James-Jiang0821/GLIDER/ROS2_TESTING/gnss_test_07-03-2026/all_topics.csv

topic | log_time_ns | type | message
/rosout | 1773075176267753863 | rcl_interfaces/msg/Log | Log(stamp=Time(sec=1773075176, nanosec=114152744), level=20, name=rosbag2_recorder, msg=Press SPACE for pausing/resuming, file=./src/rosbag2_transport/recorder.cpp, function=RecorderImpl, line=190)
/rosout | 1773075176267796273 | rcl_interfaces/msg/Log | Log(stamp=Time(sec=1773075176, nanosec=185886865), level=20, name=rosbag2_recorder, msg=Listening for topics..., file=./src/rosbag2_transport/recorder.cpp, function=record, line=353)
/rosout | 1773075176267808681 | rcl_interfaces/msg/Log | Log(stamp=Time(sec=1773075176, nanosec=186019447), level=20, name=rosbag2_recorder, msg=Event publisher thread: Starting, file=./src/rosbag2_transport/recorder.cpp, function=event_publisher_thread_main, line=371)
/rosout | 1773075176267809329 | rcl_interfaces/msg/Log | Log(stamp=Time(sec=1773075176, nanosec=198314175), level=20, name=rosbag2_recorder, msg=Subscribed to topic '/rosout', file=./src/rosbag2_transport/recorder.cpp, function=subscribe_topic, line=574)
/rosout | 1773075176267809792 | rcl_interfaces/msg/Log | Log(stamp=Time(sec=1773075176, nanosec=205440616), level=20, name=rosbag2_recorder, msg=Subscribed to topic '/parameter_events', file=./src/rosbag2_transport/recorder.cpp, function=subscribe_topic, line=574)
/rosout | 1773075176267810237 | rcl_interfaces/msg/Log | Log(stamp=Time(sec=1773075176, nanosec=246401098), level=20, name=rosbag2_recorder, msg=Subscribed to topic '/gps/vel', file=./src/rosbag2_transport/recorder.cpp, function=subscribe_topic, line=574)
/rosout | 1773075176275671092 | rcl_interfaces/msg/Log | Log(stamp=Time(sec=1773075176, nanosec=274873692), level=20, name=rosbag2_recorder, msg=Subscribed to topic '/gps/fix', file=./src/rosbag2_transport/recorder.cpp, function=subscribe_topic, line=574)
/gps/fix | 1773075176279690070 | sensor_msgs/msg/NavSatFix | NavSatFix(header=Header(stamp=Time(sec=1773075176, nanosec=278862577), frame_id=gps_link), status=NavSatStatus(status=0, service=1), latitude=51.476749299999994, longitude=-0.036789499999999996, altitude=6.122, position_covariance=[0.44488900000000003, 0.0, 0.0, 0.0, 0.44488900000000003, 0.0, 0.0, 0.0, 0.549081], position_covariance_type=2)
/gps/vel | 1773075176279978069 | geometry_msgs/msg/TwistStamped | TwistStamped(header=Header(stamp=Time(sec=1773075176, nanosec=278862577), frame_id=gps_link), twist=Twist(linear=Vector3(x=0.009, y=-0.013, z=0.001), angular=Vector3(x=0.0, y=0.0, z=0.0)))
/rosout | 1773075176301733450 | rcl_interfaces/msg/Log | Log(stamp=Time(sec=1773075176, nanosec=301534402), level=20, name=rosbag2_recorder, msg=Subscribed to topic '/gps/diagnostics', file=./src/rosbag2_transport/recorder.cpp, function=subscribe_topic, line=574)
/rosout | 1773075176308117218 | rcl_interfaces/msg/Log | Log(stamp=Time(sec=1773075176, nanosec=307944467), level=20, name=rosbag2_recorder, msg=Subscribed to topic '/events/write_split', file=./src/rosbag2_transport/recorder.cpp, function=subscribe_topic, line=574)
/rosout | 1773075176308825204 | rcl_interfaces/msg/Log | Log(stamp=Time(sec=1773075176, nanosec=308672102), level=20, name=rosbag2_recorder, msg=Recording..., file=./src/rosbag2_transport/recorder.cpp, function=record, line=365)
/gps/diagnostics | 1773075176682381984 | diagnostic_msgs/msg/DiagnosticArray | DiagnosticArray(header=Header(stamp=Time(sec=1773075176, nanosec=681566306), frame_id=), status=[DiagnosticStatus(level=0, name=gnss_maxm10s_i2c, message=OK, hardware_id=, values=[KeyValue(key=i2c_addr, value=0x42), KeyValue(key=avail_bytes_last_poll, value=0), KeyValue(key=age_s_since_last_pvt, value=0.40)])])
/gps/fix | 1773075177319579433 | sensor_msgs/msg/NavSatFix | NavSatFix(header=Header(stamp=Time(sec=1773075177, nanosec=318641104), frame_id=gps_link), status=NavSatStatus(status=0, service=1), latitude=51.4767465, longitude=-0.0367898, altitude=6.153, position_covariance=[0.42510400000000004, 0.0, 0.0, 0.0, 0.42510400000000004, 0.0, 0.0, 0.0, 0.5476], position_covariance_type=2)
/gps/vel | 1773075177320142111 | geometry_msgs/msg/TwistStamped | TwistStamped(header=Header(stamp=Time(sec=1773075177, nanosec=318641104), frame_id=gps_link), twist=Twist(linear=Vector3(x=0.006, y=-0.018, z=0.017), angular=Vector3(x=0.0, y=0.0, z=0.0)))
/gps/fix | 1773075178324664052 | sensor_msgs/msg/NavSatFix | NavSatFix(header=Header(stamp=Time(sec=1773075178, nanosec=323694653), frame_id=gps_link), status=NavSatStatus(status=0, service=1), latitude=51.4767467, longitude=-0.036789999999999996, altitude=6.231, position_covariance=[0.418609, 0.0, 0.0, 0.0, 0.418609, 0.0, 0.0, 0.0, 0.540225], position_covariance_type=2)
/gps/vel | 1773075178325083165 | geometry_msgs/msg/TwistStamped | TwistStamped(header=Header(stamp=Time(sec=1773075178, nanosec=323694653), frame_id=gps_link), twist=Twist(linear=Vector3(x=-0.004, y=-0.003, z=0.009), angular=Vector3(x=0.0, y=0.0, z=0.0)))
/gps/diagnostics | 1773075178325927132 | diagnostic_msgs/msg/DiagnosticArray | DiagnosticArray(header=Header(stamp=Time(sec=1773075178, nanosec=325338196), frame_id=), status=[DiagnosticStatus(level=0, name=gnss_maxm10s_i2c, message=OK, hardware_id=, values=[KeyValue(key=i2c_addr, value=0x42), KeyValue(key=avail_bytes_last_poll, value=100), KeyValue(key=age_s_since_last_pvt, value=0.00)])])
/gps/fix | 1773075179575138285 | sensor_msgs/msg/NavSatFix | NavSatFix(header=Header(stamp=Time(sec=1773075179, nanosec=574176854), frame_id=gps_link), status=NavSatStatus(status=0, service=1), latitude=51.4767471, longitude=-0.0367898, altitude=6.245, position_covariance=[0.41602500000000003, 0.0, 0.0, 0.0, 0.41602500000000003, 0.0, 0.0, 0.0, 0.535824], position_covariance_type=2)
/gps/vel | 1773075179575577231 | geometry_msgs/msg/TwistStamped | TwistStamped(header=Header(stamp=Time(sec=1773075179, nanosec=574176854), frame_id=gps_link), twist=Twist(linear=Vector3(x=-0.02, y=0.027, z=-0.0), angular=Vector3(x=0.0, y=0.0, z=0.0)))
/gps/fix | 1773075180360670753 | sensor_msgs/msg/NavSatFix | NavSatFix(header=Header(stamp=Time(sec=1773075180, nanosec=359713105), frame_id=gps_link), status=NavSatStatus(status=0, service=1), latitude=51.4767477, longitude=-0.0367901, altitude=6.276, position_covariance=[0.4096, 0.0, 0.0, 0.0, 0.4096, 0.0, 0.0, 0.0, 0.527076], position_covariance_type=2)
/gps/vel | 1773075180361079047 | geometry_msgs/msg/TwistStamped | TwistStamped(header=Header(stamp=Time(sec=1773075180, nanosec=359713105), frame_id=gps_link), twist=Twist(linear=Vector3(x=-0.012, y=0.021, z=-0.015), angular=Vector3(x=0.0, y=0.0, z=0.0)))
/gps/fix | 1773075181483030007 | sensor_msgs/msg/NavSatFix | NavSatFix(header=Header(stamp=Time(sec=1773075181, nanosec=482054844), frame_id=gps_link), status=NavSatStatus(status=0, service=1), latitude=51.4767489, longitude=-0.0367898, altitude=6.306, position_covariance=[0.403225, 0.0, 0.0, 0.0, 0.403225, 0.0, 0.0, 0.0, 0.524176], position_covariance_type=2)
/gps/vel | 1773075181483443521 | geometry_msgs/msg/TwistStamped | TwistStamped(header=Header(stamp=Time(sec=1773075181, nanosec=482054844), frame_id=gps_link), twist=Twist(linear=Vector3(x=-0.018, y=0.031, z=-0.003), angular=Vector3(x=0.0, y=0.0, z=0.0)))
/gps/fix | 1773075182256259807 | sensor_msgs/msg/NavSatFix | NavSatFix(header=Header(stamp=Time(sec=1773075182, nanosec=255231499), frame_id=gps_link), status=NavSatStatus(status=0, service=1), latitude=51.4767498, longitude=-0.036788999999999995, altitude=6.236, position_covariance=[0.398161, 0.0, 0.0, 0.0, 0.398161, 0.0, 0.0, 0.0, 0.512656], position_covariance_type=2)
/gps/vel | 1773075182256685746 | geometry_msgs/msg/TwistStamped | TwistStamped(header=Header(stamp=Time(sec=1773075182, nanosec=255231499), frame_id=gps_link), twist=Twist(linear=Vector3(x=-0.019, y=0.032, z=-0.013), angular=Vector3(x=0.0, y=0.0, z=0.0)))
/gps/fix | 1773075183410505809 | sensor_msgs/msg/NavSatFix | NavSatFix(header=Header(stamp=Time(sec=1773075183, nanosec=409542043), frame_id=gps_link), status=NavSatStatus(status=0, service=1), latitude=51.476751799999995, longitude=-0.0367877, altitude=6.231, position_covariance=[0.386884, 0.0, 0.0, 0.0, 0.386884, 0.0, 0.0, 0.0, 0.5041], position_covariance_type=2)
/gps/vel | 1773075183410922875 | geometry_msgs/msg/TwistStamped | TwistStamped(header=Header(stamp=Time(sec=1773075183, nanosec=409542043), frame_id=gps_link), twist=Twist(linear=Vector3(x=0.0, y=-0.006, z=-0.009), angular=Vector3(x=0.0, y=0.0, z=0.0)))
/gps/fix | 1773075184532103208 | sensor_msgs/msg/NavSatFix | NavSatFix(header=Header(stamp=Time(sec=1773075184, nanosec=531132298), frame_id=gps_link), status=NavSatStatus(status=0, service=1), latitude=51.4767521, longitude=-0.0367876, altitude=6.212, position_covariance=[0.3844, 0.0, 0.0, 0.0, 0.3844, 0.0, 0.0, 0.0, 0.4914009999999999], position_covariance_type=2)
/gps/vel | 1773075184532553754 | geometry_msgs/msg/TwistStamped | TwistStamped(header=Header(stamp=Time(sec=1773075184, nanosec=531132298), frame_id=gps_link), twist=Twist(linear=Vector3(x=0.001, y=-0.006, z=-0.006), angular=Vector3(x=0.0, y=0.0, z=0.0)))
/gps/fix | 1773075186392691532 | sensor_msgs/msg/NavSatFix | NavSatFix(header=Header(stamp=Time(sec=1773075186, nanosec=391800354), frame_id=gps_link), status=NavSatStatus(status=0, service=1), latitude=51.4767528, longitude=-0.036787799999999996, altitude=6.299, position_covariance=[0.381924, 0.0, 0.0, 0.0, 0.381924, 0.0, 0.0, 0.0, 0.48999999999999994], position_covariance_type=2)
/gps/vel | 1773075186393330059 | geometry_msgs/msg/TwistStamped | TwistStamped(header=Header(stamp=Time(sec=1773075186, nanosec=391800354), frame_id=gps_link), twist=Twist(linear=Vector3(x=-0.001, y=-0.01, z=0.002), angular=Vector3(x=0.0, y=0.0, z=0.0)))
/gps/fix | 1773075188512592137 | sensor_msgs/msg/NavSatFix | NavSatFix(header=Header(stamp=Time(sec=1773075188, nanosec=511513798), frame_id=gps_link), status=NavSatStatus(status=0, service=1), latitude=51.4767533, longitude=-0.036787099999999996, altitude=6.353, position_covariance=[0.394384, 0.0, 0.0, 0.0, 0.394384, 0.0, 0.0, 0.0, 0.505521], position_covariance_type=2)
/gps/vel | 1773075188513144603 | geometry_msgs/msg/TwistStamped | TwistStamped(header=Header(stamp=Time(sec=1773075188, nanosec=511513798), frame_id=gps_link), twist=Twist(linear=Vector3(x=-0.004, y=-0.017, z=-0.019), angular=Vector3(x=0.0, y=0.0, z=0.0)))
/gps/fix | 1773075189256715920 | sensor_msgs/msg/NavSatFix | NavSatFix(header=Header(stamp=Time(sec=1773075189, nanosec=255613936), frame_id=gps_link), status=NavSatStatus(status=0, service=1), latitude=51.4767535, longitude=-0.0367868, altitude=6.377, position_covariance=[0.398161, 0.0, 0.0, 0.0, 0.398161, 0.0, 0.0, 0.0, 0.5184], position_covariance_type=2)
/gps/vel | 1773075189257145272 | geometry_msgs/msg/TwistStamped | TwistStamped(header=Header(stamp=Time(sec=1773075189, nanosec=255613936), frame_id=gps_link), twist=Twist(linear=Vector3(x=0.004, y=-0.018, z=-0.001), angular=Vector3(x=0.0, y=0.0, z=0.0)))
/gps/fix | 1773075190326882189 | sensor_msgs/msg/NavSatFix | NavSatFix(header=Header(stamp=Time(sec=1773075190, nanosec=325930839), frame_id=gps_link), status=NavSatStatus(status=0, service=1), latitude=51.4767538, longitude=-0.0367867, altitude=6.434, position_covariance=[0.405769, 0.0, 0.0, 0.0, 0.405769, 0.0, 0.0, 0.0, 0.5314409999999999], position_covariance_type=2)
/gps/vel | 1773075190327313040 | geometry_msgs/msg/TwistStamped | TwistStamped(header=Header(stamp=Time(sec=1773075190, nanosec=325930839), frame_id=gps_link), twist=Twist(linear=Vector3(x=-0.016, y=-0.006, z=0.048), angular=Vector3(x=0.0, y=0.0, z=0.0)))
/gps/fix | 1773075192250818999 | sensor_msgs/msg/NavSatFix | NavSatFix(header=Header(stamp=Time(sec=1773075192, nanosec=250206430), frame_id=gps_link), status=NavSatStatus(status=0, service=1), latitude=51.4767552, longitude=-0.0367868, altitude=6.494, position_covariance=[0.417316, 0.0, 0.0, 0.0, 0.417316, 0.0, 0.0, 0.0, 0.556516], position_covariance_type=2)
/gps/vel | 1773075192251108238 | geometry_msgs/msg/TwistStamped | TwistStamped(header=Header(stamp=Time(sec=1773075192, nanosec=250206430), frame_id=gps_link), twist=Twist(linear=Vector3(x=0.007, y=0.011, z=0.026), angular=Vector3(x=0.0, y=0.0, z=0.0)))
/parameter_events | 1773075192894638845 | rcl_interfaces/msg/ParameterEvent | ParameterEvent(stamp=Time(sec=1773075192, nanosec=893949888), node=/_ros2cli_1362, new_parameters=[Parameter(name=use_sim_time, value=ParameterValue(type=1, bool_value=False, integer_value=0, double_value=0.0, string_value=, byte_array_value=b'', bool_array_value=[], integer_array_value=[], double_array_value=[], string_array_value=[]))], changed_parameters=[], deleted_parameters=[])
/parameter_events | 1773075192895375209 | rcl_interfaces/msg/ParameterEvent | ParameterEvent(stamp=Time(sec=1773075192, nanosec=894891380), node=/_ros2cli_1362, new_parameters=[Parameter(name=start_type_description_service, value=ParameterValue(type=1, bool_value=True, integer_value=0, double_value=0.0, string_value=, byte_array_value=b'', bool_array_value=[], integer_array_value=[], double_array_value=[], string_array_value=[]))], changed_parameters=[], deleted_parameters=[])
/gps/fix | 1773075193332485841 | sensor_msgs/msg/NavSatFix | NavSatFix(header=Header(stamp=Time(sec=1773075193, nanosec=331677165), frame_id=gps_link), status=NavSatStatus(status=0, service=1), latitude=51.4767558, longitude=-0.0367867, altitude=6.525, position_covariance=[0.43428100000000003, 0.0, 0.0, 0.0, 0.43428100000000003, 0.0, 0.0, 0.0, 0.574564], position_covariance_type=2)
/gps/vel | 1773075193333139278 | geometry_msgs/msg/TwistStamped | TwistStamped(header=Header(stamp=Time(sec=1773075193, nanosec=331677165), frame_id=gps_link), twist=Twist(linear=Vector3(x=-0.004, y=0.022, z=0.047), angular=Vector3(x=0.0, y=0.0, z=0.0)))
/gps/fix | 1773075194177165361 | sensor_msgs/msg/NavSatFix | NavSatFix(header=Header(stamp=Time(sec=1773075194, nanosec=176581684), frame_id=gps_link), status=NavSatStatus(status=0, service=1), latitude=51.476756599999995, longitude=-0.036787, altitude=6.555, position_covariance=[0.438244, 0.0, 0.0, 0.0, 0.438244, 0.0, 0.0, 0.0, 0.586756], position_covariance_type=2)
/gps/vel | 1773075194178440564 | geometry_msgs/msg/TwistStamped | TwistStamped(header=Header(stamp=Time(sec=1773075194, nanosec=176581684), frame_id=gps_link), twist=Twist(linear=Vector3(x=-0.01, y=0.01, z=0.025), angular=Vector3(x=0.0, y=0.0, z=0.0)))
/parameter_events | 1773075194542956376 | rcl_interfaces/msg/ParameterEvent | ParameterEvent(stamp=Time(sec=1773075194, nanosec=542249905), node=/_ros2cli_daemon_0_14923d5e72164b54a0d396fbd3f56f5b, new_parameters=[Parameter(name=use_sim_time, value=ParameterValue(type=1, bool_value=False, integer_value=0, double_value=0.0, string_value=, byte_array_value=b'', bool_array_value=[], integer_array_value=[], double_array_value=[], string_array_value=[]))], changed_parameters=[], deleted_parameters=[])
/parameter_events | 1773075194543657199 | rcl_interfaces/msg/ParameterEvent | ParameterEvent(stamp=Time(sec=1773075194, nanosec=543186095), node=/_ros2cli_daemon_0_14923d5e72164b54a0d396fbd3f56f5b, new_parameters=[Parameter(name=start_type_description_service, value=ParameterValue(type=1, bool_value=False, integer_value=0, double_value=0.0, string_value=, byte_array_value=b'', bool_array_value=[], integer_array_value=[], double_array_value=[], string_array_value=[]))], changed_parameters=[], deleted_parameters=[])
/gps/fix | 1773075195590996326 | sensor_msgs/msg/NavSatFix | NavSatFix(header=Header(stamp=Time(sec=1773075195, nanosec=589900012), frame_id=gps_link), status=NavSatStatus(status=0, service=1), latitude=51.476757199999994, longitude=-0.0367872, altitude=6.639, position_covariance=[0.438244, 0.0, 0.0, 0.0, 0.438244, 0.0, 0.0, 0.0, 0.571536], position_covariance_type=2)
/gps/vel | 1773075195591612945 | geometry_msgs/msg/TwistStamped | TwistStamped(header=Header(stamp=Time(sec=1773075195, nanosec=589900012), frame_id=gps_link), twist=Twist(linear=Vector3(x=0.0, y=-0.004, z=-0.003), angular=Vector3(x=0.0, y=0.0, z=0.0)))
/gps/fix | 1773075196326046522 | sensor_msgs/msg/NavSatFix | NavSatFix(header=Header(stamp=Time(sec=1773075196, nanosec=325157096), frame_id=gps_link), status=NavSatStatus(status=0, service=1), latitude=51.4767574, longitude=-0.0367867, altitude=6.682, position_covariance=[0.43033600000000005, 0.0, 0.0, 0.0, 0.43033600000000005, 0.0, 0.0, 0.0, 0.565504], position_covariance_type=2)
/gps/vel | 1773075196326765230 | geometry_msgs/msg/TwistStamped | TwistStamped(header=Header(stamp=Time(sec=1773075196, nanosec=325157096), frame_id=gps_link), twist=Twist(linear=Vector3(x=0.003, y=-0.007, z=0.004), angular=Vector3(x=0.0, y=0.0, z=0.0)))
/gps/fix | 1773075197480508623 | sensor_msgs/msg/NavSatFix | NavSatFix(header=Header(stamp=Time(sec=1773075197, nanosec=479530628), frame_id=gps_link), status=NavSatStatus(status=0, service=1), latitude=51.4767581, longitude=-0.0367868, altitude=6.718, position_covariance=[0.42510400000000004, 0.0, 0.0, 0.0, 0.42510400000000004, 0.0, 0.0, 0.0, 0.552049], position_covariance_type=2)
/gps/vel | 1773075197481051073 | geometry_msgs/msg/TwistStamped | TwistStamped(header=Header(stamp=Time(sec=1773075197, nanosec=479530628), frame_id=gps_link), twist=Twist(linear=Vector3(x=-0.001, y=-0.004, z=0.01), angular=Vector3(x=0.0, y=0.0, z=0.0)))
/gps/fix | 1773075198638917330 | sensor_msgs/msg/NavSatFix | NavSatFix(header=Header(stamp=Time(sec=1773075198, nanosec=637934726), frame_id=gps_link), status=NavSatStatus(status=0, service=1), latitude=51.4767586, longitude=-0.036787299999999995, altitude=6.695, position_covariance=[0.42250000000000004, 0.0, 0.0, 0.0, 0.42250000000000004, 0.0, 0.0, 0.0, 0.549081], position_covariance_type=2)
/gps/vel | 1773075198639714827 | geometry_msgs/msg/TwistStamped | TwistStamped(header=Header(stamp=Time(sec=1773075198, nanosec=637934726), frame_id=gps_link), twist=Twist(linear=Vector3(x=-0.009, y=-0.007, z=-0.008), angular=Vector3(x=0.0, y=0.0, z=0.0)))
/gps/fix | 1773075199389900629 | sensor_msgs/msg/NavSatFix | NavSatFix(header=Header(stamp=Time(sec=1773075199, nanosec=388930620), frame_id=gps_link), status=NavSatStatus(status=0, service=1), latitude=51.4767601, longitude=-0.0367882, altitude=6.654, position_covariance=[0.41473600000000005, 0.0, 0.0, 0.0, 0.41473600000000005, 0.0, 0.0, 0.0, 0.538756], position_covariance_type=2)
/gps/vel | 1773075199390495464 | geometry_msgs/msg/TwistStamped | TwistStamped(header=Header(stamp=Time(sec=1773075199, nanosec=388930620), frame_id=gps_link), twist=Twist(linear=Vector3(x=-0.01, y=-0.001, z=-0.029), angular=Vector3(x=0.0, y=0.0, z=0.0)))
/gps/fix | 1773075200532812806 | sensor_msgs/msg/NavSatFix | NavSatFix(header=Header(stamp=Time(sec=1773075200, nanosec=531825967), frame_id=gps_link), status=NavSatStatus(status=0, service=1), latitude=51.4767611, longitude=-0.036788799999999997, altitude=6.599, position_covariance=[0.410881, 0.0, 0.0, 0.0, 0.410881, 0.0, 0.0, 0.0, 0.5285289999999999], position_covariance_type=2)
/gps/vel | 1773075200533380399 | geometry_msgs/msg/TwistStamped | TwistStamped(header=Header(stamp=Time(sec=1773075200, nanosec=531825967), frame_id=gps_link), twist=Twist(linear=Vector3(x=-0.005, y=0.001, z=0.005), angular=Vector3(x=0.0, y=0.0, z=0.0)))
/gps/fix | 1773075201268630556 | sensor_msgs/msg/NavSatFix | NavSatFix(header=Header(stamp=Time(sec=1773075201, nanosec=267495113), frame_id=gps_link), status=NavSatStatus(status=0, service=1), latitude=51.4767625, longitude=-0.0367893, altitude=6.618, position_covariance=[0.4096, 0.0, 0.0, 0.0, 0.4096, 0.0, 0.0, 0.0, 0.522729], position_covariance_type=2)
/gps/vel | 1773075201269184815 | geometry_msgs/msg/TwistStamped | TwistStamped(header=Header(stamp=Time(sec=1773075201, nanosec=267495113), frame_id=gps_link), twist=Twist(linear=Vector3(x=-0.009, y=0.014, z=0.018), angular=Vector3(x=0.0, y=0.0, z=0.0)))
/gps/fix | 1773075202412350741 | sensor_msgs/msg/NavSatFix | NavSatFix(header=Header(stamp=Time(sec=1773075202, nanosec=411360814), frame_id=gps_link), status=NavSatStatus(status=0, service=1), latitude=51.4767635, longitude=-0.0367901, altitude=6.497, position_covariance=[0.405769, 0.0, 0.0, 0.0, 0.405769, 0.0, 0.0, 0.0, 0.5097959999999999], position_covariance_type=2)
/gps/vel | 1773075202413137712 | geometry_msgs/msg/TwistStamped | TwistStamped(header=Header(stamp=Time(sec=1773075202, nanosec=411360814), frame_id=gps_link), twist=Twist(linear=Vector3(x=-0.015, y=-0.002, z=-0.005), angular=Vector3(x=0.0, y=0.0, z=0.0)))
/gps/fix | 1773075203525921727 | sensor_msgs/msg/NavSatFix | NavSatFix(header=Header(stamp=Time(sec=1773075203, nanosec=524950617), frame_id=gps_link), status=NavSatStatus(status=0, service=1), latitude=51.4767643, longitude=-0.0367918, altitude=6.291, position_covariance=[0.403225, 0.0, 0.0, 0.0, 0.403225, 0.0, 0.0, 0.0, 0.5041], position_covariance_type=2)
/gps/vel | 1773075203526489094 | geometry_msgs/msg/TwistStamped | TwistStamped(header=Header(stamp=Time(sec=1773075203, nanosec=524950617), frame_id=gps_link), twist=Twist(linear=Vector3(x=-0.011, y=0.032, z=-0.028), angular=Vector3(x=0.0, y=0.0, z=0.0)))
/gps/fix | 1773075204486615209 | sensor_msgs/msg/NavSatFix | NavSatFix(header=Header(stamp=Time(sec=1773075204, nanosec=485646619), frame_id=gps_link), status=NavSatStatus(status=0, service=1), latitude=51.4767619, longitude=-0.0367928, altitude=6.261, position_covariance=[0.408321, 0.0, 0.0, 0.0, 0.408321, 0.0, 0.0, 0.0, 0.537289], position_covariance_type=2)
/gps/vel | 1773075204487162669 | geometry_msgs/msg/TwistStamped | TwistStamped(header=Header(stamp=Time(sec=1773075204, nanosec=485646619), frame_id=gps_link), twist=Twist(linear=Vector3(x=-0.054, y=-0.562, z=-0.067), angular=Vector3(x=0.0, y=0.0, z=0.0)))
/gps/fix | 1773075206537593513 | sensor_msgs/msg/NavSatFix | NavSatFix(header=Header(stamp=Time(sec=1773075206, nanosec=536610242), frame_id=gps_link), status=NavSatStatus(status=0, service=1), latitude=51.4767632, longitude=-0.036789999999999996, altitude=5.983, position_covariance=[0.527076, 0.0, 0.0, 0.0, 0.527076, 0.0, 0.0, 0.0, 0.6384010000000001], position_covariance_type=2)
/gps/vel | 1773075206538325202 | geometry_msgs/msg/TwistStamped | TwistStamped(header=Header(stamp=Time(sec=1773075206, nanosec=536610242), frame_id=gps_link), twist=Twist(linear=Vector3(x=-0.041, y=0.164, z=-0.249), angular=Vector3(x=0.0, y=0.0, z=0.0)))
/gps/fix | 1773075207285232342 | sensor_msgs/msg/NavSatFix | NavSatFix(header=Header(stamp=Time(sec=1773075207, nanosec=284310275), frame_id=gps_link), status=NavSatStatus(status=0, service=1), latitude=51.4767654, longitude=-0.0367899, altitude=6.087, position_covariance=[0.522729, 0.0, 0.0, 0.0, 0.522729, 0.0, 0.0, 0.0, 0.664225], position_covariance_type=2)
/gps/vel | 1773075207285760521 | geometry_msgs/msg/TwistStamped | TwistStamped(header=Header(stamp=Time(sec=1773075207, nanosec=284310275), frame_id=gps_link), twist=Twist(linear=Vector3(x=-0.007, y=0.085, z=0.05), angular=Vector3(x=0.0, y=0.0, z=0.0)))
/gps/fix | 1773075208330469221 | sensor_msgs/msg/NavSatFix | NavSatFix(header=Header(stamp=Time(sec=1773075208, nanosec=329590393), frame_id=gps_link), status=NavSatStatus(status=0, service=1), latitude=51.4767659, longitude=-0.0367934, altitude=6.191, position_covariance=[0.522729, 0.0, 0.0, 0.0, 0.522729, 0.0, 0.0, 0.0, 0.6691239999999999], position_covariance_type=2)
/gps/vel | 1773075208330979325 | geometry_msgs/msg/TwistStamped | TwistStamped(header=Header(stamp=Time(sec=1773075208, nanosec=329590393), frame_id=gps_link), twist=Twist(linear=Vector3(x=-0.22, y=-0.263, z=0.116), angular=Vector3(x=0.0, y=0.0, z=0.0)))
/gps/fix | 1773075209425174332 | sensor_msgs/msg/NavSatFix | NavSatFix(header=Header(stamp=Time(sec=1773075209, nanosec=424203456), frame_id=gps_link), status=NavSatStatus(status=0, service=1), latitude=51.476766, longitude=-0.0367962, altitude=6.328, position_covariance=[0.49420899999999995, 0.0, 0.0, 0.0, 0.49420899999999995, 0.0, 0.0, 0.0, 0.6528640000000001], position_covariance_type=2)
/gps/vel | 1773075209425749803 | geometry_msgs/msg/TwistStamped | TwistStamped(header=Header(stamp=Time(sec=1773075209, nanosec=424203456), frame_id=gps_link), twist=Twist(linear=Vector3(x=-0.033, y=-0.129, z=-0.021), angular=Vector3(x=0.0, y=0.0, z=0.0)))
/gps/fix | 1773075210520372236 | sensor_msgs/msg/NavSatFix | NavSatFix(header=Header(stamp=Time(sec=1773075210, nanosec=519372382), frame_id=gps_link), status=NavSatStatus(status=0, service=1), latitude=51.476768, longitude=-0.036798, altitude=6.403, position_covariance=[0.4830249999999999, 0.0, 0.0, 0.0, 0.4830249999999999, 0.0, 0.0, 0.0, 0.6691239999999999], position_covariance_type=2)
/gps/vel | 1773075210520875691 | geometry_msgs/msg/TwistStamped | TwistStamped(header=Header(stamp=Time(sec=1773075210, nanosec=519372382), frame_id=gps_link), twist=Twist(linear=Vector3(x=-0.005, y=0.003, z=-0.021), angular=Vector3(x=0.0, y=0.0, z=0.0)))
/gps/fix | 1773075211571509484 | sensor_msgs/msg/NavSatFix | NavSatFix(header=Header(stamp=Time(sec=1773075211, nanosec=570220185), frame_id=gps_link), status=NavSatStatus(status=0, service=1), latitude=51.4767697, longitude=-0.0367968, altitude=6.223, position_covariance=[0.48441599999999996, 0.0, 0.0, 0.0, 0.48441599999999996, 0.0, 0.0, 0.0, 0.6822759999999999], position_covariance_type=2)
/gps/vel | 1773075211572318903 | geometry_msgs/msg/TwistStamped | TwistStamped(header=Header(stamp=Time(sec=1773075211, nanosec=570220185), frame_id=gps_link), twist=Twist(linear=Vector3(x=0.124, y=0.145, z=-0.141), angular=Vector3(x=0.0, y=0.0, z=0.0)))
/gps/fix | 1773075212300494508 | sensor_msgs/msg/NavSatFix | NavSatFix(header=Header(stamp=Time(sec=1773075212, nanosec=299533840), frame_id=gps_link), status=NavSatStatus(status=0, service=1), latitude=51.4767728, longitude=-0.036795499999999995, altitude=6.33, position_covariance=[0.4802489999999999, 0.0, 0.0, 0.0, 0.4802489999999999, 0.0, 0.0, 0.0, 0.690561], position_covariance_type=2)
/gps/vel | 1773075212301043996 | geometry_msgs/msg/TwistStamped | TwistStamped(header=Header(stamp=Time(sec=1773075212, nanosec=299533840), frame_id=gps_link), twist=Twist(linear=Vector3(x=0.052, y=0.056, z=0.213), angular=Vector3(x=0.0, y=0.0, z=0.0)))
/gps/fix | 1773075213419946432 | sensor_msgs/msg/NavSatFix | NavSatFix(header=Header(stamp=Time(sec=1773075213, nanosec=419036319), frame_id=gps_link), status=NavSatStatus(status=0, service=1), latitude=51.476772399999994, longitude=-0.0367934, altitude=6.219, position_covariance=[0.4610410000000001, 0.0, 0.0, 0.0, 0.4610410000000001, 0.0, 0.0, 0.0, 0.664225], position_covariance_type=2)
/gps/vel | 1773075213420473642 | geometry_msgs/msg/TwistStamped | TwistStamped(header=Header(stamp=Time(sec=1773075213, nanosec=419036319), frame_id=gps_link), twist=Twist(linear=Vector3(x=0.029, y=0.062, z=0.07), angular=Vector3(x=0.0, y=0.0, z=0.0)))
/gps/fix | 1773075214522550462 | sensor_msgs/msg/NavSatFix | NavSatFix(header=Header(stamp=Time(sec=1773075214, nanosec=521562410), frame_id=gps_link), status=NavSatStatus(status=0, service=1), latitude=51.476772499999996, longitude=-0.0367923, altitude=5.989, position_covariance=[0.4529290000000001, 0.0, 0.0, 0.0, 0.4529290000000001, 0.0, 0.0, 0.0, 0.6384010000000001], position_covariance_type=2)
/gps/vel | 1773075214523109429 | geometry_msgs/msg/TwistStamped | TwistStamped(header=Header(stamp=Time(sec=1773075214, nanosec=521562410), frame_id=gps_link), twist=Twist(linear=Vector3(x=-0.109, y=0.051, z=-0.156), angular=Vector3(x=0.0, y=0.0, z=0.0)))
/gps/fix | 1773075215569599296 | sensor_msgs/msg/NavSatFix | NavSatFix(header=Header(stamp=Time(sec=1773075215, nanosec=568623949), frame_id=gps_link), status=NavSatStatus(status=0, service=1), latitude=51.4767716, longitude=-0.0367908, altitude=5.849, position_covariance=[0.43428100000000003, 0.0, 0.0, 0.0, 0.43428100000000003, 0.0, 0.0, 0.0, 0.6320250000000001], position_covariance_type=2)
/gps/vel | 1773075215570222184 | geometry_msgs/msg/TwistStamped | TwistStamped(header=Header(stamp=Time(sec=1773075215, nanosec=568623949), frame_id=gps_link), twist=Twist(linear=Vector3(x=0.036, y=-0.027, z=-0.168), angular=Vector3(x=0.0, y=0.0, z=0.0)))
/gps/fix | 1773075216229778395 | sensor_msgs/msg/NavSatFix | NavSatFix(header=Header(stamp=Time(sec=1773075216, nanosec=228811011), frame_id=gps_link), status=NavSatStatus(status=0, service=1), latitude=51.476772, longitude=-0.036789499999999996, altitude=5.706, position_covariance=[0.43164900000000006, 0.0, 0.0, 0.0, 0.43164900000000006, 0.0, 0.0, 0.0, 0.6496360000000001], position_covariance_type=2)
/gps/vel | 1773075216230329564 | geometry_msgs/msg/TwistStamped | TwistStamped(header=Header(stamp=Time(sec=1773075216, nanosec=228811011), frame_id=gps_link), twist=Twist(linear=Vector3(x=-0.003, y=-0.01, z=-0.05), angular=Vector3(x=0.0, y=0.0, z=0.0)))
/gps/fix | 1773075218281434766 | sensor_msgs/msg/NavSatFix | NavSatFix(header=Header(stamp=Time(sec=1773075218, nanosec=280455886), frame_id=gps_link), status=NavSatStatus(status=0, service=1), latitude=51.4767693, longitude=-0.0367896, altitude=5.652, position_covariance=[0.4802489999999999, 0.0, 0.0, 0.0, 0.4802489999999999, 0.0, 0.0, 0.0, 0.6822759999999999], position_covariance_type=2)
/gps/vel | 1773075218282369408 | geometry_msgs/msg/TwistStamped | TwistStamped(header=Header(stamp=Time(sec=1773075218, nanosec=280455886), frame_id=gps_link), twist=Twist(linear=Vector3(x=0.029, y=-0.003, z=-0.007), angular=Vector3(x=0.0, y=0.0, z=0.0)))
/gps/fix | 1773075219338883858 | sensor_msgs/msg/NavSatFix | NavSatFix(header=Header(stamp=Time(sec=1773075219, nanosec=337905035), frame_id=gps_link), status=NavSatStatus(status=0, service=1), latitude=51.476769, longitude=-0.0367886, altitude=5.625, position_covariance=[0.4802489999999999, 0.0, 0.0, 0.0, 0.4802489999999999, 0.0, 0.0, 0.0, 0.6839289999999999], position_covariance_type=2)
/gps/vel | 1773075219339410045 | geometry_msgs/msg/TwistStamped | TwistStamped(header=Header(stamp=Time(sec=1773075219, nanosec=337905035), frame_id=gps_link), twist=Twist(linear=Vector3(x=0.009, y=-0.009, z=0.003), angular=Vector3(x=0.0, y=0.0, z=0.0)))
/gps/fix | 1773075220431164584 | sensor_msgs/msg/NavSatFix | NavSatFix(header=Header(stamp=Time(sec=1773075220, nanosec=430306180), frame_id=gps_link), status=NavSatStatus(status=0, service=1), latitude=51.4767679, longitude=-0.036787799999999996, altitude=5.659, position_covariance=[0.48580899999999994, 0.0, 0.0, 0.0, 0.48580899999999994, 0.0, 0.0, 0.0, 0.6872409999999999], position_covariance_type=2)
/gps/vel | 1773075220431662031 | geometry_msgs/msg/TwistStamped | TwistStamped(header=Header(stamp=Time(sec=1773075220, nanosec=430306180), frame_id=gps_link), twist=Twist(linear=Vector3(x=0.006, y=-0.01, z=0.017), angular=Vector3(x=0.0, y=0.0, z=0.0)))
/gps/fix | 1773075221509362452 | sensor_msgs/msg/NavSatFix | NavSatFix(header=Header(stamp=Time(sec=1773075221, nanosec=508387113), frame_id=gps_link), status=NavSatStatus(status=0, service=1), latitude=51.4767624, longitude=-0.0367811, altitude=5.482, position_covariance=[4.721929, 0.0, 0.0, 0.0, 4.721929, 0.0, 0.0, 0.0, 0.7744], position_covariance_type=2)
/gps/vel | 1773075221510347272 | geometry_msgs/msg/TwistStamped | TwistStamped(header=Header(stamp=Time(sec=1773075221, nanosec=508387113), frame_id=gps_link), twist=Twist(linear=Vector3(x=0.011, y=-0.014, z=0.015), angular=Vector3(x=0.0, y=0.0, z=0.0)))
/gps/fix | 1773075223441869150 | sensor_msgs/msg/NavSatFix | NavSatFix(header=Header(stamp=Time(sec=1773075223, nanosec=440900054), frame_id=gps_link), status=NavSatStatus(status=0, service=1), latitude=51.4767613, longitude=-0.0367874, altitude=5.406, position_covariance=[2.347024, 0.0, 0.0, 0.0, 2.347024, 0.0, 0.0, 0.0, 0.6822759999999999], position_covariance_type=2)
/gps/vel | 1773075223442823988 | geometry_msgs/msg/TwistStamped | TwistStamped(header=Header(stamp=Time(sec=1773075223, nanosec=440900054), frame_id=gps_link), twist=Twist(linear=Vector3(x=-0.014, y=0.034, z=0.141), angular=Vector3(x=0.0, y=0.0, z=0.0)))
/gps/diagnostics | 1773075223580629614 | diagnostic_msgs/msg/DiagnosticArray | DiagnosticArray(header=Header(stamp=Time(sec=1773075223, nanosec=579862744), frame_id=), status=[DiagnosticStatus(level=0, name=gnss_maxm10s_i2c, message=OK, hardware_id=, values=[KeyValue(key=i2c_addr, value=0x42), KeyValue(key=avail_bytes_last_poll, value=32868), KeyValue(key=age_s_since_last_pvt, value=0.14)])])
/gps/fix | 1773075224330572766 | sensor_msgs/msg/NavSatFix | NavSatFix(header=Header(stamp=Time(sec=1773075224, nanosec=329625188), frame_id=gps_link), status=NavSatStatus(status=0, service=1), latitude=51.4767624, longitude=-0.0367867, altitude=5.371, position_covariance=[1.8714240000000002, 0.0, 0.0, 0.0, 1.8714240000000002, 0.0, 0.0, 0.0, 0.664225], position_covariance_type=2)
/gps/vel | 1773075224331131280 | geometry_msgs/msg/TwistStamped | TwistStamped(header=Header(stamp=Time(sec=1773075224, nanosec=329625188), frame_id=gps_link), twist=Twist(linear=Vector3(x=-0.01, y=0.013, z=0.002), angular=Vector3(x=0.0, y=0.0, z=0.0)))
/gps/diagnostics | 1773075224683853142 | diagnostic_msgs/msg/DiagnosticArray | DiagnosticArray(header=Header(stamp=Time(sec=1773075224, nanosec=683025944), frame_id=), status=[DiagnosticStatus(level=0, name=gnss_maxm10s_i2c, message=OK, hardware_id=, values=[KeyValue(key=i2c_addr, value=0x42), KeyValue(key=avail_bytes_last_poll, value=0), KeyValue(key=age_s_since_last_pvt, value=0.35)])])
/gps/fix | 1773075225341497017 | sensor_msgs/msg/NavSatFix | NavSatFix(header=Header(stamp=Time(sec=1773075225, nanosec=340551773), frame_id=gps_link), status=NavSatStatus(status=0, service=1), latitude=51.4767624, longitude=-0.0367848, altitude=5.31, position_covariance=[1.5376, 0.0, 0.0, 0.0, 1.5376, 0.0, 0.0, 0.0, 0.6496360000000001], position_covariance_type=2)
/gps/vel | 1773075225342078529 | geometry_msgs/msg/TwistStamped | TwistStamped(header=Header(stamp=Time(sec=1773075225, nanosec=340551773), frame_id=gps_link), twist=Twist(linear=Vector3(x=0.003, y=-0.005, z=-0.028), angular=Vector3(x=0.0, y=0.0, z=0.0)))
/gps/diagnostics | 1773075226338603674 | diagnostic_msgs/msg/DiagnosticArray | DiagnosticArray(header=Header(stamp=Time(sec=1773075226, nanosec=337886321), frame_id=), status=[DiagnosticStatus(level=0, name=gnss_maxm10s_i2c, message=OK, hardware_id=, values=[KeyValue(key=i2c_addr, value=0x42), KeyValue(key=avail_bytes_last_poll, value=100), KeyValue(key=age_s_since_last_pvt, value=1.00)])])
/gps/diagnostics | 1773075227681137056 | diagnostic_msgs/msg/DiagnosticArray | DiagnosticArray(header=Header(stamp=Time(sec=1773075227, nanosec=680444202), frame_id=), status=[DiagnosticStatus(level=1, name=gnss_maxm10s_i2c, message=No recent NAV-PVT, hardware_id=, values=[KeyValue(key=i2c_addr, value=0x42), KeyValue(key=avail_bytes_last_poll, value=0), KeyValue(key=age_s_since_last_pvt, value=2.34)])])
/gps/fix | 1773075228335353838 | sensor_msgs/msg/NavSatFix | NavSatFix(header=Header(stamp=Time(sec=1773075228, nanosec=334373148), frame_id=gps_link), status=NavSatStatus(status=0, service=1), latitude=51.4767593, longitude=-0.0367811, altitude=5.288, position_covariance=[0.996004, 0.0, 0.0, 0.0, 0.996004, 0.0, 0.0, 0.0, 0.6577210000000001], position_covariance_type=2)
/gps/vel | 1773075228335867191 | geometry_msgs/msg/TwistStamped | TwistStamped(header=Header(stamp=Time(sec=1773075228, nanosec=334373148), frame_id=gps_link), twist=Twist(linear=Vector3(x=-0.002, y=-0.017, z=0.02), angular=Vector3(x=0.0, y=0.0, z=0.0)))
/gps/fix | 1773075229336392195 | sensor_msgs/msg/NavSatFix | NavSatFix(header=Header(stamp=Time(sec=1773075229, nanosec=335433433), frame_id=gps_link), status=NavSatStatus(status=0, service=1), latitude=51.4767582, longitude=-0.0367806, altitude=5.215, position_covariance=[0.9158489999999999, 0.0, 0.0, 0.0, 0.9158489999999999, 0.0, 0.0, 0.0, 0.6806249999999999], position_covariance_type=2)
/gps/vel | 1773075229337100866 | geometry_msgs/msg/TwistStamped | TwistStamped(header=Header(stamp=Time(sec=1773075229, nanosec=335433433), frame_id=gps_link), twist=Twist(linear=Vector3(x=-0.008, y=-0.003, z=0.006), angular=Vector3(x=0.0, y=0.0, z=0.0)))
/gps/diagnostics | 1773075229337927256 | diagnostic_msgs/msg/DiagnosticArray | DiagnosticArray(header=Header(stamp=Time(sec=1773075229, nanosec=337142693), frame_id=), status=[DiagnosticStatus(level=0, name=gnss_maxm10s_i2c, message=OK, hardware_id=, values=[KeyValue(key=i2c_addr, value=0x42), KeyValue(key=avail_bytes_last_poll, value=100), KeyValue(key=age_s_since_last_pvt, value=0.00)])])
/gps/fix | 1773075230330391385 | sensor_msgs/msg/NavSatFix | NavSatFix(header=Header(stamp=Time(sec=1773075230, nanosec=329394969), frame_id=gps_link), status=NavSatStatus(status=0, service=1), latitude=51.476758499999995, longitude=-0.036780799999999995, altitude=5.344, position_covariance=[0.8372250000000001, 0.0, 0.0, 0.0, 0.8372250000000001, 0.0, 0.0, 0.0, 0.6889], position_covariance_type=2)
/gps/vel | 1773075230330953176 | geometry_msgs/msg/TwistStamped | TwistStamped(header=Header(stamp=Time(sec=1773075230, nanosec=329394969), frame_id=gps_link), twist=Twist(linear=Vector3(x=0.014, y=0.001, z=0.037), angular=Vector3(x=0.0, y=0.0, z=0.0)))
/gps/diagnostics | 1773075230681158974 | diagnostic_msgs/msg/DiagnosticArray | DiagnosticArray(header=Header(stamp=Time(sec=1773075230, nanosec=680405702), frame_id=), status=[DiagnosticStatus(level=0, name=gnss_maxm10s_i2c, message=OK, hardware_id=, values=[KeyValue(key=i2c_addr, value=0x42), KeyValue(key=avail_bytes_last_poll, value=0), KeyValue(key=age_s_since_last_pvt, value=0.35)])])
/gps/fix | 1773075231331652066 | sensor_msgs/msg/NavSatFix | NavSatFix(header=Header(stamp=Time(sec=1773075231, nanosec=330761185), frame_id=gps_link), status=NavSatStatus(status=0, service=1), latitude=51.4767577, longitude=-0.036781, altitude=5.362, position_covariance=[0.790321, 0.0, 0.0, 0.0, 0.790321, 0.0, 0.0, 0.0, 0.6789759999999999], position_covariance_type=2)
/gps/vel | 1773075231332125885 | geometry_msgs/msg/TwistStamped | TwistStamped(header=Header(stamp=Time(sec=1773075231, nanosec=330761185), frame_id=gps_link), twist=Twist(linear=Vector3(x=0.028, y=-0.193, z=0.126), angular=Vector3(x=0.0, y=0.0, z=0.0)))
/gps/diagnostics | 1773075231681769832 | diagnostic_msgs/msg/DiagnosticArray | DiagnosticArray(header=Header(stamp=Time(sec=1773075231, nanosec=680938264), frame_id=), status=[DiagnosticStatus(level=0, name=gnss_maxm10s_i2c, message=OK, hardware_id=, values=[KeyValue(key=i2c_addr, value=0x42), KeyValue(key=avail_bytes_last_poll, value=0), KeyValue(key=age_s_since_last_pvt, value=0.35)])])
/gps/fix | 1773075232327587140 | sensor_msgs/msg/NavSatFix | NavSatFix(header=Header(stamp=Time(sec=1773075232, nanosec=326567321), frame_id=gps_link), status=NavSatStatus(status=0, service=1), latitude=51.476755999999995, longitude=-0.036779599999999996, altitude=5.374, position_covariance=[0.779689, 0.0, 0.0, 0.0, 0.779689, 0.0, 0.0, 0.0, 0.6872409999999999], position_covariance_type=2)
/gps/vel | 1773075232328162151 | geometry_msgs/msg/TwistStamped | TwistStamped(header=Header(stamp=Time(sec=1773075232, nanosec=326567321), frame_id=gps_link), twist=Twist(linear=Vector3(x=0.174, y=-0.061, z=-0.054), angular=Vector3(x=0.0, y=0.0, z=0.0)))
/gps/fix | 1773075233314358646 | sensor_msgs/msg/NavSatFix | NavSatFix(header=Header(stamp=Time(sec=1773075233, nanosec=313447547), frame_id=gps_link), status=NavSatStatus(status=0, service=1), latitude=51.476755999999995, longitude=-0.036778, altitude=5.346, position_covariance=[0.788544, 0.0, 0.0, 0.0, 0.788544, 0.0, 0.0, 0.0, 0.712336], position_covariance_type=2)
/gps/vel | 1773075233315149824 | geometry_msgs/msg/TwistStamped | TwistStamped(header=Header(stamp=Time(sec=1773075233, nanosec=313447547), frame_id=gps_link), twist=Twist(linear=Vector3(x=0.008, y=-0.001, z=0.055), angular=Vector3(x=0.0, y=0.0, z=0.0)))
/gps/diagnostics | 1773075233315858608 | diagnostic_msgs/msg/DiagnosticArray | DiagnosticArray(header=Header(stamp=Time(sec=1773075233, nanosec=315097365), frame_id=), status=[DiagnosticStatus(level=0, name=gnss_maxm10s_i2c, message=OK, hardware_id=, values=[KeyValue(key=i2c_addr, value=0x42), KeyValue(key=avail_bytes_last_poll, value=100), KeyValue(key=age_s_since_last_pvt, value=0.00)])])
/gps/fix | 1773075234317972675 | sensor_msgs/msg/NavSatFix | NavSatFix(header=Header(stamp=Time(sec=1773075234, nanosec=317008085), frame_id=gps_link), status=NavSatStatus(status=0, service=1), latitude=51.476757199999994, longitude=-0.0367783, altitude=8394.023, position_covariance=[0.817216, 0.0, 0.0, 0.0, 0.817216, 0.0, 0.0, 0.0, 0.781456], position_covariance_type=2)
/gps/vel | 1773075234318628738 | geometry_msgs/msg/TwistStamped | TwistStamped(header=Header(stamp=Time(sec=1773075234, nanosec=317008085), frame_id=gps_link), twist=Twist(linear=Vector3(x=-0.038, y=-0.012, z=0.134), angular=Vector3(x=0.0, y=0.0, z=0.0)))
/gps/diagnostics | 1773075234319614630 | diagnostic_msgs/msg/DiagnosticArray | DiagnosticArray(header=Header(stamp=Time(sec=1773075234, nanosec=318867469), frame_id=), status=[DiagnosticStatus(level=0, name=gnss_maxm10s_i2c, message=OK, hardware_id=, values=[KeyValue(key=i2c_addr, value=0x42), KeyValue(key=avail_bytes_last_poll, value=100), KeyValue(key=age_s_since_last_pvt, value=0.00)])])
/gps/fix | 1773075235320615546 | sensor_msgs/msg/NavSatFix | NavSatFix(header=Header(stamp=Time(sec=1773075235, nanosec=319648831), frame_id=gps_link), status=NavSatStatus(status=0, service=1), latitude=51.4767601, longitude=-0.0367792, altitude=5.436, position_covariance=[0.8464, 0.0, 0.0, 0.0, 0.8464, 0.0, 0.0, 0.0, 0.851929], position_covariance_type=2)
/gps/vel | 1773075235321442891 | geometry_msgs/msg/TwistStamped | TwistStamped(header=Header(stamp=Time(sec=1773075235, nanosec=319648831), frame_id=gps_link), twist=Twist(linear=Vector3(x=-0.023, y=0.12, z=0.135), angular=Vector3(x=0.0, y=0.0, z=0.0)))
/gps/diagnostics | 1773075235322243971 | diagnostic_msgs/msg/DiagnosticArray | DiagnosticArray(header=Header(stamp=Time(sec=1773075235, nanosec=321410049), frame_id=), status=[DiagnosticStatus(level=0, name=gnss_maxm10s_i2c, message=OK, hardware_id=, values=[KeyValue(key=i2c_addr, value=0x42), KeyValue(key=avail_bytes_last_poll, value=100), KeyValue(key=age_s_since_last_pvt, value=0.00)])])
/gps/fix | 1773075236320791152 | sensor_msgs/msg/NavSatFix | NavSatFix(header=Header(stamp=Time(sec=1773075236, nanosec=319835037), frame_id=gps_link), status=NavSatStatus(status=0, service=1), latitude=51.476762699999995, longitude=-0.0367727, altitude=5.371, position_covariance=[0.8835999999999999, 0.0, 0.0, 0.0, 0.8835999999999999, 0.0, 0.0, 0.0, 0.9467289999999999], position_covariance_type=2)
/gps/vel | 1773075236321532249 | geometry_msgs/msg/TwistStamped | TwistStamped(header=Header(stamp=Time(sec=1773075236, nanosec=319835037), frame_id=gps_link), twist=Twist(linear=Vector3(x=0.503, y=0.206, z=-0.007), angular=Vector3(x=0.0, y=0.0, z=0.0)))
/gps/diagnostics | 1773075236322183711 | diagnostic_msgs/msg/DiagnosticArray | DiagnosticArray(header=Header(stamp=Time(sec=1773075236, nanosec=321528933), frame_id=), status=[DiagnosticStatus(level=0, name=gnss_maxm10s_i2c, message=OK, hardware_id=, values=[KeyValue(key=i2c_addr, value=0x42), KeyValue(key=avail_bytes_last_poll, value=100), KeyValue(key=age_s_since_last_pvt, value=0.00)])])
/gps/fix | 1773075237333080362 | sensor_msgs/msg/NavSatFix | NavSatFix(header=Header(stamp=Time(sec=1773075237, nanosec=332101673), frame_id=gps_link), status=NavSatStatus(status=0, service=1), latitude=51.4767653, longitude=-0.036763699999999996, altitude=5.544, position_covariance=[1.0, 0.0, 0.0, 0.0, 1.0, 0.0, 0.0, 0.0, 1.1534760000000002], position_covariance_type=2)
/gps/vel | 1773075237333654821 | geometry_msgs/msg/TwistStamped | TwistStamped(header=Header(stamp=Time(sec=1773075237, nanosec=332101673), frame_id=gps_link), twist=Twist(linear=Vector3(x=0.766, y=0.248, z=0.151), angular=Vector3(x=0.0, y=0.0, z=0.0)))
/gps/diagnostics | 1773075237334701787 | diagnostic_msgs/msg/DiagnosticArray | DiagnosticArray(header=Header(stamp=Time(sec=1773075237, nanosec=333892399), frame_id=), status=[DiagnosticStatus(level=0, name=gnss_maxm10s_i2c, message=OK, hardware_id=, values=[KeyValue(key=i2c_addr, value=0x42), KeyValue(key=avail_bytes_last_poll, value=100), KeyValue(key=age_s_since_last_pvt, value=0.00)])])
/gps/fix | 1773075238332243377 | sensor_msgs/msg/NavSatFix | NavSatFix(header=Header(stamp=Time(sec=1773075238, nanosec=331112989), frame_id=gps_link), status=NavSatStatus(status=0, service=1), latitude=51.4767648, longitude=-0.0367559, altitude=5.719, position_covariance=[1.044484, 0.0, 0.0, 0.0, 1.044484, 0.0, 0.0, 0.0, 1.3087359999999997], position_covariance_type=2)
/gps/vel | 1773075238333165771 | geometry_msgs/msg/TwistStamped | TwistStamped(header=Header(stamp=Time(sec=1773075238, nanosec=331112989), frame_id=gps_link), twist=Twist(linear=Vector3(x=0.68, y=-0.401, z=0.045), angular=Vector3(x=0.0, y=0.0, z=0.0)))
/gps/diagnostics | 1773075238682340560 | diagnostic_msgs/msg/DiagnosticArray | DiagnosticArray(header=Header(stamp=Time(sec=1773075238, nanosec=681589060), frame_id=), status=[DiagnosticStatus(level=0, name=gnss_maxm10s_i2c, message=OK, hardware_id=, values=[KeyValue(key=i2c_addr, value=0x42), KeyValue(key=avail_bytes_last_poll, value=0), KeyValue(key=age_s_since_last_pvt, value=0.35)])])
/gps/fix | 1773075239329243000 | sensor_msgs/msg/NavSatFix | NavSatFix(header=Header(stamp=Time(sec=1773075239, nanosec=328259301), frame_id=gps_link), status=NavSatStatus(status=0, service=1), latitude=51.4767608, longitude=-0.0367524, altitude=5.653, position_covariance=[1.1363560000000001, 0.0, 0.0, 0.0, 1.1363560000000001, 0.0, 0.0, 0.0, 1.5450490000000003], position_covariance_type=2)
/gps/vel | 1773075239329778685 | geometry_msgs/msg/TwistStamped | TwistStamped(header=Header(stamp=Time(sec=1773075239, nanosec=328259301), frame_id=gps_link), twist=Twist(linear=Vector3(x=-0.001, y=-0.311, z=-0.231), angular=Vector3(x=0.0, y=0.0, z=0.0)))
/gps/diagnostics | 1773075239683009011 | diagnostic_msgs/msg/DiagnosticArray | DiagnosticArray(header=Header(stamp=Time(sec=1773075239, nanosec=682382434), frame_id=), status=[DiagnosticStatus(level=0, name=gnss_maxm10s_i2c, message=OK, hardware_id=, values=[KeyValue(key=i2c_addr, value=0x42), KeyValue(key=avail_bytes_last_poll, value=0), KeyValue(key=age_s_since_last_pvt, value=0.35)])])
/gps/fix | 1773075240323441897 | sensor_msgs/msg/NavSatFix | NavSatFix(header=Header(stamp=Time(sec=1773075240, nanosec=322476169), frame_id=gps_link), status=NavSatStatus(status=0, service=1), latitude=51.4767568, longitude=-0.0367459, altitude=5.993, position_covariance=[1.1642409999999999, 0.0, 0.0, 0.0, 1.1642409999999999, 0.0, 0.0, 0.0, 1.522756], position_covariance_type=2)
/gps/vel | 1773075240324011512 | geometry_msgs/msg/TwistStamped | TwistStamped(header=Header(stamp=Time(sec=1773075240, nanosec=322476169), frame_id=gps_link), twist=Twist(linear=Vector3(x=0.643, y=-0.422, z=0.122), angular=Vector3(x=0.0, y=0.0, z=0.0)))
/gps/fix | 1773075241321767363 | sensor_msgs/msg/NavSatFix | NavSatFix(header=Header(stamp=Time(sec=1773075241, nanosec=320802418), frame_id=gps_link), status=NavSatStatus(status=0, service=1), latitude=51.4767508, longitude=-0.0367332, altitude=6.345, position_covariance=[1.2499240000000003, 0.0, 0.0, 0.0, 1.2499240000000003, 0.0, 0.0, 0.0, 1.708249], position_covariance_type=2)
/gps/vel | 1773075241322453670 | geometry_msgs/msg/TwistStamped | TwistStamped(header=Header(stamp=Time(sec=1773075241, nanosec=320802418), frame_id=gps_link), twist=Twist(linear=Vector3(x=0.996, y=-0.589, z=0.16), angular=Vector3(x=0.0, y=0.0, z=0.0)))
/gps/diagnostics | 1773075241323336411 | diagnostic_msgs/msg/DiagnosticArray | DiagnosticArray(header=Header(stamp=Time(sec=1773075241, nanosec=322607965), frame_id=), status=[DiagnosticStatus(level=0, name=gnss_maxm10s_i2c, message=OK, hardware_id=, values=[KeyValue(key=i2c_addr, value=0x42), KeyValue(key=avail_bytes_last_poll, value=100), KeyValue(key=age_s_since_last_pvt, value=0.00)])])
/gps/fix | 1773075242313064469 | sensor_msgs/msg/NavSatFix | NavSatFix(header=Header(stamp=Time(sec=1773075242, nanosec=312116921), frame_id=gps_link), status=NavSatStatus(status=0, service=1), latitude=51.4767473, longitude=-0.036718299999999995, altitude=6.631, position_covariance=[1.315609, 0.0, 0.0, 0.0, 1.315609, 0.0, 0.0, 0.0, 1.8550440000000004], position_covariance_type=2)
/gps/vel | 1773075242313603869 | geometry_msgs/msg/TwistStamped | TwistStamped(header=Header(stamp=Time(sec=1773075242, nanosec=312116921), frame_id=gps_link), twist=Twist(linear=Vector3(x=1.043, y=-0.328, z=0.086), angular=Vector3(x=0.0, y=0.0, z=0.0)))
/gps/diagnostics | 1773075242683107532 | diagnostic_msgs/msg/DiagnosticArray | DiagnosticArray(header=Header(stamp=Time(sec=1773075242, nanosec=682328300), frame_id=), status=[DiagnosticStatus(level=0, name=gnss_maxm10s_i2c, message=OK, hardware_id=, values=[KeyValue(key=i2c_addr, value=0x42), KeyValue(key=avail_bytes_last_poll, value=0), KeyValue(key=age_s_since_last_pvt, value=0.37)])])
/gps/fix | 1773075243304210871 | sensor_msgs/msg/NavSatFix | NavSatFix(header=Header(stamp=Time(sec=1773075243, nanosec=303203870), frame_id=gps_link), status=NavSatStatus(status=0, service=1), latitude=51.476745799999996, longitude=-0.0367044, altitude=7.4, position_covariance=[1.3712410000000002, 0.0, 0.0, 0.0, 1.3712410000000002, 0.0, 0.0, 0.0, 2.090916], position_covariance_type=2)
/gps/vel | 1773075243305059375 | geometry_msgs/msg/TwistStamped | TwistStamped(header=Header(stamp=Time(sec=1773075243, nanosec=303203870), frame_id=gps_link), twist=Twist(linear=Vector3(x=0.915, y=-0.171, z=0.421), angular=Vector3(x=0.0, y=0.0, z=0.0)))
/gps/diagnostics | 1773075244316652050 | diagnostic_msgs/msg/DiagnosticArray | DiagnosticArray(header=Header(stamp=Time(sec=1773075244, nanosec=315900998), frame_id=), status=[DiagnosticStatus(level=0, name=gnss_maxm10s_i2c, message=OK, hardware_id=, values=[KeyValue(key=i2c_addr, value=0x42), KeyValue(key=avail_bytes_last_poll, value=100), KeyValue(key=age_s_since_last_pvt, value=1.01)])])
/gps/fix | 1773075245314713318 | sensor_msgs/msg/NavSatFix | NavSatFix(header=Header(stamp=Time(sec=1773075245, nanosec=313777007), frame_id=gps_link), status=NavSatStatus(status=0, service=1), latitude=51.4767474, longitude=-0.0366705, altitude=7.225, position_covariance=[1.113025, 0.0, 0.0, 0.0, 1.113025, 0.0, 0.0, 0.0, 1.7689000000000001], position_covariance_type=2)
/gps/vel | 1773075245315330857 | geometry_msgs/msg/TwistStamped | TwistStamped(header=Header(stamp=Time(sec=1773075245, nanosec=313777007), frame_id=gps_link), twist=Twist(linear=Vector3(x=1.129, y=-0.065, z=0.253), angular=Vector3(x=0.0, y=0.0, z=0.0)))
/gps/diagnostics | 1773075245683563670 | diagnostic_msgs/msg/DiagnosticArray | DiagnosticArray(header=Header(stamp=Time(sec=1773075245, nanosec=682728047), frame_id=), status=[DiagnosticStatus(level=0, name=gnss_maxm10s_i2c, message=OK, hardware_id=, values=[KeyValue(key=i2c_addr, value=0x42), KeyValue(key=avail_bytes_last_poll, value=0), KeyValue(key=age_s_since_last_pvt, value=0.37)])])
/gps/fix | 1773075246315880155 | sensor_msgs/msg/NavSatFix | NavSatFix(header=Header(stamp=Time(sec=1773075246, nanosec=314933976), frame_id=gps_link), status=NavSatStatus(status=0, service=1), latitude=51.4767472, longitude=-0.036654599999999996, altitude=7.495, position_covariance=[0.998001, 0.0, 0.0, 0.0, 0.998001, 0.0, 0.0, 0.0, 1.633284], position_covariance_type=2)
/gps/vel | 1773075246316403228 | geometry_msgs/msg/TwistStamped | TwistStamped(header=Header(stamp=Time(sec=1773075246, nanosec=314933976), frame_id=gps_link), twist=Twist(linear=Vector3(x=1.144, y=0.03, z=0.179), angular=Vector3(x=0.0, y=0.0, z=0.0)))
/gps/fix | 1773075247323804698 | sensor_msgs/msg/NavSatFix | NavSatFix(header=Header(stamp=Time(sec=1773075247, nanosec=322902291), frame_id=gps_link), status=NavSatStatus(status=0, service=1), latitude=51.476749, longitude=-0.036635799999999996, altitude=7.669, position_covariance=[0.9025, 0.0, 0.0, 0.0, 0.9025, 0.0, 0.0, 0.0, 1.5951689999999998], position_covariance_type=2)
/gps/vel | 1773075247324348753 | geometry_msgs/msg/TwistStamped | TwistStamped(header=Header(stamp=Time(sec=1773075247, nanosec=322902291), frame_id=gps_link), twist=Twist(linear=Vector3(x=1.261, y=0.242, z=0.131), angular=Vector3(x=0.0, y=0.0, z=0.0)))
/gps/diagnostics | 1773075247325178460 | diagnostic_msgs/msg/DiagnosticArray | DiagnosticArray(header=Header(stamp=Time(sec=1773075247, nanosec=324497339), frame_id=), status=[DiagnosticStatus(level=0, name=gnss_maxm10s_i2c, message=OK, hardware_id=, values=[KeyValue(key=i2c_addr, value=0x42), KeyValue(key=avail_bytes_last_poll, value=100), KeyValue(key=age_s_since_last_pvt, value=0.00)])])
/gps/fix | 1773075248319161295 | sensor_msgs/msg/NavSatFix | NavSatFix(header=Header(stamp=Time(sec=1773075248, nanosec=318198084), frame_id=gps_link), status=NavSatStatus(status=0, service=1), latitude=51.476751, longitude=-0.036618, altitude=7.857, position_covariance=[0.842724, 0.0, 0.0, 0.0, 0.842724, 0.0, 0.0, 0.0, 1.597696], position_covariance_type=2)
/gps/vel | 1773075248319964493 | geometry_msgs/msg/TwistStamped | TwistStamped(header=Header(stamp=Time(sec=1773075248, nanosec=318198084), frame_id=gps_link), twist=Twist(linear=Vector3(x=1.204, y=0.32, z=0.226), angular=Vector3(x=0.0, y=0.0, z=0.0)))
/gps/diagnostics | 1773075248682446100 | diagnostic_msgs/msg/DiagnosticArray | DiagnosticArray(header=Header(stamp=Time(sec=1773075248, nanosec=681628825), frame_id=), status=[DiagnosticStatus(level=0, name=gnss_maxm10s_i2c, message=OK, hardware_id=, values=[KeyValue(key=i2c_addr, value=0x42), KeyValue(key=avail_bytes_last_poll, value=0), KeyValue(key=age_s_since_last_pvt, value=0.36)])])
/gps/fix | 1773075249324133924 | sensor_msgs/msg/NavSatFix | NavSatFix(header=Header(stamp=Time(sec=1773075249, nanosec=323169661), frame_id=gps_link), status=NavSatStatus(status=0, service=1), latitude=51.4767558, longitude=-0.0365988, altitude=7.83, position_covariance=[0.781456, 0.0, 0.0, 0.0, 0.781456, 0.0, 0.0, 0.0, 1.582564], position_covariance_type=2)
/gps/vel | 1773075249324700683 | geometry_msgs/msg/TwistStamped | TwistStamped(header=Header(stamp=Time(sec=1773075249, nanosec=323169661), frame_id=gps_link), twist=Twist(linear=Vector3(x=1.267, y=0.486, z=0.152), angular=Vector3(x=0.0, y=0.0, z=0.0)))
/gps/diagnostics | 1773075249683300189 | diagnostic_msgs/msg/DiagnosticArray | DiagnosticArray(header=Header(stamp=Time(sec=1773075249, nanosec=682550838), frame_id=), status=[DiagnosticStatus(level=0, name=gnss_maxm10s_i2c, message=OK, hardware_id=, values=[KeyValue(key=i2c_addr, value=0x42), KeyValue(key=avail_bytes_last_poll, value=0), KeyValue(key=age_s_since_last_pvt, value=0.36)])])
/gps/fix | 1773075250323754077 | sensor_msgs/msg/NavSatFix | NavSatFix(header=Header(stamp=Time(sec=1773075250, nanosec=322779594), frame_id=gps_link), status=NavSatStatus(status=0, service=1), latitude=51.4767607, longitude=-0.0365801, altitude=7.622, position_covariance=[0.7224999999999999, 0.0, 0.0, 0.0, 0.7224999999999999, 0.0, 0.0, 0.0, 1.5450490000000003], position_covariance_type=2)
/gps/vel | 1773075250324562603 | geometry_msgs/msg/TwistStamped | TwistStamped(header=Header(stamp=Time(sec=1773075250, nanosec=322779594), frame_id=gps_link), twist=Twist(linear=Vector3(x=1.249, y=0.554, z=-0.1), angular=Vector3(x=0.0, y=0.0, z=0.0)))
/gps/diagnostics | 1773075250683501631 | diagnostic_msgs/msg/DiagnosticArray | DiagnosticArray(header=Header(stamp=Time(sec=1773075250, nanosec=682888291), frame_id=), status=[DiagnosticStatus(level=0, name=gnss_maxm10s_i2c, message=OK, hardware_id=, values=[KeyValue(key=i2c_addr, value=0x42), KeyValue(key=avail_bytes_last_poll, value=0), KeyValue(key=age_s_since_last_pvt, value=0.36)])])
/gps/fix | 1773075251335757870 | sensor_msgs/msg/NavSatFix | NavSatFix(header=Header(stamp=Time(sec=1773075251, nanosec=334784835), frame_id=gps_link), status=NavSatStatus(status=0, service=1), latitude=51.4767635, longitude=-0.0365644, altitude=7.265, position_covariance=[0.677329, 0.0, 0.0, 0.0, 0.677329, 0.0, 0.0, 0.0, 1.507984], position_covariance_type=2)
/gps/vel | 1773075251336324884 | geometry_msgs/msg/TwistStamped | TwistStamped(header=Header(stamp=Time(sec=1773075251, nanosec=334784835), frame_id=gps_link), twist=Twist(linear=Vector3(x=0.997, y=0.223, z=-0.167), angular=Vector3(x=0.0, y=0.0, z=0.0)))
/gps/diagnostics | 1773075251684192442 | diagnostic_msgs/msg/DiagnosticArray | DiagnosticArray(header=Header(stamp=Time(sec=1773075251, nanosec=683421500), frame_id=), status=[DiagnosticStatus(level=0, name=gnss_maxm10s_i2c, message=OK, hardware_id=, values=[KeyValue(key=i2c_addr, value=0x42), KeyValue(key=avail_bytes_last_poll, value=0), KeyValue(key=age_s_since_last_pvt, value=0.35)])])
/gps/fix | 1773075252326102729 | sensor_msgs/msg/NavSatFix | NavSatFix(header=Header(stamp=Time(sec=1773075252, nanosec=325140700), frame_id=gps_link), status=NavSatStatus(status=0, service=1), latitude=51.476766299999994, longitude=-0.0365486, altitude=7.02, position_covariance=[0.6448090000000001, 0.0, 0.0, 0.0, 0.6448090000000001, 0.0, 0.0, 0.0, 1.4762250000000001], position_covariance_type=2)
/gps/vel | 1773075252326602487 | geometry_msgs/msg/TwistStamped | TwistStamped(header=Header(stamp=Time(sec=1773075252, nanosec=325140700), frame_id=gps_link), twist=Twist(linear=Vector3(x=1.078, y=0.344, z=-0.146), angular=Vector3(x=0.0, y=0.0, z=0.0)))
/gps/fix | 1773075253326683337 | sensor_msgs/msg/NavSatFix | NavSatFix(header=Header(stamp=Time(sec=1773075253, nanosec=325669340), frame_id=gps_link), status=NavSatStatus(status=0, service=1), latitude=51.4767685, longitude=-0.0365319, altitude=6.828, position_covariance=[0.5959840000000001, 0.0, 0.0, 0.0, 0.5959840000000001, 0.0, 0.0, 0.0, 1.3642239999999999], position_covariance_type=2)
/gps/vel | 1773075253327799501 | geometry_msgs/msg/TwistStamped | TwistStamped(header=Header(stamp=Time(sec=1773075253, nanosec=325669340), frame_id=gps_link), twist=Twist(linear=Vector3(x=1.183, y=0.276, z=-0.104), angular=Vector3(x=0.0, y=0.0, z=0.0)))
/gps/diagnostics | 1773075253328468788 | diagnostic_msgs/msg/DiagnosticArray | DiagnosticArray(header=Header(stamp=Time(sec=1773075253, nanosec=327549382), frame_id=), status=[DiagnosticStatus(level=0, name=gnss_maxm10s_i2c, message=OK, hardware_id=, values=[KeyValue(key=i2c_addr, value=0x42), KeyValue(key=avail_bytes_last_poll, value=100), KeyValue(key=age_s_since_last_pvt, value=0.00)])])
/gps/fix | 1773075254325736509 | sensor_msgs/msg/NavSatFix | NavSatFix(header=Header(stamp=Time(sec=1773075254, nanosec=324808401), frame_id=gps_link), status=NavSatStatus(status=0, service=1), latitude=51.4767714, longitude=-0.036514399999999995, altitude=6.87, position_covariance=[0.546121, 0.0, 0.0, 0.0, 0.546121, 0.0, 0.0, 0.0, 1.2678759999999998], position_covariance_type=2)
/gps/vel | 1773075254326246543 | geometry_msgs/msg/TwistStamped | TwistStamped(header=Header(stamp=Time(sec=1773075254, nanosec=324808401), frame_id=gps_link), twist=Twist(linear=Vector3(x=1.16, y=0.468, z=-0.093), angular=Vector3(x=0.0, y=0.0, z=0.0)))
/gps/diagnostics | 1773075254682385910 | diagnostic_msgs/msg/DiagnosticArray | DiagnosticArray(header=Header(stamp=Time(sec=1773075254, nanosec=681656855), frame_id=), status=[DiagnosticStatus(level=0, name=gnss_maxm10s_i2c, message=OK, hardware_id=, values=[KeyValue(key=i2c_addr, value=0x42), KeyValue(key=avail_bytes_last_poll, value=0), KeyValue(key=age_s_since_last_pvt, value=0.36)])])
/gps/fix | 1773075255326776375 | sensor_msgs/msg/NavSatFix | NavSatFix(header=Header(stamp=Time(sec=1773075255, nanosec=325813931), frame_id=gps_link), status=NavSatStatus(status=0, service=1), latitude=51.476776, longitude=-0.0364965, altitude=6.801, position_covariance=[0.49843599999999993, 0.0, 0.0, 0.0, 0.49843599999999993, 0.0, 0.0, 0.0, 1.1620840000000001], position_covariance_type=2)
/gps/vel | 1773075255327347158 | geometry_msgs/msg/TwistStamped | TwistStamped(header=Header(stamp=Time(sec=1773075255, nanosec=325813931), frame_id=gps_link), twist=Twist(linear=Vector3(x=1.169, y=0.465, z=0.002), angular=Vector3(x=0.0, y=0.0, z=0.0)))
/gps/fix | 1773075256325195873 | sensor_msgs/msg/NavSatFix | NavSatFix(header=Header(stamp=Time(sec=1773075256, nanosec=324215670), frame_id=gps_link), status=NavSatStatus(status=0, service=1), latitude=51.476782199999995, longitude=-0.0364791, altitude=6.898, position_covariance=[0.45968400000000004, 0.0, 0.0, 0.0, 0.45968400000000004, 0.0, 0.0, 0.0, 1.058841], position_covariance_type=2)
/gps/vel | 1773075256325787417 | geometry_msgs/msg/TwistStamped | TwistStamped(header=Header(stamp=Time(sec=1773075256, nanosec=324215670), frame_id=gps_link), twist=Twist(linear=Vector3(x=1.234, y=0.58, z=0.06), angular=Vector3(x=0.0, y=0.0, z=0.0)))
/gps/diagnostics | 1773075256326679326 | diagnostic_msgs/msg/DiagnosticArray | DiagnosticArray(header=Header(stamp=Time(sec=1773075256, nanosec=325955630), frame_id=), status=[DiagnosticStatus(level=0, name=gnss_maxm10s_i2c, message=OK, hardware_id=, values=[KeyValue(key=i2c_addr, value=0x42), KeyValue(key=avail_bytes_last_poll, value=100), KeyValue(key=age_s_since_last_pvt, value=0.00)])])
/gps/fix | 1773075257331258407 | sensor_msgs/msg/NavSatFix | NavSatFix(header=Header(stamp=Time(sec=1773075257, nanosec=330353443), frame_id=gps_link), status=NavSatStatus(status=0, service=1), latitude=51.4767868, longitude=-0.0364621, altitude=6.924, position_covariance=[0.43033600000000005, 0.0, 0.0, 0.0, 0.43033600000000005, 0.0, 0.0, 0.0, 0.972196], position_covariance_type=2)
/gps/vel | 1773075257332169780 | geometry_msgs/msg/TwistStamped | TwistStamped(header=Header(stamp=Time(sec=1773075257, nanosec=330353443), frame_id=gps_link), twist=Twist(linear=Vector3(x=1.092, y=0.439, z=0.018), angular=Vector3(x=0.0, y=0.0, z=0.0)))
/gps/diagnostics | 1773075257332757710 | diagnostic_msgs/msg/DiagnosticArray | DiagnosticArray(header=Header(stamp=Time(sec=1773075257, nanosec=332030460), frame_id=), status=[DiagnosticStatus(level=0, name=gnss_maxm10s_i2c, message=OK, hardware_id=, values=[KeyValue(key=i2c_addr, value=0x42), KeyValue(key=avail_bytes_last_poll, value=100), KeyValue(key=age_s_since_last_pvt, value=0.00)])])
/gps/fix | 1773075258332017831 | sensor_msgs/msg/NavSatFix | NavSatFix(header=Header(stamp=Time(sec=1773075258, nanosec=331112426), frame_id=gps_link), status=NavSatStatus(status=0, service=1), latitude=51.476791299999995, longitude=-0.0364484, altitude=7.198, position_covariance=[0.417316, 0.0, 0.0, 0.0, 0.417316, 0.0, 0.0, 0.0, 0.9216], position_covariance_type=2)
/gps/vel | 1773075258332487166 | geometry_msgs/msg/TwistStamped | TwistStamped(header=Header(stamp=Time(sec=1773075258, nanosec=331112426), frame_id=gps_link), twist=Twist(linear=Vector3(x=0.953, y=0.453, z=0.298), angular=Vector3(x=0.0, y=0.0, z=0.0)))
/gps/diagnostics | 1773075258333359010 | diagnostic_msgs/msg/DiagnosticArray | DiagnosticArray(header=Header(stamp=Time(sec=1773075258, nanosec=332686865), frame_id=), status=[DiagnosticStatus(level=0, name=gnss_maxm10s_i2c, message=OK, hardware_id=, values=[KeyValue(key=i2c_addr, value=0x42), KeyValue(key=avail_bytes_last_poll, value=100), KeyValue(key=age_s_since_last_pvt, value=0.00)])])
/gps/diagnostics | 1773075259685416348 | diagnostic_msgs/msg/DiagnosticArray | DiagnosticArray(header=Header(stamp=Time(sec=1773075259, nanosec=684732573), frame_id=), status=[DiagnosticStatus(level=0, name=gnss_maxm10s_i2c, message=OK, hardware_id=, values=[KeyValue(key=i2c_addr, value=0x42), KeyValue(key=avail_bytes_last_poll, value=0), KeyValue(key=age_s_since_last_pvt, value=1.35)])])
/gps/fix | 1773075260327335890 | sensor_msgs/msg/NavSatFix | NavSatFix(header=Header(stamp=Time(sec=1773075260, nanosec=326386114), frame_id=gps_link), status=NavSatStatus(status=0, service=1), latitude=51.4767978, longitude=-0.036413, altitude=7.497, position_covariance=[0.43033600000000005, 0.0, 0.0, 0.0, 0.43033600000000005, 0.0, 0.0, 0.0, 0.8911359999999999], position_covariance_type=2)
/gps/vel | 1773075260327859248 | geometry_msgs/msg/TwistStamped | TwistStamped(header=Header(stamp=Time(sec=1773075260, nanosec=326386114), frame_id=gps_link), twist=Twist(linear=Vector3(x=1.532, y=0.456, z=-0.182), angular=Vector3(x=0.0, y=0.0, z=0.0)))
/gps/diagnostics | 1773075261322083558 | diagnostic_msgs/msg/DiagnosticArray | DiagnosticArray(header=Header(stamp=Time(sec=1773075261, nanosec=321378897), frame_id=), status=[DiagnosticStatus(level=0, name=gnss_maxm10s_i2c, message=OK, hardware_id=, values=[KeyValue(key=i2c_addr, value=0x42), KeyValue(key=avail_bytes_last_poll, value=100), KeyValue(key=age_s_since_last_pvt, value=0.99)])])
/gps/fix | 1773075262326757589 | sensor_msgs/msg/NavSatFix | NavSatFix(header=Header(stamp=Time(sec=1773075262, nanosec=325794928), frame_id=gps_link), status=NavSatStatus(status=0, service=1), latitude=51.4768075, longitude=-0.0363758, altitude=7.256, position_covariance=[0.4664890000000001, 0.0, 0.0, 0.0, 0.4664890000000001, 0.0, 0.0, 0.0, 0.952576], position_covariance_type=2)
/gps/vel | 1773075262327363512 | geometry_msgs/msg/TwistStamped | TwistStamped(header=Header(stamp=Time(sec=1773075262, nanosec=325794928), frame_id=gps_link), twist=Twist(linear=Vector3(x=1.215, y=0.482, z=0.014), angular=Vector3(x=0.0, y=0.0, z=0.0)))
/gps/diagnostics | 1773075262328328932 | diagnostic_msgs/msg/DiagnosticArray | DiagnosticArray(header=Header(stamp=Time(sec=1773075262, nanosec=327581988), frame_id=), status=[DiagnosticStatus(level=0, name=gnss_maxm10s_i2c, message=OK, hardware_id=, values=[KeyValue(key=i2c_addr, value=0x42), KeyValue(key=avail_bytes_last_poll, value=100), KeyValue(key=age_s_since_last_pvt, value=0.00)])])
/gps/diagnostics | 1773075263682460498 | diagnostic_msgs/msg/DiagnosticArray | DiagnosticArray(header=Header(stamp=Time(sec=1773075263, nanosec=681656790), frame_id=), status=[DiagnosticStatus(level=0, name=gnss_maxm10s_i2c, message=OK, hardware_id=, values=[KeyValue(key=i2c_addr, value=0x42), KeyValue(key=avail_bytes_last_poll, value=0), KeyValue(key=age_s_since_last_pvt, value=1.36)])])
/gps/fix | 1773075264316649117 | sensor_msgs/msg/NavSatFix | NavSatFix(header=Header(stamp=Time(sec=1773075264, nanosec=315691593), frame_id=gps_link), status=NavSatStatus(status=0, service=1), latitude=51.476816799999995, longitude=-0.0363381, altitude=7.292, position_covariance=[0.4637610000000001, 0.0, 0.0, 0.0, 0.4637610000000001, 0.0, 0.0, 0.0, 0.954529], position_covariance_type=2)
/gps/vel | 1773075264317178766 | geometry_msgs/msg/TwistStamped | TwistStamped(header=Header(stamp=Time(sec=1773075264, nanosec=315691593), frame_id=gps_link), twist=Twist(linear=Vector3(x=1.328, y=0.403, z=-0.056), angular=Vector3(x=0.0, y=0.0, z=0.0)))
/gps/diagnostics | 1773075264682505770 | diagnostic_msgs/msg/DiagnosticArray | DiagnosticArray(header=Header(stamp=Time(sec=1773075264, nanosec=681700397), frame_id=), status=[DiagnosticStatus(level=0, name=gnss_maxm10s_i2c, message=OK, hardware_id=, values=[KeyValue(key=i2c_addr, value=0x42), KeyValue(key=avail_bytes_last_poll, value=0), KeyValue(key=age_s_since_last_pvt, value=0.37)])])
/gps/diagnostics | 1773075265682476384 | diagnostic_msgs/msg/DiagnosticArray | DiagnosticArray(header=Header(stamp=Time(sec=1773075265, nanosec=681745857), frame_id=), status=[DiagnosticStatus(level=0, name=gnss_maxm10s_i2c, message=OK, hardware_id=, values=[KeyValue(key=i2c_addr, value=0x42), KeyValue(key=avail_bytes_last_poll, value=0), KeyValue(key=age_s_since_last_pvt, value=1.37)])])
/gps/fix | 1773075266316400160 | sensor_msgs/msg/NavSatFix | NavSatFix(header=Header(stamp=Time(sec=1773075266, nanosec=315537581), frame_id=gps_link), status=NavSatStatus(status=0, service=1), latitude=51.476824, longitude=-0.0363039, altitude=7.339, position_covariance=[0.4096, 0.0, 0.0, 0.0, 0.4096, 0.0, 0.0, 0.0, 0.8611840000000001], position_covariance_type=2)
/gps/vel | 1773075266317164763 | geometry_msgs/msg/TwistStamped | TwistStamped(header=Header(stamp=Time(sec=1773075266, nanosec=315537581), frame_id=gps_link), twist=Twist(linear=Vector3(x=1.145, y=0.291, z=0.059), angular=Vector3(x=0.0, y=0.0, z=0.0)))
/gps/diagnostics | 1773075266682558655 | diagnostic_msgs/msg/DiagnosticArray | DiagnosticArray(header=Header(stamp=Time(sec=1773075266, nanosec=681823019), frame_id=), status=[DiagnosticStatus(level=0, name=gnss_maxm10s_i2c, message=OK, hardware_id=, values=[KeyValue(key=i2c_addr, value=0x42), KeyValue(key=avail_bytes_last_poll, value=0), KeyValue(key=age_s_since_last_pvt, value=0.37)])])
/gps/fix | 1773075267314602343 | sensor_msgs/msg/NavSatFix | NavSatFix(header=Header(stamp=Time(sec=1773075267, nanosec=313656589), frame_id=gps_link), status=NavSatStatus(status=0, service=1), latitude=51.476827199999995, longitude=-0.0362873, altitude=7.329, position_covariance=[0.381924, 0.0, 0.0, 0.0, 0.381924, 0.0, 0.0, 0.0, 0.815409], position_covariance_type=2)
/gps/vel | 1773075267315197347 | geometry_msgs/msg/TwistStamped | TwistStamped(header=Header(stamp=Time(sec=1773075267, nanosec=313656589), frame_id=gps_link), twist=Twist(linear=Vector3(x=1.193, y=0.252, z=0.098), angular=Vector3(x=0.0, y=0.0, z=0.0)))
/gps/fix | 1773075268317216359 | sensor_msgs/msg/NavSatFix | NavSatFix(header=Header(stamp=Time(sec=1773075268, nanosec=316368232), frame_id=gps_link), status=NavSatStatus(status=0, service=1), latitude=51.4768305, longitude=-0.036268, altitude=7.229, position_covariance=[0.36, 0.0, 0.0, 0.0, 0.36, 0.0, 0.0, 0.0, 0.770884], position_covariance_type=2)
/gps/vel | 1773075268317752687 | geometry_msgs/msg/TwistStamped | TwistStamped(header=Header(stamp=Time(sec=1773075268, nanosec=316368232), frame_id=gps_link), twist=Twist(linear=Vector3(x=1.341, y=0.329, z=-0.074), angular=Vector3(x=0.0, y=0.0, z=0.0)))
/gps/diagnostics | 1773075268318562125 | diagnostic_msgs/msg/DiagnosticArray | DiagnosticArray(header=Header(stamp=Time(sec=1773075268, nanosec=317908874), frame_id=), status=[DiagnosticStatus(level=0, name=gnss_maxm10s_i2c, message=OK, hardware_id=, values=[KeyValue(key=i2c_addr, value=0x42), KeyValue(key=avail_bytes_last_poll, value=100), KeyValue(key=age_s_since_last_pvt, value=0.00)])])
/gps/fix | 1773075269313195088 | sensor_msgs/msg/NavSatFix | NavSatFix(header=Header(stamp=Time(sec=1773075269, nanosec=312236746), frame_id=gps_link), status=NavSatStatus(status=0, service=1), latitude=51.476833899999995, longitude=-0.036249199999999995, altitude=7.101, position_covariance=[0.36, 0.0, 0.0, 0.0, 0.36, 0.0, 0.0, 0.0, 0.763876], position_covariance_type=2)
/gps/vel | 1773075269313701781 | geometry_msgs/msg/TwistStamped | TwistStamped(header=Header(stamp=Time(sec=1773075269, nanosec=312236746), frame_id=gps_link), twist=Twist(linear=Vector3(x=1.291, y=0.422, z=-0.035), angular=Vector3(x=0.0, y=0.0, z=0.0)))
/gps/diagnostics | 1773075269682176402 | diagnostic_msgs/msg/DiagnosticArray | DiagnosticArray(header=Header(stamp=Time(sec=1773075269, nanosec=681418826), frame_id=), status=[DiagnosticStatus(level=0, name=gnss_maxm10s_i2c, message=OK, hardware_id=, values=[KeyValue(key=i2c_addr, value=0x42), KeyValue(key=avail_bytes_last_poll, value=0), KeyValue(key=age_s_since_last_pvt, value=0.37)])])
/gps/fix | 1773075270312984792 | sensor_msgs/msg/NavSatFix | NavSatFix(header=Header(stamp=Time(sec=1773075270, nanosec=311998134), frame_id=gps_link), status=NavSatStatus(status=0, service=1), latitude=51.4768372, longitude=-0.0362306, altitude=7.101, position_covariance=[0.36, 0.0, 0.0, 0.0, 0.36, 0.0, 0.0, 0.0, 0.748225], position_covariance_type=2)
/gps/vel | 1773075270313544156 | geometry_msgs/msg/TwistStamped | TwistStamped(header=Header(stamp=Time(sec=1773075270, nanosec=311998134), frame_id=gps_link), twist=Twist(linear=Vector3(x=1.287, y=0.338, z=0.051), angular=Vector3(x=0.0, y=0.0, z=0.0)))
/gps/diagnostics | 1773075270682338290 | diagnostic_msgs/msg/DiagnosticArray | DiagnosticArray(header=Header(stamp=Time(sec=1773075270, nanosec=681604626), frame_id=), status=[DiagnosticStatus(level=0, name=gnss_maxm10s_i2c, message=OK, hardware_id=, values=[KeyValue(key=i2c_addr, value=0x42), KeyValue(key=avail_bytes_last_poll, value=0), KeyValue(key=age_s_since_last_pvt, value=0.37)])])
/gps/fix | 1773075271322487345 | sensor_msgs/msg/NavSatFix | NavSatFix(header=Header(stamp=Time(sec=1773075271, nanosec=321528045), frame_id=gps_link), status=NavSatStatus(status=0, service=1), latitude=51.476840499999994, longitude=-0.0362122, altitude=7.121, position_covariance=[0.346921, 0.0, 0.0, 0.0, 0.346921, 0.0, 0.0, 0.0, 0.7140249999999999], position_covariance_type=2)
/gps/vel | 1773075271323030373 | geometry_msgs/msg/TwistStamped | TwistStamped(header=Header(stamp=Time(sec=1773075271, nanosec=321528045), frame_id=gps_link), twist=Twist(linear=Vector3(x=1.28, y=0.386, z=0.041), angular=Vector3(x=0.0, y=0.0, z=0.0)))
/gps/diagnostics | 1773075272329664178 | diagnostic_msgs/msg/DiagnosticArray | DiagnosticArray(header=Header(stamp=Time(sec=1773075272, nanosec=328927926), frame_id=), status=[DiagnosticStatus(level=0, name=gnss_maxm10s_i2c, message=OK, hardware_id=, values=[KeyValue(key=i2c_addr, value=0x42), KeyValue(key=avail_bytes_last_poll, value=100), KeyValue(key=age_s_since_last_pvt, value=1.01)])])
/gps/fix | 1773075273330073437 | sensor_msgs/msg/NavSatFix | NavSatFix(header=Header(stamp=Time(sec=1773075273, nanosec=329130478), frame_id=gps_link), status=NavSatStatus(status=0, service=1), latitude=51.476847799999994, longitude=-0.0361776, altitude=7.057, position_covariance=[0.31360000000000005, 0.0, 0.0, 0.0, 0.31360000000000005, 0.0, 0.0, 0.0, 0.6416010000000001], position_covariance_type=2)
/gps/vel | 1773075273330685247 | geometry_msgs/msg/TwistStamped | TwistStamped(header=Header(stamp=Time(sec=1773075273, nanosec=329130478), frame_id=gps_link), twist=Twist(linear=Vector3(x=1.128, y=0.299, z=-0.048), angular=Vector3(x=0.0, y=0.0, z=0.0)))
/gps/diagnostics | 1773075273331645042 | diagnostic_msgs/msg/DiagnosticArray | DiagnosticArray(header=Header(stamp=Time(sec=1773075273, nanosec=330922460), frame_id=), status=[DiagnosticStatus(level=0, name=gnss_maxm10s_i2c, message=OK, hardware_id=, values=[KeyValue(key=i2c_addr, value=0x42), KeyValue(key=avail_bytes_last_poll, value=100), KeyValue(key=age_s_since_last_pvt, value=0.00)])])
/gps/fix | 1773075274330732891 | sensor_msgs/msg/NavSatFix | NavSatFix(header=Header(stamp=Time(sec=1773075274, nanosec=329842292), frame_id=gps_link), status=NavSatStatus(status=0, service=1), latitude=51.476850299999995, longitude=-0.0361615, altitude=7.086, position_covariance=[0.30580900000000005, 0.0, 0.0, 0.0, 0.30580900000000005, 0.0, 0.0, 0.0, 0.620944], position_covariance_type=2)
/gps/vel | 1773075274331208758 | geometry_msgs/msg/TwistStamped | TwistStamped(header=Header(stamp=Time(sec=1773075274, nanosec=329842292), frame_id=gps_link), twist=Twist(linear=Vector3(x=1.099, y=0.282, z=0.022), angular=Vector3(x=0.0, y=0.0, z=0.0)))
/gps/diagnostics | 1773075274332057112 | diagnostic_msgs/msg/DiagnosticArray | DiagnosticArray(header=Header(stamp=Time(sec=1773075274, nanosec=331434191), frame_id=), status=[DiagnosticStatus(level=0, name=gnss_maxm10s_i2c, message=OK, hardware_id=, values=[KeyValue(key=i2c_addr, value=0x42), KeyValue(key=avail_bytes_last_poll, value=100), KeyValue(key=age_s_since_last_pvt, value=0.00)])])
/gps/fix | 1773075275339400841 | sensor_msgs/msg/NavSatFix | NavSatFix(header=Header(stamp=Time(sec=1773075275, nanosec=338466166), frame_id=gps_link), status=NavSatStatus(status=0, service=1), latitude=51.4768526, longitude=-0.036145699999999996, altitude=7.111, position_covariance=[0.29702500000000004, 0.0, 0.0, 0.0, 0.29702500000000004, 0.0, 0.0, 0.0, 0.597529], position_covariance_type=2)
/gps/vel | 1773075275339976866 | geometry_msgs/msg/TwistStamped | TwistStamped(header=Header(stamp=Time(sec=1773075275, nanosec=338466166), frame_id=gps_link), twist=Twist(linear=Vector3(x=1.108, y=0.341, z=0.048), angular=Vector3(x=0.0, y=0.0, z=0.0)))
/gps/diagnostics | 1773075275341049778 | diagnostic_msgs/msg/DiagnosticArray | DiagnosticArray(header=Header(stamp=Time(sec=1773075275, nanosec=340140846), frame_id=), status=[DiagnosticStatus(level=0, name=gnss_maxm10s_i2c, message=OK, hardware_id=, values=[KeyValue(key=i2c_addr, value=0x42), KeyValue(key=avail_bytes_last_poll, value=100), KeyValue(key=age_s_since_last_pvt, value=0.00)])])
/gps/fix | 1773075276330405978 | sensor_msgs/msg/NavSatFix | NavSatFix(header=Header(stamp=Time(sec=1773075276, nanosec=329461453), frame_id=gps_link), status=NavSatStatus(status=0, service=1), latitude=51.476855099999995, longitude=-0.0361272, altitude=7.014, position_covariance=[0.28729600000000005, 0.0, 0.0, 0.0, 0.28729600000000005, 0.0, 0.0, 0.0, 0.573049], position_covariance_type=2)
/gps/vel | 1773075276330924347 | geometry_msgs/msg/TwistStamped | TwistStamped(header=Header(stamp=Time(sec=1773075276, nanosec=329461453), frame_id=gps_link), twist=Twist(linear=Vector3(x=1.299, y=0.36, z=-0.065), angular=Vector3(x=0.0, y=0.0, z=0.0)))
/gps/diagnostics | 1773075276682039472 | diagnostic_msgs/msg/DiagnosticArray | DiagnosticArray(header=Header(stamp=Time(sec=1773075276, nanosec=681208403), frame_id=), status=[DiagnosticStatus(level=0, name=gnss_maxm10s_i2c, message=OK, hardware_id=, values=[KeyValue(key=i2c_addr, value=0x42), KeyValue(key=avail_bytes_last_poll, value=0), KeyValue(key=age_s_since_last_pvt, value=0.35)])])
/gps/fix | 1773075277332677067 | sensor_msgs/msg/NavSatFix | NavSatFix(header=Header(stamp=Time(sec=1773075277, nanosec=331695688), frame_id=gps_link), status=NavSatStatus(status=0, service=1), latitude=51.4768571, longitude=-0.0361082, altitude=7.027, position_covariance=[0.279841, 0.0, 0.0, 0.0, 0.279841, 0.0, 0.0, 0.0, 0.558009], position_covariance_type=2)
/gps/vel | 1773075277333208788 | geometry_msgs/msg/TwistStamped | TwistStamped(header=Header(stamp=Time(sec=1773075277, nanosec=331695688), frame_id=gps_link), twist=Twist(linear=Vector3(x=1.306, y=0.228, z=0.079), angular=Vector3(x=0.0, y=0.0, z=0.0)))
/gps/diagnostics | 1773075277682045498 | diagnostic_msgs/msg/DiagnosticArray | DiagnosticArray(header=Header(stamp=Time(sec=1773075277, nanosec=681248546), frame_id=), status=[DiagnosticStatus(level=0, name=gnss_maxm10s_i2c, message=OK, hardware_id=, values=[KeyValue(key=i2c_addr, value=0x42), KeyValue(key=avail_bytes_last_poll, value=0), KeyValue(key=age_s_since_last_pvt, value=0.35)])])
/gps/fix | 1773075279332846839 | sensor_msgs/msg/NavSatFix | NavSatFix(header=Header(stamp=Time(sec=1773075279, nanosec=331863465), frame_id=gps_link), status=NavSatStatus(status=0, service=1), latitude=51.4768616, longitude=-0.036070399999999996, altitude=7.241, position_covariance=[0.27144100000000004, 0.0, 0.0, 0.0, 0.27144100000000004, 0.0, 0.0, 0.0, 0.549081], position_covariance_type=2)
/gps/vel | 1773075279333411505 | geometry_msgs/msg/TwistStamped | TwistStamped(header=Header(stamp=Time(sec=1773075279, nanosec=331863465), frame_id=gps_link), twist=Twist(linear=Vector3(x=1.316, y=0.385, z=0.099), angular=Vector3(x=0.0, y=0.0, z=0.0)))
/gps/diagnostics | 1773075279334337262 | diagnostic_msgs/msg/DiagnosticArray | DiagnosticArray(header=Header(stamp=Time(sec=1773075279, nanosec=333601153), frame_id=), status=[DiagnosticStatus(level=0, name=gnss_maxm10s_i2c, message=OK, hardware_id=, values=[KeyValue(key=i2c_addr, value=0x42), KeyValue(key=avail_bytes_last_poll, value=100), KeyValue(key=age_s_since_last_pvt, value=0.00)])])
/gps/diagnostics | 1773075280681035577 | diagnostic_msgs/msg/DiagnosticArray | DiagnosticArray(header=Header(stamp=Time(sec=1773075280, nanosec=680370162), frame_id=), status=[DiagnosticStatus(level=0, name=gnss_maxm10s_i2c, message=OK, hardware_id=, values=[KeyValue(key=i2c_addr, value=0x42), KeyValue(key=avail_bytes_last_poll, value=0), KeyValue(key=age_s_since_last_pvt, value=1.35)])])
/gps/fix | 1773075281330956601 | sensor_msgs/msg/NavSatFix | NavSatFix(header=Header(stamp=Time(sec=1773075281, nanosec=330007421), frame_id=gps_link), status=NavSatStatus(status=0, service=1), latitude=51.4768687, longitude=-0.036036399999999996, altitude=7.11, position_covariance=[0.277729, 0.0, 0.0, 0.0, 0.277729, 0.0, 0.0, 0.0, 0.549081], position_covariance_type=2)
/gps/vel | 1773075281331531877 | geometry_msgs/msg/TwistStamped | TwistStamped(header=Header(stamp=Time(sec=1773075281, nanosec=330007421), frame_id=gps_link), twist=Twist(linear=Vector3(x=1.016, y=0.384, z=-0.09), angular=Vector3(x=0.0, y=0.0, z=0.0)))
/gps/diagnostics | 1773075281681981646 | diagnostic_msgs/msg/DiagnosticArray | DiagnosticArray(header=Header(stamp=Time(sec=1773075281, nanosec=681169293), frame_id=), status=[DiagnosticStatus(level=0, name=gnss_maxm10s_i2c, message=OK, hardware_id=, values=[KeyValue(key=i2c_addr, value=0x42), KeyValue(key=avail_bytes_last_poll, value=0), KeyValue(key=age_s_since_last_pvt, value=0.35)])])
/gps/fix | 1773075282331641878 | sensor_msgs/msg/NavSatFix | NavSatFix(header=Header(stamp=Time(sec=1773075282, nanosec=330661493), frame_id=gps_link), status=NavSatStatus(status=0, service=1), latitude=51.476872199999995, longitude=-0.036019999999999996, altitude=7.132, position_covariance=[0.29920900000000006, 0.0, 0.0, 0.0, 0.29920900000000006, 0.0, 0.0, 0.0, 0.5625], position_covariance_type=2)
/gps/vel | 1773075282332165869 | geometry_msgs/msg/TwistStamped | TwistStamped(header=Header(stamp=Time(sec=1773075282, nanosec=330661493), frame_id=gps_link), twist=Twist(linear=Vector3(x=1.137, y=0.363, z=0.018), angular=Vector3(x=0.0, y=0.0, z=0.0)))
/gps/fix | 1773075283324738694 | sensor_msgs/msg/NavSatFix | NavSatFix(header=Header(stamp=Time(sec=1773075283, nanosec=323735403), frame_id=gps_link), status=NavSatStatus(status=0, service=1), latitude=51.476875899999996, longitude=-0.036002599999999996, altitude=7.067, position_covariance=[0.32262399999999997, 0.0, 0.0, 0.0, 0.32262399999999997, 0.0, 0.0, 0.0, 0.5760810000000001], position_covariance_type=2)
/gps/vel | 1773075283325337950 | geometry_msgs/msg/TwistStamped | TwistStamped(header=Header(stamp=Time(sec=1773075283, nanosec=323735403), frame_id=gps_link), twist=Twist(linear=Vector3(x=1.226, y=0.441, z=-0.11), angular=Vector3(x=0.0, y=0.0, z=0.0)))
/gps/diagnostics | 1773075283326359577 | diagnostic_msgs/msg/DiagnosticArray | DiagnosticArray(header=Header(stamp=Time(sec=1773075283, nanosec=325604622), frame_id=), status=[DiagnosticStatus(level=0, name=gnss_maxm10s_i2c, message=OK, hardware_id=, values=[KeyValue(key=i2c_addr, value=0x42), KeyValue(key=avail_bytes_last_poll, value=100), KeyValue(key=age_s_since_last_pvt, value=0.00)])])
/gps/fix | 1773075284324400391 | sensor_msgs/msg/NavSatFix | NavSatFix(header=Header(stamp=Time(sec=1773075284, nanosec=323471757), frame_id=gps_link), status=NavSatStatus(status=0, service=1), latitude=51.4768787, longitude=-0.0359863, altitude=7.053, position_covariance=[0.343396, 0.0, 0.0, 0.0, 0.343396, 0.0, 0.0, 0.0, 0.5882890000000001], position_covariance_type=2)
/gps/vel | 1773075284325123471 | geometry_msgs/msg/TwistStamped | TwistStamped(header=Header(stamp=Time(sec=1773075284, nanosec=323471757), frame_id=gps_link), twist=Twist(linear=Vector3(x=1.059, y=0.24, z=-0.038), angular=Vector3(x=0.0, y=0.0, z=0.0)))
/gps/diagnostics | 1773075284682253008 | diagnostic_msgs/msg/DiagnosticArray | DiagnosticArray(header=Header(stamp=Time(sec=1773075284, nanosec=681507871), frame_id=), status=[DiagnosticStatus(level=0, name=gnss_maxm10s_i2c, message=OK, hardware_id=, values=[KeyValue(key=i2c_addr, value=0x42), KeyValue(key=avail_bytes_last_poll, value=0), KeyValue(key=age_s_since_last_pvt, value=0.36)])])
/gps/fix | 1773075285317034520 | sensor_msgs/msg/NavSatFix | NavSatFix(header=Header(stamp=Time(sec=1773075285, nanosec=316036179), frame_id=gps_link), status=NavSatStatus(status=0, service=1), latitude=51.476881999999996, longitude=-0.0359697, altitude=7.012, position_covariance=[0.37088099999999996, 0.0, 0.0, 0.0, 0.37088099999999996, 0.0, 0.0, 0.0, 0.6146560000000001], position_covariance_type=2)
/gps/vel | 1773075285317664980 | geometry_msgs/msg/TwistStamped | TwistStamped(header=Header(stamp=Time(sec=1773075285, nanosec=316036179), frame_id=gps_link), twist=Twist(linear=Vector3(x=1.187, y=0.461, z=-0.075), angular=Vector3(x=0.0, y=0.0, z=0.0)))
/gps/fix | 1773075286315596623 | sensor_msgs/msg/NavSatFix | NavSatFix(header=Header(stamp=Time(sec=1773075286, nanosec=314619581), frame_id=gps_link), status=NavSatStatus(status=0, service=1), latitude=51.476886799999996, longitude=-0.0359509, altitude=7.032, position_covariance=[0.380689, 0.0, 0.0, 0.0, 0.380689, 0.0, 0.0, 0.0, 0.616225], position_covariance_type=2)
/gps/vel | 1773075286316152760 | geometry_msgs/msg/TwistStamped | TwistStamped(header=Header(stamp=Time(sec=1773075286, nanosec=314619581), frame_id=gps_link), twist=Twist(linear=Vector3(x=1.276, y=0.574, z=-0.027), angular=Vector3(x=0.0, y=0.0, z=0.0)))
/gps/diagnostics | 1773075286317136024 | diagnostic_msgs/msg/DiagnosticArray | DiagnosticArray(header=Header(stamp=Time(sec=1773075286, nanosec=316442598), frame_id=), status=[DiagnosticStatus(level=0, name=gnss_maxm10s_i2c, message=OK, hardware_id=, values=[KeyValue(key=i2c_addr, value=0x42), KeyValue(key=avail_bytes_last_poll, value=100), KeyValue(key=age_s_since_last_pvt, value=0.00)])])
/gps/fix | 1773075287322128532 | sensor_msgs/msg/NavSatFix | NavSatFix(header=Header(stamp=Time(sec=1773075287, nanosec=321196070), frame_id=gps_link), status=NavSatStatus(status=0, service=1), latitude=51.47689, longitude=-0.035934299999999995, altitude=6.899, position_covariance=[0.388129, 0.0, 0.0, 0.0, 0.388129, 0.0, 0.0, 0.0, 0.620944], position_covariance_type=2)
/gps/vel | 1773075287322767656 | geometry_msgs/msg/TwistStamped | TwistStamped(header=Header(stamp=Time(sec=1773075287, nanosec=321196070), frame_id=gps_link), twist=Twist(linear=Vector3(x=1.055, y=0.289, z=-0.185), angular=Vector3(x=0.0, y=0.0, z=0.0)))
/gps/diagnostics | 1773075287323757492 | diagnostic_msgs/msg/DiagnosticArray | DiagnosticArray(header=Header(stamp=Time(sec=1773075287, nanosec=323004545), frame_id=), status=[DiagnosticStatus(level=0, name=gnss_maxm10s_i2c, message=OK, hardware_id=, values=[KeyValue(key=i2c_addr, value=0x42), KeyValue(key=avail_bytes_last_poll, value=100), KeyValue(key=age_s_since_last_pvt, value=0.00)])])
/gps/fix | 1773075288371495234 | sensor_msgs/msg/NavSatFix | NavSatFix(header=Header(stamp=Time(sec=1773075288, nanosec=370529661), frame_id=gps_link), status=NavSatStatus(status=0, service=1), latitude=51.476893, longitude=-0.0359212, altitude=6.876, position_covariance=[0.395641, 0.0, 0.0, 0.0, 0.395641, 0.0, 0.0, 0.0, 0.6225210000000001], position_covariance_type=2)
/gps/vel | 1773075288372541406 | geometry_msgs/msg/TwistStamped | TwistStamped(header=Header(stamp=Time(sec=1773075288, nanosec=370529661), frame_id=gps_link), twist=Twist(linear=Vector3(x=0.803, y=0.436, z=0.032), angular=Vector3(x=0.0, y=0.0, z=0.0)))
/gps/fix | 1773075289416343704 | sensor_msgs/msg/NavSatFix | NavSatFix(header=Header(stamp=Time(sec=1773075289, nanosec=415372762), frame_id=gps_link), status=NavSatStatus(status=0, service=1), latitude=51.4768955, longitude=-0.0359177, altitude=6.852, position_covariance=[0.405769, 0.0, 0.0, 0.0, 0.405769, 0.0, 0.0, 0.0, 0.6320250000000001], position_covariance_type=2)
/gps/vel | 1773075289416952990 | geometry_msgs/msg/TwistStamped | TwistStamped(header=Header(stamp=Time(sec=1773075289, nanosec=415372762), frame_id=gps_link), twist=Twist(linear=Vector3(x=0.02, y=0.24, z=0.008), angular=Vector3(x=0.0, y=0.0, z=0.0)))
/gps/fix | 1773075290402891724 | sensor_msgs/msg/NavSatFix | NavSatFix(header=Header(stamp=Time(sec=1773075290, nanosec=401910746), frame_id=gps_link), status=NavSatStatus(status=0, service=1), latitude=51.4768987, longitude=-0.0359099, altitude=6.875, position_covariance=[0.42250000000000004, 0.0, 0.0, 0.0, 0.42250000000000004, 0.0, 0.0, 0.0, 0.6561000000000001], position_covariance_type=2)
/gps/vel | 1773075290403444041 | geometry_msgs/msg/TwistStamped | TwistStamped(header=Header(stamp=Time(sec=1773075290, nanosec=401910746), frame_id=gps_link), twist=Twist(linear=Vector3(x=0.77, y=0.344, z=-0.002), angular=Vector3(x=0.0, y=0.0, z=0.0)))
/gps/fix | 1773075291477945135 | sensor_msgs/msg/NavSatFix | NavSatFix(header=Header(stamp=Time(sec=1773075291, nanosec=476955400), frame_id=gps_link), status=NavSatStatus(status=0, service=1), latitude=51.4768993, longitude=-0.0359129, altitude=6.852, position_covariance=[0.438244, 0.0, 0.0, 0.0, 0.438244, 0.0, 0.0, 0.0, 0.6839289999999999], position_covariance_type=2)
/gps/vel | 1773075291478675797 | geometry_msgs/msg/TwistStamped | TwistStamped(header=Header(stamp=Time(sec=1773075291, nanosec=476955400), frame_id=gps_link), twist=Twist(linear=Vector3(x=-0.669, y=-0.077, z=-0.01), angular=Vector3(x=0.0, y=0.0, z=0.0)))
/gps/fix | 1773075292549134911 | sensor_msgs/msg/NavSatFix | NavSatFix(header=Header(stamp=Time(sec=1773075292, nanosec=548154438), frame_id=gps_link), status=NavSatStatus(status=0, service=1), latitude=51.476897099999995, longitude=-0.0359247, altitude=6.785, position_covariance=[0.44488900000000003, 0.0, 0.0, 0.0, 0.44488900000000003, 0.0, 0.0, 0.0, 0.719104], position_covariance_type=2)
/gps/vel | 1773075292549845181 | geometry_msgs/msg/TwistStamped | TwistStamped(header=Header(stamp=Time(sec=1773075292, nanosec=548154438), frame_id=gps_link), twist=Twist(linear=Vector3(x=-0.839, y=-0.249, z=-0.028), angular=Vector3(x=0.0, y=0.0, z=0.0)))
/gps/fix | 1773075293606906181 | sensor_msgs/msg/NavSatFix | NavSatFix(header=Header(stamp=Time(sec=1773075293, nanosec=605806739), frame_id=gps_link), status=NavSatStatus(status=0, service=1), latitude=51.476895199999994, longitude=-0.0359392, altitude=6.819, position_covariance=[0.45562500000000006, 0.0, 0.0, 0.0, 0.45562500000000006, 0.0, 0.0, 0.0, 0.737881], position_covariance_type=2)
/gps/vel | 1773075293607687898 | geometry_msgs/msg/TwistStamped | TwistStamped(header=Header(stamp=Time(sec=1773075293, nanosec=605806739), frame_id=gps_link), twist=Twist(linear=Vector3(x=-1.065, y=-0.116, z=0.093), angular=Vector3(x=0.0, y=0.0, z=0.0)))
/gps/fix | 1773075294295486341 | sensor_msgs/msg/NavSatFix | NavSatFix(header=Header(stamp=Time(sec=1773075294, nanosec=294522929), frame_id=gps_link), status=NavSatStatus(status=0, service=1), latitude=51.4768957, longitude=-0.0359538, altitude=6.842, position_covariance=[0.4719690000000001, 0.0, 0.0, 0.0, 0.4719690000000001, 0.0, 0.0, 0.0, 0.744769], position_covariance_type=2)
/gps/vel | 1773075294296031598 | geometry_msgs/msg/TwistStamped | TwistStamped(header=Header(stamp=Time(sec=1773075294, nanosec=294522929), frame_id=gps_link), twist=Twist(linear=Vector3(x=-0.992, y=0.064, z=0.029), angular=Vector3(x=0.0, y=0.0, z=0.0)))
/gps/fix | 1773075296378429905 | sensor_msgs/msg/NavSatFix | NavSatFix(header=Header(stamp=Time(sec=1773075296, nanosec=377473885), frame_id=gps_link), status=NavSatStatus(status=0, service=1), latitude=51.4769082, longitude=-0.0359615, altitude=6.758, position_covariance=[0.508369, 0.0, 0.0, 0.0, 0.508369, 0.0, 0.0, 0.0, 0.770884], position_covariance_type=2)
/gps/vel | 1773075296379109741 | geometry_msgs/msg/TwistStamped | TwistStamped(header=Header(stamp=Time(sec=1773075296, nanosec=377473885), frame_id=gps_link), twist=Twist(linear=Vector3(x=0.25, y=0.746, z=-0.001), angular=Vector3(x=0.0, y=0.0, z=0.0)))
/rosout | 1773075298398694376 | rcl_interfaces/msg/Log | Log(stamp=Time(sec=1773075298, nanosec=398148438), level=30, name=gnss_maxm10s_i2c_node, msg=I2C read error: [Errno 121] Remote I/O error, file=/home/uclglider/glider_ws/install/glider_ros/lib/python3.12/site-packages/glider_ros/drivers/gnss_maxm10s_i2c_node.py, function=poll_once, line=296)
/gps/diagnostics | 1773075298404189531 | diagnostic_msgs/msg/DiagnosticArray | DiagnosticArray(header=Header(stamp=Time(sec=1773075298, nanosec=403482955), frame_id=), status=[DiagnosticStatus(level=1, name=gnss_maxm10s_i2c, message=No recent NAV-PVT, hardware_id=, values=[KeyValue(key=i2c_addr, value=0x42), KeyValue(key=avail_bytes_last_poll, value=0), KeyValue(key=age_s_since_last_pvt, value=2.03)])])
/gps/diagnostics | 1773075299681726021 | diagnostic_msgs/msg/DiagnosticArray | DiagnosticArray(header=Header(stamp=Time(sec=1773075299, nanosec=680905384), frame_id=), status=[DiagnosticStatus(level=1, name=gnss_maxm10s_i2c, message=No recent NAV-PVT, hardware_id=, values=[KeyValue(key=i2c_addr, value=0x42), KeyValue(key=avail_bytes_last_poll, value=0), KeyValue(key=age_s_since_last_pvt, value=3.30)])])
/gps/diagnostics | 1773075300682673582 | diagnostic_msgs/msg/DiagnosticArray | DiagnosticArray(header=Header(stamp=Time(sec=1773075300, nanosec=681867355), frame_id=), status=[DiagnosticStatus(level=1, name=gnss_maxm10s_i2c, message=No recent NAV-PVT, hardware_id=, values=[KeyValue(key=i2c_addr, value=0x42), KeyValue(key=avail_bytes_last_poll, value=0), KeyValue(key=age_s_since_last_pvt, value=4.30)])])
/gps/fix | 1773075301325649559 | sensor_msgs/msg/NavSatFix | NavSatFix(header=Header(stamp=Time(sec=1773075301, nanosec=324672641), frame_id=gps_link), status=NavSatStatus(status=0, service=1), latitude=51.4769125, longitude=-0.0359499, altitude=6.343, position_covariance=[0.616225, 0.0, 0.0, 0.0, 0.616225, 0.0, 0.0, 0.0, 0.8611840000000001], position_covariance_type=2)
/gps/vel | 1773075301326157640 | geometry_msgs/msg/TwistStamped | TwistStamped(header=Header(stamp=Time(sec=1773075301, nanosec=324672641), frame_id=gps_link), twist=Twist(linear=Vector3(x=0.007, y=0.034, z=0.21), angular=Vector3(x=0.0, y=0.0, z=0.0)))
/gps/diagnostics | 1773075301683143986 | diagnostic_msgs/msg/DiagnosticArray | DiagnosticArray(header=Header(stamp=Time(sec=1773075301, nanosec=682368948), frame_id=), status=[DiagnosticStatus(level=0, name=gnss_maxm10s_i2c, message=OK, hardware_id=, values=[KeyValue(key=i2c_addr, value=0x42), KeyValue(key=avail_bytes_last_poll, value=0), KeyValue(key=age_s_since_last_pvt, value=0.36)])])
/gps/fix | 1773075302338706015 | sensor_msgs/msg/NavSatFix | NavSatFix(header=Header(stamp=Time(sec=1773075302, nanosec=337741377), frame_id=gps_link), status=NavSatStatus(status=0, service=1), latitude=51.476913499999995, longitude=-0.0359472, altitude=6.498, position_covariance=[0.6225210000000001, 0.0, 0.0, 0.0, 0.6225210000000001, 0.0, 0.0, 0.0, 0.851929], position_covariance_type=2)
/gps/vel | 1773075302339334527 | geometry_msgs/msg/TwistStamped | TwistStamped(header=Header(stamp=Time(sec=1773075302, nanosec=337741377), frame_id=gps_link), twist=Twist(linear=Vector3(x=0.018, y=0.007, z=0.145), angular=Vector3(x=0.0, y=0.0, z=0.0)))
/gps/fix | 1773075303340603571 | sensor_msgs/msg/NavSatFix | NavSatFix(header=Header(stamp=Time(sec=1773075303, nanosec=339664472), frame_id=gps_link), status=NavSatStatus(status=0, service=1), latitude=51.4769139, longitude=-0.0359482, altitude=6.607, position_covariance=[0.5882890000000001, 0.0, 0.0, 0.0, 0.5882890000000001, 0.0, 0.0, 0.0, 0.8281000000000001], position_covariance_type=2)
/gps/vel | 1773075303341089853 | geometry_msgs/msg/TwistStamped | TwistStamped(header=Header(stamp=Time(sec=1773075303, nanosec=339664472), frame_id=gps_link), twist=Twist(linear=Vector3(x=0.006, y=0.004, z=0.017), angular=Vector3(x=0.0, y=0.0, z=0.0)))
/gps/diagnostics | 1773075303341991357 | diagnostic_msgs/msg/DiagnosticArray | DiagnosticArray(header=Header(stamp=Time(sec=1773075303, nanosec=341359273), frame_id=), status=[DiagnosticStatus(level=0, name=gnss_maxm10s_i2c, message=OK, hardware_id=, values=[KeyValue(key=i2c_addr, value=0x42), KeyValue(key=avail_bytes_last_poll, value=100), KeyValue(key=age_s_since_last_pvt, value=0.00)])])
/gps/fix | 1773075304343960427 | sensor_msgs/msg/NavSatFix | NavSatFix(header=Header(stamp=Time(sec=1773075304, nanosec=342993940), frame_id=gps_link), status=NavSatStatus(status=0, service=1), latitude=51.476912899999995, longitude=-0.0359509, altitude=6.776, position_covariance=[0.559504, 0.0, 0.0, 0.0, 0.559504, 0.0, 0.0, 0.0, 0.8082010000000001], position_covariance_type=2)
/gps/vel | 1773075304344735535 | geometry_msgs/msg/TwistStamped | TwistStamped(header=Header(stamp=Time(sec=1773075304, nanosec=342993940), frame_id=gps_link), twist=Twist(linear=Vector3(x=0.0, y=-0.004, z=0.024), angular=Vector3(x=0.0, y=0.0, z=0.0)))
/gps/diagnostics | 1773075304345472623 | diagnostic_msgs/msg/DiagnosticArray | DiagnosticArray(header=Header(stamp=Time(sec=1773075304, nanosec=344749610), frame_id=), status=[DiagnosticStatus(level=0, name=gnss_maxm10s_i2c, message=OK, hardware_id=, values=[KeyValue(key=i2c_addr, value=0x42), KeyValue(key=avail_bytes_last_poll, value=100), KeyValue(key=age_s_since_last_pvt, value=0.00)])])
/gps/fix | 1773075305326233218 | sensor_msgs/msg/NavSatFix | NavSatFix(header=Header(stamp=Time(sec=1773075305, nanosec=325320568), frame_id=gps_link), status=NavSatStatus(status=0, service=1), latitude=51.4769119, longitude=-0.0359526, altitude=6.835, position_covariance=[0.538756, 0.0, 0.0, 0.0, 0.538756, 0.0, 0.0, 0.0, 0.7938810000000001], position_covariance_type=2)
/gps/vel | 1773075305327528032 | geometry_msgs/msg/TwistStamped | TwistStamped(header=Header(stamp=Time(sec=1773075305, nanosec=325320568), frame_id=gps_link), twist=Twist(linear=Vector3(x=0.004, y=-0.002, z=0.001), angular=Vector3(x=0.0, y=0.0, z=0.0)))
/gps/diagnostics | 1773075305682584556 | diagnostic_msgs/msg/DiagnosticArray | DiagnosticArray(header=Header(stamp=Time(sec=1773075305, nanosec=681784689), frame_id=), status=[DiagnosticStatus(level=0, name=gnss_maxm10s_i2c, message=OK, hardware_id=, values=[KeyValue(key=i2c_addr, value=0x42), KeyValue(key=avail_bytes_last_poll, value=0), KeyValue(key=age_s_since_last_pvt, value=0.36)])])
/gps/fix | 1773075306329125790 | sensor_msgs/msg/NavSatFix | NavSatFix(header=Header(stamp=Time(sec=1773075306, nanosec=328139472), frame_id=gps_link), status=NavSatStatus(status=0, service=1), latitude=51.4769108, longitude=-0.0359551, altitude=6.647, position_covariance=[0.521284, 0.0, 0.0, 0.0, 0.521284, 0.0, 0.0, 0.0, 0.784996], position_covariance_type=2)
/gps/vel | 1773075306329688554 | geometry_msgs/msg/TwistStamped | TwistStamped(header=Header(stamp=Time(sec=1773075306, nanosec=328139472), frame_id=gps_link), twist=Twist(linear=Vector3(x=-0.097, y=0.0, z=-0.278), angular=Vector3(x=0.0, y=0.0, z=0.0)))
/gps/diagnostics | 1773075306682717616 | diagnostic_msgs/msg/DiagnosticArray | DiagnosticArray(header=Header(stamp=Time(sec=1773075306, nanosec=681970437), frame_id=), status=[DiagnosticStatus(level=0, name=gnss_maxm10s_i2c, message=OK, hardware_id=, values=[KeyValue(key=i2c_addr, value=0x42), KeyValue(key=avail_bytes_last_poll, value=0), KeyValue(key=age_s_since_last_pvt, value=0.35)])])
/gps/diagnostics | 1773075307683083809 | diagnostic_msgs/msg/DiagnosticArray | DiagnosticArray(header=Header(stamp=Time(sec=1773075307, nanosec=682399560), frame_id=), status=[DiagnosticStatus(level=0, name=gnss_maxm10s_i2c, message=OK, hardware_id=, values=[KeyValue(key=i2c_addr, value=0x42), KeyValue(key=avail_bytes_last_poll, value=0), KeyValue(key=age_s_since_last_pvt, value=1.35)])])
/gps/fix | 1773075308543509490 | sensor_msgs/msg/NavSatFix | NavSatFix(header=Header(stamp=Time(sec=1773075308, nanosec=542616975), frame_id=gps_link), status=NavSatStatus(status=0, service=1), latitude=51.4769107, longitude=-0.0359552, altitude=6.534, position_covariance=[0.5285289999999999, 0.0, 0.0, 0.0, 0.5285289999999999, 0.0, 0.0, 0.0, 0.842724], position_covariance_type=2)
/gps/vel | 1773075308544020564 | geometry_msgs/msg/TwistStamped | TwistStamped(header=Header(stamp=Time(sec=1773075308, nanosec=542616975), frame_id=gps_link), twist=Twist(linear=Vector3(x=-0.002, y=0.001, z=-0.01), angular=Vector3(x=0.0, y=0.0, z=0.0)))
/gps/fix | 1773075309264309348 | sensor_msgs/msg/NavSatFix | NavSatFix(header=Header(stamp=Time(sec=1773075309, nanosec=263339165), frame_id=gps_link), status=NavSatStatus(status=0, service=1), latitude=51.4769116, longitude=-0.0359551, altitude=6.622, position_covariance=[0.538756, 0.0, 0.0, 0.0, 0.538756, 0.0, 0.0, 0.0, 0.9216], position_covariance_type=2)
/gps/vel | 1773075309264885721 | geometry_msgs/msg/TwistStamped | TwistStamped(header=Header(stamp=Time(sec=1773075309, nanosec=263339165), frame_id=gps_link), twist=Twist(linear=Vector3(x=-0.001, y=0.003, z=-0.004), angular=Vector3(x=0.0, y=0.0, z=0.0)))
/gps/fix | 1773075310398550363 | sensor_msgs/msg/NavSatFix | NavSatFix(header=Header(stamp=Time(sec=1773075310, nanosec=397580496), frame_id=gps_link), status=NavSatStatus(status=0, service=1), latitude=51.4769125, longitude=-0.0359557, altitude=6.738, position_covariance=[0.5476, 0.0, 0.0, 0.0, 0.5476, 0.0, 0.0, 0.0, 0.992016], position_covariance_type=2)
/gps/vel | 1773075310399076047 | geometry_msgs/msg/TwistStamped | TwistStamped(header=Header(stamp=Time(sec=1773075310, nanosec=397580496), frame_id=gps_link), twist=Twist(linear=Vector3(x=-0.008, y=0.006, z=0.038), angular=Vector3(x=0.0, y=0.0, z=0.0)))
/gps/fix | 1773075311500004612 | sensor_msgs/msg/NavSatFix | NavSatFix(header=Header(stamp=Time(sec=1773075311, nanosec=499118824), frame_id=gps_link), status=NavSatStatus(status=0, service=1), latitude=51.4769125, longitude=-0.035955, altitude=6.653, position_covariance=[0.5625, 0.0, 0.0, 0.0, 0.5625, 0.0, 0.0, 0.0, 1.050625], position_covariance_type=2)
/gps/vel | 1773075311500507314 | geometry_msgs/msg/TwistStamped | TwistStamped(header=Header(stamp=Time(sec=1773075311, nanosec=499118824), frame_id=gps_link), twist=Twist(linear=Vector3(x=-0.013, y=0.004, z=0.018), angular=Vector3(x=0.0, y=0.0, z=0.0)))
/gps/fix | 1773075312604396843 | sensor_msgs/msg/NavSatFix | NavSatFix(header=Header(stamp=Time(sec=1773075312, nanosec=603513075), frame_id=gps_link), status=NavSatStatus(status=0, service=1), latitude=51.476912399999996, longitude=-0.0359549, altitude=6.479, position_covariance=[0.561001, 0.0, 0.0, 0.0, 0.561001, 0.0, 0.0, 0.0, 1.0424409999999997], position_covariance_type=2)
/gps/vel | 1773075312604868228 | geometry_msgs/msg/TwistStamped | TwistStamped(header=Header(stamp=Time(sec=1773075312, nanosec=603513075), frame_id=gps_link), twist=Twist(linear=Vector3(x=-0.027, y=-0.007, z=-0.072), angular=Vector3(x=0.0, y=0.0, z=0.0)))
/gps/fix | 1773075313313594423 | sensor_msgs/msg/NavSatFix | NavSatFix(header=Header(stamp=Time(sec=1773075313, nanosec=312557855), frame_id=gps_link), status=NavSatStatus(status=0, service=1), latitude=51.476912, longitude=-0.035955299999999996, altitude=6.222, position_covariance=[0.573049, 0.0, 0.0, 0.0, 0.573049, 0.0, 0.0, 0.0, 1.0547289999999998], position_covariance_type=2)
/gps/vel | 1773075313314357464 | geometry_msgs/msg/TwistStamped | TwistStamped(header=Header(stamp=Time(sec=1773075313, nanosec=312557855), frame_id=gps_link), twist=Twist(linear=Vector3(x=0.091, y=-0.015, z=-0.283), angular=Vector3(x=0.0, y=0.0, z=0.0)))
/gps/fix | 1773075314369601829 | sensor_msgs/msg/NavSatFix | NavSatFix(header=Header(stamp=Time(sec=1773075314, nanosec=368539355), frame_id=gps_link), status=NavSatStatus(status=0, service=1), latitude=51.476912, longitude=-0.0359566, altitude=6.144, position_covariance=[0.6115240000000001, 0.0, 0.0, 0.0, 0.6115240000000001, 0.0, 0.0, 0.0, 1.108809], position_covariance_type=2)
/gps/vel | 1773075314370045064 | geometry_msgs/msg/TwistStamped | TwistStamped(header=Header(stamp=Time(sec=1773075314, nanosec=368539355), frame_id=gps_link), twist=Twist(linear=Vector3(x=-0.007, y=-0.019, z=-0.123), angular=Vector3(x=0.0, y=0.0, z=0.0)))
/gps/fix | 1773075318499077768 | sensor_msgs/msg/NavSatFix | NavSatFix(header=Header(stamp=Time(sec=1773075318, nanosec=498096468), frame_id=gps_link), status=NavSatStatus(status=0, service=1), latitude=51.4769128, longitude=-0.0359585, altitude=6.604, position_covariance=[0.6099610000000001, 0.0, 0.0, 0.0, 0.6099610000000001, 0.0, 0.0, 0.0, 1.065024], position_covariance_type=2)
/gps/vel | 1773075318499700208 | geometry_msgs/msg/TwistStamped | TwistStamped(header=Header(stamp=Time(sec=1773075318, nanosec=498096468), frame_id=gps_link), twist=Twist(linear=Vector3(x=0.031, y=0.007, z=0.021), angular=Vector3(x=0.0, y=0.0, z=0.0)))
/gps/fix | 1773075319515163676 | sensor_msgs/msg/NavSatFix | NavSatFix(header=Header(stamp=Time(sec=1773075319, nanosec=514188211), frame_id=gps_link), status=NavSatStatus(status=0, service=1), latitude=51.476912, longitude=-0.0359588, altitude=6.402, position_covariance=[0.5882890000000001, 0.0, 0.0, 0.0, 0.5882890000000001, 0.0, 0.0, 0.0, 1.0383609999999999], position_covariance_type=2)
/gps/vel | 1773075319515707632 | geometry_msgs/msg/TwistStamped | TwistStamped(header=Header(stamp=Time(sec=1773075319, nanosec=514188211), frame_id=gps_link), twist=Twist(linear=Vector3(x=0.114, y=-0.092, z=-0.192), angular=Vector3(x=0.0, y=0.0, z=0.0)))
/gps/fix | 1773075322318343679 | sensor_msgs/msg/NavSatFix | NavSatFix(header=Header(stamp=Time(sec=1773075322, nanosec=317393348), frame_id=gps_link), status=NavSatStatus(status=0, service=1), latitude=51.476917199999995, longitude=-0.0359498, altitude=7.041, position_covariance=[0.543169, 0.0, 0.0, 0.0, 0.543169, 0.0, 0.0, 0.0, 0.986049], position_covariance_type=2)
/gps/vel | 1773075322319147804 | geometry_msgs/msg/TwistStamped | TwistStamped(header=Header(stamp=Time(sec=1773075322, nanosec=317393348), frame_id=gps_link), twist=Twist(linear=Vector3(x=1.066, y=0.447, z=0.176), angular=Vector3(x=0.0, y=0.0, z=0.0)))
/gps/fix | 1773075323449990923 | sensor_msgs/msg/NavSatFix | NavSatFix(header=Header(stamp=Time(sec=1773075323, nanosec=449020834), frame_id=gps_link), status=NavSatStatus(status=0, service=1), latitude=51.476917199999995, longitude=-0.0359315, altitude=7.151, position_covariance=[0.525625, 0.0, 0.0, 0.0, 0.525625, 0.0, 0.0, 0.0, 0.9506249999999999], position_covariance_type=2)
/gps/vel | 1773075323450503746 | geometry_msgs/msg/TwistStamped | TwistStamped(header=Header(stamp=Time(sec=1773075323, nanosec=449020834), frame_id=gps_link), twist=Twist(linear=Vector3(x=1.18, y=-0.316, z=-0.057), angular=Vector3(x=0.0, y=0.0, z=0.0)))
/gps/fix | 1773075324548113204 | sensor_msgs/msg/NavSatFix | NavSatFix(header=Header(stamp=Time(sec=1773075324, nanosec=547153172), frame_id=gps_link), status=NavSatStatus(status=0, service=1), latitude=51.4769144, longitude=-0.035914499999999995, altitude=6.955, position_covariance=[0.506944, 0.0, 0.0, 0.0, 0.506944, 0.0, 0.0, 0.0, 0.9158489999999999], position_covariance_type=2)
/gps/vel | 1773075324548690361 | geometry_msgs/msg/TwistStamped | TwistStamped(header=Header(stamp=Time(sec=1773075324, nanosec=547153172), frame_id=gps_link), twist=Twist(linear=Vector3(x=1.052, y=-0.318, z=-0.143), angular=Vector3(x=0.0, y=0.0, z=0.0)))
/gps/fix | 1773075326404399213 | sensor_msgs/msg/NavSatFix | NavSatFix(header=Header(stamp=Time(sec=1773075326, nanosec=403428386), frame_id=gps_link), status=NavSatStatus(status=0, service=1), latitude=51.4769071, longitude=-0.0358746, altitude=6.96, position_covariance=[0.47059600000000007, 0.0, 0.0, 0.0, 0.47059600000000007, 0.0, 0.0, 0.0, 0.8742250000000001], position_covariance_type=2)
/gps/vel | 1773075326404926553 | geometry_msgs/msg/TwistStamped | TwistStamped(header=Header(stamp=Time(sec=1773075326, nanosec=403428386), frame_id=gps_link), twist=Twist(linear=Vector3(x=1.345, y=-0.327, z=0.008), angular=Vector3(x=0.0, y=0.0, z=0.0)))
/gps/fix | 1773075327522987902 | sensor_msgs/msg/NavSatFix | NavSatFix(header=Header(stamp=Time(sec=1773075327, nanosec=522017947), frame_id=gps_link), status=NavSatStatus(status=0, service=1), latitude=51.476906299999996, longitude=-0.0358546, altitude=6.837, position_covariance=[0.45427600000000007, 0.0, 0.0, 0.0, 0.45427600000000007, 0.0, 0.0, 0.0, 0.848241], position_covariance_type=2)
/gps/vel | 1773075327523557315 | geometry_msgs/msg/TwistStamped | TwistStamped(header=Header(stamp=Time(sec=1773075327, nanosec=522017947), frame_id=gps_link), twist=Twist(linear=Vector3(x=1.279, y=-0.081, z=-0.197), angular=Vector3(x=0.0, y=0.0, z=0.0)))
/gps/fix | 1773075329283945441 | sensor_msgs/msg/NavSatFix | NavSatFix(header=Header(stamp=Time(sec=1773075329, nanosec=283002989), frame_id=gps_link), status=NavSatStatus(status=0, service=1), latitude=51.476906199999995, longitude=-0.035813899999999996, altitude=6.872, position_covariance=[0.43560000000000004, 0.0, 0.0, 0.0, 0.43560000000000004, 0.0, 0.0, 0.0, 0.8335690000000001], position_covariance_type=2)
/gps/vel | 1773075329284397538 | geometry_msgs/msg/TwistStamped | TwistStamped(header=Header(stamp=Time(sec=1773075329, nanosec=283002989), frame_id=gps_link), twist=Twist(linear=Vector3(x=1.344, y=0.013, z=0.095), angular=Vector3(x=0.0, y=0.0, z=0.0)))
/gps/fix | 1773075330338073645 | sensor_msgs/msg/NavSatFix | NavSatFix(header=Header(stamp=Time(sec=1773075330, nanosec=337112230), frame_id=gps_link), status=NavSatStatus(status=0, service=1), latitude=51.4769066, longitude=-0.0357928, altitude=6.785, position_covariance=[0.45832900000000004, 0.0, 0.0, 0.0, 0.45832900000000004, 0.0, 0.0, 0.0, 0.8649000000000001], position_covariance_type=2)
/gps/vel | 1773075330338626871 | geometry_msgs/msg/TwistStamped | TwistStamped(header=Header(stamp=Time(sec=1773075330, nanosec=337112230), frame_id=gps_link), twist=Twist(linear=Vector3(x=1.433, y=0.029, z=-0.135), angular=Vector3(x=0.0, y=0.0, z=0.0)))
/gps/fix | 1773075331391611528 | sensor_msgs/msg/NavSatFix | NavSatFix(header=Header(stamp=Time(sec=1773075331, nanosec=390644837), frame_id=gps_link), status=NavSatStatus(status=0, service=1), latitude=51.4769072, longitude=-0.0357733, altitude=6.621, position_covariance=[0.4719690000000001, 0.0, 0.0, 0.0, 0.4719690000000001, 0.0, 0.0, 0.0, 0.8630410000000001], position_covariance_type=2)
/gps/vel | 1773075331392120160 | geometry_msgs/msg/TwistStamped | TwistStamped(header=Header(stamp=Time(sec=1773075331, nanosec=390644837), frame_id=gps_link), twist=Twist(linear=Vector3(x=1.241, y=0.095, z=-0.096), angular=Vector3(x=0.0, y=0.0, z=0.0)))
/gps/fix | 1773075332495443605 | sensor_msgs/msg/NavSatFix | NavSatFix(header=Header(stamp=Time(sec=1773075332, nanosec=494477433), frame_id=gps_link), status=NavSatStatus(status=0, service=1), latitude=51.476907, longitude=-0.0357539, altitude=6.65, position_covariance=[0.45697600000000005, 0.0, 0.0, 0.0, 0.45697600000000005, 0.0, 0.0, 0.0, 0.8464], position_covariance_type=2)
/gps/vel | 1773075332495981089 | geometry_msgs/msg/TwistStamped | TwistStamped(header=Header(stamp=Time(sec=1773075332, nanosec=494477433), frame_id=gps_link), twist=Twist(linear=Vector3(x=1.222, y=-0.071, z=0.015), angular=Vector3(x=0.0, y=0.0, z=0.0)))
/gps/fix | 1773075333611903530 | sensor_msgs/msg/NavSatFix | NavSatFix(header=Header(stamp=Time(sec=1773075333, nanosec=610857619), frame_id=gps_link), status=NavSatStatus(status=0, service=1), latitude=51.476906299999996, longitude=-0.0357346, altitude=6.753, position_covariance=[0.44355600000000006, 0.0, 0.0, 0.0, 0.44355600000000006, 0.0, 0.0, 0.0, 0.8244640000000001], position_covariance_type=2)
/gps/vel | 1773075333612694885 | geometry_msgs/msg/TwistStamped | TwistStamped(header=Header(stamp=Time(sec=1773075333, nanosec=610857619), frame_id=gps_link), twist=Twist(linear=Vector3(x=1.255, y=-0.096, z=0.069), angular=Vector3(x=0.0, y=0.0, z=0.0)))
/gps/fix | 1773075334344197305 | sensor_msgs/msg/NavSatFix | NavSatFix(header=Header(stamp=Time(sec=1773075334, nanosec=343258007), frame_id=gps_link), status=NavSatStatus(status=0, service=1), latitude=51.476905599999995, longitude=-0.035715199999999996, altitude=6.652, position_covariance=[0.43428100000000003, 0.0, 0.0, 0.0, 0.43428100000000003, 0.0, 0.0, 0.0, 0.801025], position_covariance_type=2)
/gps/vel | 1773075334344756103 | geometry_msgs/msg/TwistStamped | TwistStamped(header=Header(stamp=Time(sec=1773075334, nanosec=343258007), frame_id=gps_link), twist=Twist(linear=Vector3(x=1.325, y=-0.043, z=0.016), angular=Vector3(x=0.0, y=0.0, z=0.0)))
/gps/fix | 1773075335405645312 | sensor_msgs/msg/NavSatFix | NavSatFix(header=Header(stamp=Time(sec=1773075335, nanosec=404557699), frame_id=gps_link), status=NavSatStatus(status=0, service=1), latitude=51.4769052, longitude=-0.035695899999999996, altitude=6.587, position_covariance=[0.42380100000000004, 0.0, 0.0, 0.0, 0.42380100000000004, 0.0, 0.0, 0.0, 0.784996], position_covariance_type=2)
/gps/vel | 1773075335406184498 | geometry_msgs/msg/TwistStamped | TwistStamped(header=Header(stamp=Time(sec=1773075335, nanosec=404557699), frame_id=gps_link), twist=Twist(linear=Vector3(x=1.267, y=-0.05, z=-0.057), angular=Vector3(x=0.0, y=0.0, z=0.0)))
/gps/fix | 1773075336470126771 | sensor_msgs/msg/NavSatFix | NavSatFix(header=Header(stamp=Time(sec=1773075336, nanosec=469168974), frame_id=gps_link), status=NavSatStatus(status=0, service=1), latitude=51.476905099999996, longitude=-0.035675899999999997, altitude=6.651, position_covariance=[0.418609, 0.0, 0.0, 0.0, 0.418609, 0.0, 0.0, 0.0, 0.767376], position_covariance_type=2)
/gps/vel | 1773075336470676771 | geometry_msgs/msg/TwistStamped | TwistStamped(header=Header(stamp=Time(sec=1773075336, nanosec=469168974), frame_id=gps_link), twist=Twist(linear=Vector3(x=1.275, y=-0.053, z=0.05), angular=Vector3(x=0.0, y=0.0, z=0.0)))
/gps/fix | 1773075337495870561 | sensor_msgs/msg/NavSatFix | NavSatFix(header=Header(stamp=Time(sec=1773075337, nanosec=494904728), frame_id=gps_link), status=NavSatStatus(status=0, service=1), latitude=51.476906199999995, longitude=-0.035657299999999996, altitude=6.77, position_covariance=[0.419904, 0.0, 0.0, 0.0, 0.419904, 0.0, 0.0, 0.0, 0.755161], position_covariance_type=2)
/gps/vel | 1773075337496410598 | geometry_msgs/msg/TwistStamped | TwistStamped(header=Header(stamp=Time(sec=1773075337, nanosec=494904728), frame_id=gps_link), twist=Twist(linear=Vector3(x=1.286, y=0.166, z=0.138), angular=Vector3(x=0.0, y=0.0, z=0.0)))
/gps/fix | 1773075338559511693 | sensor_msgs/msg/NavSatFix | NavSatFix(header=Header(stamp=Time(sec=1773075338, nanosec=558546306), frame_id=gps_link), status=NavSatStatus(status=0, service=1), latitude=51.4769082, longitude=-0.0356379, altitude=6.727, position_covariance=[0.43428100000000003, 0.0, 0.0, 0.0, 0.43428100000000003, 0.0, 0.0, 0.0, 0.749956], position_covariance_type=2)
/gps/vel | 1773075338560137285 | geometry_msgs/msg/TwistStamped | TwistStamped(header=Header(stamp=Time(sec=1773075338, nanosec=558546306), frame_id=gps_link), twist=Twist(linear=Vector3(x=1.298, y=0.184, z=-0.137), angular=Vector3(x=0.0, y=0.0, z=0.0)))
/gps/fix | 1773075339291386679 | sensor_msgs/msg/NavSatFix | NavSatFix(header=Header(stamp=Time(sec=1773075339, nanosec=290429848), frame_id=gps_link), status=NavSatStatus(status=0, service=1), latitude=51.47691, longitude=-0.0356196, altitude=6.732, position_covariance=[0.45158400000000004, 0.0, 0.0, 0.0, 0.45158400000000004, 0.0, 0.0, 0.0, 0.744769], position_covariance_type=2)
/gps/vel | 1773075339292177473 | geometry_msgs/msg/TwistStamped | TwistStamped(header=Header(stamp=Time(sec=1773075339, nanosec=290429848), frame_id=gps_link), twist=Twist(linear=Vector3(x=1.154, y=0.155, z=-0.045), angular=Vector3(x=0.0, y=0.0, z=0.0)))
/gps/fix | 1773075341530942212 | sensor_msgs/msg/NavSatFix | NavSatFix(header=Header(stamp=Time(sec=1773075341, nanosec=529947087), frame_id=gps_link), status=NavSatStatus(status=0, service=1), latitude=51.4769128, longitude=-0.0355827, altitude=6.92, position_covariance=[0.46922500000000006, 0.0, 0.0, 0.0, 0.46922500000000006, 0.0, 0.0, 0.0, 0.7327359999999999], position_covariance_type=2)
/gps/vel | 1773075341531488950 | geometry_msgs/msg/TwistStamped | TwistStamped(header=Header(stamp=Time(sec=1773075341, nanosec=529947087), frame_id=gps_link), twist=Twist(linear=Vector3(x=1.311, y=0.123, z=0.035), angular=Vector3(x=0.0, y=0.0, z=0.0)))
/gps/fix | 1773075342591037182 | sensor_msgs/msg/NavSatFix | NavSatFix(header=Header(stamp=Time(sec=1773075342, nanosec=589901059), frame_id=gps_link), status=NavSatStatus(status=0, service=1), latitude=51.476912299999995, longitude=-0.0355636, altitude=6.913, position_covariance=[0.48580899999999994, 0.0, 0.0, 0.0, 0.48580899999999994, 0.0, 0.0, 0.0, 0.7395999999999999], position_covariance_type=2)
/gps/vel | 1773075342591855974 | geometry_msgs/msg/TwistStamped | TwistStamped(header=Header(stamp=Time(sec=1773075342, nanosec=589901059), frame_id=gps_link), twist=Twist(linear=Vector3(x=1.292, y=-0.059, z=0.002), angular=Vector3(x=0.0, y=0.0, z=0.0)))
/gps/fix | 1773075343348911164 | sensor_msgs/msg/NavSatFix | NavSatFix(header=Header(stamp=Time(sec=1773075343, nanosec=347934874), frame_id=gps_link), status=NavSatStatus(status=0, service=1), latitude=51.4769125, longitude=-0.0355445, altitude=7.053, position_covariance=[0.4872039999999999, 0.0, 0.0, 0.0, 0.4872039999999999, 0.0, 0.0, 0.0, 0.7310249999999999], position_covariance_type=2)
/gps/vel | 1773075343349508531 | geometry_msgs/msg/TwistStamped | TwistStamped(header=Header(stamp=Time(sec=1773075343, nanosec=347934874), frame_id=gps_link), twist=Twist(linear=Vector3(x=1.275, y=0.123, z=0.181), angular=Vector3(x=0.0, y=0.0, z=0.0)))
/gps/fix | 1773075344458552995 | sensor_msgs/msg/NavSatFix | NavSatFix(header=Header(stamp=Time(sec=1773075344, nanosec=457592261), frame_id=gps_link), status=NavSatStatus(status=0, service=1), latitude=51.476914799999996, longitude=-0.0355263, altitude=7.381, position_covariance=[0.4872039999999999, 0.0, 0.0, 0.0, 0.4872039999999999, 0.0, 0.0, 0.0, 0.724201], position_covariance_type=2)
/gps/vel | 1773075344459057677 | geometry_msgs/msg/TwistStamped | TwistStamped(header=Header(stamp=Time(sec=1773075344, nanosec=457592261), frame_id=gps_link), twist=Twist(linear=Vector3(x=1.263, y=0.295, z=0.284), angular=Vector3(x=0.0, y=0.0, z=0.0)))
/gps/fix | 1773075345567024041 | sensor_msgs/msg/NavSatFix | NavSatFix(header=Header(stamp=Time(sec=1773075345, nanosec=565815125), frame_id=gps_link), status=NavSatStatus(status=0, service=1), latitude=51.4769179, longitude=-0.035509399999999997, altitude=7.564, position_covariance=[0.512656, 0.0, 0.0, 0.0, 0.512656, 0.0, 0.0, 0.0, 0.7361639999999999], position_covariance_type=2)
/gps/vel | 1773075345567662739 | geometry_msgs/msg/TwistStamped | TwistStamped(header=Header(stamp=Time(sec=1773075345, nanosec=565815125), frame_id=gps_link), twist=Twist(linear=Vector3(x=1.15, y=0.379, z=0.099), angular=Vector3(x=0.0, y=0.0, z=0.0)))
/gps/fix | 1773075346249702161 | sensor_msgs/msg/NavSatFix | NavSatFix(header=Header(stamp=Time(sec=1773075346, nanosec=248624041), frame_id=gps_link), status=NavSatStatus(status=0, service=1), latitude=51.4769193, longitude=-0.0354926, altitude=7.589, position_covariance=[0.5505639999999999, 0.0, 0.0, 0.0, 0.5505639999999999, 0.0, 0.0, 0.0, 0.7779240000000001], position_covariance_type=2)
/gps/vel | 1773075346250247786 | geometry_msgs/msg/TwistStamped | TwistStamped(header=Header(stamp=Time(sec=1773075346, nanosec=248624041), frame_id=gps_link), twist=Twist(linear=Vector3(x=1.114, y=0.252, z=0.107), angular=Vector3(x=0.0, y=0.0, z=0.0)))
/gps/fix | 1773075347299559883 | sensor_msgs/msg/NavSatFix | NavSatFix(header=Header(stamp=Time(sec=1773075347, nanosec=298628725), frame_id=gps_link), status=NavSatStatus(status=0, service=1), latitude=51.4769205, longitude=-0.035475599999999996, altitude=7.696, position_covariance=[0.5625, 0.0, 0.0, 0.0, 0.5625, 0.0, 0.0, 0.0, 0.7921], position_covariance_type=2)
/gps/vel | 1773075347300076396 | geometry_msgs/msg/TwistStamped | TwistStamped(header=Header(stamp=Time(sec=1773075347, nanosec=298628725), frame_id=gps_link), twist=Twist(linear=Vector3(x=1.162, y=0.199, z=0.126), angular=Vector3(x=0.0, y=0.0, z=0.0)))
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
