James-Jiang0821/GLIDER/ROS2_TESTING/imu_test_2_16-03-2026/split_topics_csv/imu_data_raw.csv

log_time_ns | topic | type | message
1773683789920624475 | /imu/data_raw | sensor_msgs/msg/Imu | Imu(header=Header(stamp=Time(sec=1773683789, nanosec=919606372), frame_id=imu_link), orientation=Quaternion(x=0.0, y=0.0, z=0.0, w=0.0), orientation_covariance=[-1.0, 0.0, 0.0, 0.0, 0.0, 0.0, 0.0, 0.0, 0.0], angular_velocity=Vector3(x=-0.001953125, y=0.00390625, z=-0.001953125), angular_velocity_covariance=[0.01, 0.0, 0.0, 0.0, 0.01, 0.0, 0.0, 0.0, 0.01], linear_acceleration=Vector3(x=-1.72265625, y=3.44921875, z=-9.1953125), linear_acceleration_covariance=[0.01, 0.0, 0.0, 0.0, 0.01, 0.0, 0.0, 0.0, 0.01])
1773683790028803866 | /imu/data_raw | sensor_msgs/msg/Imu | Imu(header=Header(stamp=Time(sec=1773683790, nanosec=27791693), frame_id=imu_link), orientation=Quaternion(x=0.0, y=0.0, z=0.0, w=0.0), orientation_covariance=[-1.0, 0.0, 0.0, 0.0, 0.0, 0.0, 0.0, 0.0, 0.0], angular_velocity=Vector3(x=-0.00390625, y=-0.001953125, z=-0.001953125), angular_velocity_covariance=[0.01, 0.0, 0.0, 0.0, 0.01, 0.0, 0.0, 0.0, 0.01], linear_acceleration=Vector3(x=-1.72265625, y=3.44921875, z=-9.1953125), linear_acceleration_covariance=[0.01, 0.0, 0.0, 0.0, 0.01, 0.0, 0.0, 0.0, 0.01])
1773683790121813846 | /imu/data_raw | sensor_msgs/msg/Imu | Imu(header=Header(stamp=Time(sec=1773683790, nanosec=120694306), frame_id=imu_link), orientation=Quaternion(x=0.0, y=0.0, z=0.0, w=0.0), orientation_covariance=[-1.0, 0.0, 0.0, 0.0, 0.0, 0.0, 0.0, 0.0, 0.0], angular_velocity=Vector3(x=0.001953125, y=-0.00390625, z=-0.00390625), angular_velocity_covariance=[0.01, 0.0, 0.0, 0.0, 0.01, 0.0, 0.0, 0.0, 0.01], linear_acceleration=Vector3(x=-1.72265625, y=3.44921875, z=-9.1953125), linear_acceleration_covariance=[0.01, 0.0, 0.0, 0.0, 0.01, 0.0, 0.0, 0.0, 0.01])
1773683790222728758 | /imu/data_raw | sensor_msgs/msg/Imu | Imu(header=Header(stamp=Time(sec=1773683790, nanosec=221433695), frame_id=imu_link), orientation=Quaternion(x=0.0, y=0.0, z=0.0, w=0.0), orientation_covariance=[-1.0, 0.0, 0.0, 0.0, 0.0, 0.0, 0.0, 0.0, 0.0], angular_velocity=Vector3(x=-0.001953125, y=0.00390625, z=0.0), angular_velocity_covariance=[0.01, 0.0, 0.0, 0.0, 0.01, 0.0, 0.0, 0.0, 0.01], linear_acceleration=Vector3(x=-1.72265625, y=3.44921875, z=-9.1953125), linear_acceleration_covariance=[0.01, 0.0, 0.0, 0.0, 0.01, 0.0, 0.0, 0.0, 0.01])
1773683790321645161 | /imu/data_raw | sensor_msgs/msg/Imu | Imu(header=Header(stamp=Time(sec=1773683790, nanosec=320532790), frame_id=imu_link), orientation=Quaternion(x=0.0, y=0.0, z=0.0, w=0.0), orientation_covariance=[-1.0, 0.0, 0.0, 0.0, 0.0, 0.0, 0.0, 0.0, 0.0], angular_velocity=Vector3(x=-0.001953125, y=-0.001953125, z=-0.001953125), angular_velocity_covariance=[0.01, 0.0, 0.0, 0.0, 0.01, 0.0, 0.0, 0.0, 0.01], linear_acceleration=Vector3(x=-1.76171875, y=3.44921875, z=-9.1953125), linear_acceleration_covariance=[0.01, 0.0, 0.0, 0.0, 0.01, 0.0, 0.0, 0.0, 0.01])
1773683790423591657 | /imu/data_raw | sensor_msgs/msg/Imu | Imu(header=Header(stamp=Time(sec=1773683790, nanosec=422443095), frame_id=imu_link), orientation=Quaternion(x=0.0, y=0.0, z=0.0, w=0.0), orientation_covariance=[-1.0, 0.0, 0.0, 0.0, 0.0, 0.0, 0.0, 0.0, 0.0], angular_velocity=Vector3(x=-0.001953125, y=0.0, z=0.001953125), angular_velocity_covariance=[0.01, 0.0, 0.0, 0.0, 0.01, 0.0, 0.0, 0.0, 0.01], linear_acceleration=Vector3(x=-1.76171875, y=3.484375, z=-9.1953125), linear_acceleration_covariance=[0.01, 0.0, 0.0, 0.0, 0.01, 0.0, 0.0, 0.0, 0.01])
1773683790522014975 | /imu/data_raw | sensor_msgs/msg/Imu | Imu(header=Header(stamp=Time(sec=1773683790, nanosec=520894139), frame_id=imu_link), orientation=Quaternion(x=0.0, y=0.0, z=0.0, w=0.0), orientation_covariance=[-1.0, 0.0, 0.0, 0.0, 0.0, 0.0, 0.0, 0.0, 0.0], angular_velocity=Vector3(x=-0.001953125, y=0.001953125, z=0.001953125), angular_velocity_covariance=[0.01, 0.0, 0.0, 0.0, 0.01, 0.0, 0.0, 0.0, 0.01], linear_acceleration=Vector3(x=-1.76171875, y=3.44921875, z=-9.1953125), linear_acceleration_covariance=[0.01, 0.0, 0.0, 0.0, 0.01, 0.0, 0.0, 0.0, 0.01])
1773683790625544480 | /imu/data_raw | sensor_msgs/msg/Imu | Imu(header=Header(stamp=Time(sec=1773683790, nanosec=624489171), frame_id=imu_link), orientation=Quaternion(x=0.0, y=0.0, z=0.0, w=0.0), orientation_covariance=[-1.0, 0.0, 0.0, 0.0, 0.0, 0.0, 0.0, 0.0, 0.0], angular_velocity=Vector3(x=0.0, y=0.001953125, z=0.001953125), angular_velocity_covariance=[0.01, 0.0, 0.0, 0.0, 0.01, 0.0, 0.0, 0.0, 0.01], linear_acceleration=Vector3(x=-1.72265625, y=3.44921875, z=-9.1953125), linear_acceleration_covariance=[0.01, 0.0, 0.0, 0.0, 0.01, 0.0, 0.0, 0.0, 0.01])
1773683790724396171 | /imu/data_raw | sensor_msgs/msg/Imu | Imu(header=Header(stamp=Time(sec=1773683790, nanosec=723374293), frame_id=imu_link), orientation=Quaternion(x=0.0, y=0.0, z=0.0, w=0.0), orientation_covariance=[-1.0, 0.0, 0.0, 0.0, 0.0, 0.0, 0.0, 0.0, 0.0], angular_velocity=Vector3(x=-0.001953125, y=0.001953125, z=-0.001953125), angular_velocity_covariance=[0.01, 0.0, 0.0, 0.0, 0.01, 0.0, 0.0, 0.0, 0.01], linear_acceleration=Vector3(x=-1.76171875, y=3.44921875, z=-9.1953125), linear_acceleration_covariance=[0.01, 0.0, 0.0, 0.0, 0.01, 0.0, 0.0, 0.0, 0.01])
1773683790826477647 | /imu/data_raw | sensor_msgs/msg/Imu | Imu(header=Header(stamp=Time(sec=1773683790, nanosec=825326937), frame_id=imu_link), orientation=Quaternion(x=0.0, y=0.0, z=0.0, w=0.0), orientation_covariance=[-1.0, 0.0, 0.0, 0.0, 0.0, 0.0, 0.0, 0.0, 0.0], angular_velocity=Vector3(x=-0.001953125, y=0.00390625, z=0.001953125), angular_velocity_covariance=[0.01, 0.0, 0.0, 0.0, 0.01, 0.0, 0.0, 0.0, 0.01], linear_acceleration=Vector3(x=-1.76171875, y=3.44921875, z=-9.1953125), linear_acceleration_covariance=[0.01, 0.0, 0.0, 0.0, 0.01, 0.0, 0.0, 0.0, 0.01])
1773683790925621229 | /imu/data_raw | sensor_msgs/msg/Imu | Imu(header=Header(stamp=Time(sec=1773683790, nanosec=924500764), frame_id=imu_link), orientation=Quaternion(x=0.0, y=0.0, z=0.0, w=0.0), orientation_covariance=[-1.0, 0.0, 0.0, 0.0, 0.0, 0.0, 0.0, 0.0, 0.0], angular_velocity=Vector3(x=-0.001953125, y=-0.001953125, z=0.0), angular_velocity_covariance=[0.01, 0.0, 0.0, 0.0, 0.01, 0.0, 0.0, 0.0, 0.01], linear_acceleration=Vector3(x=-1.76171875, y=3.484375, z=-9.1953125), linear_acceleration_covariance=[0.01, 0.0, 0.0, 0.0, 0.01, 0.0, 0.0, 0.0, 0.01])
1773683791025983945 | /imu/data_raw | sensor_msgs/msg/Imu | Imu(header=Header(stamp=Time(sec=1773683791, nanosec=24838629), frame_id=imu_link), orientation=Quaternion(x=0.0, y=0.0, z=0.0, w=0.0), orientation_covariance=[-1.0, 0.0, 0.0, 0.0, 0.0, 0.0, 0.0, 0.0, 0.0], angular_velocity=Vector3(x=0.0, y=0.0, z=-0.00390625), angular_velocity_covariance=[0.01, 0.0, 0.0, 0.0, 0.01, 0.0, 0.0, 0.0, 0.01], linear_acceleration=Vector3(x=-1.72265625, y=3.44921875, z=-9.1953125), linear_acceleration_covariance=[0.01, 0.0, 0.0, 0.0, 0.01, 0.0, 0.0, 0.0, 0.01])
1773683791129997611 | /imu/data_raw | sensor_msgs/msg/Imu | Imu(header=Header(stamp=Time(sec=1773683791, nanosec=128807233), frame_id=imu_link), orientation=Quaternion(x=0.0, y=0.0, z=0.0, w=0.0), orientation_covariance=[-1.0, 0.0, 0.0, 0.0, 0.0, 0.0, 0.0, 0.0, 0.0], angular_velocity=Vector3(x=0.001953125, y=0.001953125, z=0.0), angular_velocity_covariance=[0.01, 0.0, 0.0, 0.0, 0.01, 0.0, 0.0, 0.0, 0.01], linear_acceleration=Vector3(x=-1.76171875, y=3.44921875, z=-9.1953125), linear_acceleration_covariance=[0.01, 0.0, 0.0, 0.0, 0.01, 0.0, 0.0, 0.0, 0.01])
1773683791207995631 | /imu/data_raw | sensor_msgs/msg/Imu | Imu(header=Header(stamp=Time(sec=1773683791, nanosec=206852611), frame_id=imu_link), orientation=Quaternion(x=0.0, y=0.0, z=0.0, w=0.0), orientation_covariance=[-1.0, 0.0, 0.0, 0.0, 0.0, 0.0, 0.0, 0.0, 0.0], angular_velocity=Vector3(x=-0.001953125, y=0.001953125, z=0.0), angular_velocity_covariance=[0.01, 0.0, 0.0, 0.0, 0.01, 0.0, 0.0, 0.0, 0.01], linear_acceleration=Vector3(x=-1.76171875, y=3.484375, z=-9.1953125), linear_acceleration_covariance=[0.01, 0.0, 0.0, 0.0, 0.01, 0.0, 0.0, 0.0, 0.01])
1773683791330012633 | /imu/data_raw | sensor_msgs/msg/Imu | Imu(header=Header(stamp=Time(sec=1773683791, nanosec=328959792), frame_id=imu_link), orientation=Quaternion(x=0.0, y=0.0, z=0.0, w=0.0), orientation_covariance=[-1.0, 0.0, 0.0, 0.0, 0.0, 0.0, 0.0, 0.0, 0.0], angular_velocity=Vector3(x=-0.00390625, y=0.001953125, z=0.001953125), angular_velocity_covariance=[0.01, 0.0, 0.0, 0.0, 0.01, 0.0, 0.0, 0.0, 0.01], linear_acceleration=Vector3(x=-1.72265625, y=3.44921875, z=-9.1953125), linear_acceleration_covariance=[0.01, 0.0, 0.0, 0.0, 0.01, 0.0, 0.0, 0.0, 0.01])
1773683791425860841 | /imu/data_raw | sensor_msgs/msg/Imu | Imu(header=Header(stamp=Time(sec=1773683791, nanosec=424780015), frame_id=imu_link), orientation=Quaternion(x=0.0, y=0.0, z=0.0, w=0.0), orientation_covariance=[-1.0, 0.0, 0.0, 0.0, 0.0, 0.0, 0.0, 0.0, 0.0], angular_velocity=Vector3(x=0.001953125, y=0.0, z=-0.001953125), angular_velocity_covariance=[0.01, 0.0, 0.0, 0.0, 0.01, 0.0, 0.0, 0.0, 0.01], linear_acceleration=Vector3(x=-1.76171875, y=3.484375, z=-9.1953125), linear_acceleration_covariance=[0.01, 0.0, 0.0, 0.0, 0.01, 0.0, 0.0, 0.0, 0.01])
1773683791523804138 | /imu/data_raw | sensor_msgs/msg/Imu | Imu(header=Header(stamp=Time(sec=1773683791, nanosec=522719256), frame_id=imu_link), orientation=Quaternion(x=0.0, y=0.0, z=0.0, w=0.0), orientation_covariance=[-1.0, 0.0, 0.0, 0.0, 0.0, 0.0, 0.0, 0.0, 0.0], angular_velocity=Vector3(x=0.001953125, y=-0.001953125, z=-0.001953125), angular_velocity_covariance=[0.01, 0.0, 0.0, 0.0, 0.01, 0.0, 0.0, 0.0, 0.01], linear_acceleration=Vector3(x=-1.72265625, y=3.484375, z=-9.1953125), linear_acceleration_covariance=[0.01, 0.0, 0.0, 0.0, 0.01, 0.0, 0.0, 0.0, 0.01])
1773683791618711316 | /imu/data_raw | sensor_msgs/msg/Imu | Imu(header=Header(stamp=Time(sec=1773683791, nanosec=617755117), frame_id=imu_link), orientation=Quaternion(x=0.0, y=0.0, z=0.0, w=0.0), orientation_covariance=[-1.0, 0.0, 0.0, 0.0, 0.0, 0.0, 0.0, 0.0, 0.0], angular_velocity=Vector3(x=0.001953125, y=0.00390625, z=0.001953125), angular_velocity_covariance=[0.01, 0.0, 0.0, 0.0, 0.01, 0.0, 0.0, 0.0, 0.01], linear_acceleration=Vector3(x=-1.76171875, y=3.484375, z=-9.1953125), linear_acceleration_covariance=[0.01, 0.0, 0.0, 0.0, 0.01, 0.0, 0.0, 0.0, 0.01])
1773683791718827971 | /imu/data_raw | sensor_msgs/msg/Imu | Imu(header=Header(stamp=Time(sec=1773683791, nanosec=717721234), frame_id=imu_link), orientation=Quaternion(x=0.0, y=0.0, z=0.0, w=0.0), orientation_covariance=[-1.0, 0.0, 0.0, 0.0, 0.0, 0.0, 0.0, 0.0, 0.0], angular_velocity=Vector3(x=0.001953125, y=0.00390625, z=0.001953125), angular_velocity_covariance=[0.01, 0.0, 0.0, 0.0, 0.01, 0.0, 0.0, 0.0, 0.01], linear_acceleration=Vector3(x=-1.72265625, y=3.44921875, z=-9.1953125), linear_acceleration_covariance=[0.01, 0.0, 0.0, 0.0, 0.01, 0.0, 0.0, 0.0, 0.01])
1773683791827628874 | /imu/data_raw | sensor_msgs/msg/Imu | Imu(header=Header(stamp=Time(sec=1773683791, nanosec=826504338), frame_id=imu_link), orientation=Quaternion(x=0.0, y=0.0, z=0.0, w=0.0), orientation_covariance=[-1.0, 0.0, 0.0, 0.0, 0.0, 0.0, 0.0, 0.0, 0.0], angular_velocity=Vector3(x=0.001953125, y=0.00390625, z=0.001953125), angular_velocity_covariance=[0.01, 0.0, 0.0, 0.0, 0.01, 0.0, 0.0, 0.0, 0.01], linear_acceleration=Vector3(x=-1.76171875, y=3.484375, z=-9.1953125), linear_acceleration_covariance=[0.01, 0.0, 0.0, 0.0, 0.01, 0.0, 0.0, 0.0, 0.01])
1773683791924283409 | /imu/data_raw | sensor_msgs/msg/Imu | Imu(header=Header(stamp=Time(sec=1773683791, nanosec=923279185), frame_id=imu_link), orientation=Quaternion(x=0.0, y=0.0, z=0.0, w=0.0), orientation_covariance=[-1.0, 0.0, 0.0, 0.0, 0.0, 0.0, 0.0, 0.0, 0.0], angular_velocity=Vector3(x=0.0, y=0.0, z=0.0), angular_velocity_covariance=[0.01, 0.0, 0.0, 0.0, 0.01, 0.0, 0.0, 0.0, 0.01], linear_acceleration=Vector3(x=-1.72265625, y=3.44921875, z=-9.1953125), linear_acceleration_covariance=[0.01, 0.0, 0.0, 0.0, 0.01, 0.0, 0.0, 0.0, 0.01])
1773683792026119980 | /imu/data_raw | sensor_msgs/msg/Imu | Imu(header=Header(stamp=Time(sec=1773683792, nanosec=25048195), frame_id=imu_link), orientation=Quaternion(x=0.0, y=0.0, z=0.0, w=0.0), orientation_covariance=[-1.0, 0.0, 0.0, 0.0, 0.0, 0.0, 0.0, 0.0, 0.0], angular_velocity=Vector3(x=0.0, y=0.0, z=0.0), angular_velocity_covariance=[0.01, 0.0, 0.0, 0.0, 0.01, 0.0, 0.0, 0.0, 0.01], linear_acceleration=Vector3(x=-1.72265625, y=3.44921875, z=-9.1953125), linear_acceleration_covariance=[0.01, 0.0, 0.0, 0.0, 0.01, 0.0, 0.0, 0.0, 0.01])
1773683792127760135 | /imu/data_raw | sensor_msgs/msg/Imu | Imu(header=Header(stamp=Time(sec=1773683792, nanosec=126609710), frame_id=imu_link), orientation=Quaternion(x=0.0, y=0.0, z=0.0, w=0.0), orientation_covariance=[-1.0, 0.0, 0.0, 0.0, 0.0, 0.0, 0.0, 0.0, 0.0], angular_velocity=Vector3(x=0.0, y=0.0, z=0.0), angular_velocity_covariance=[0.01, 0.0, 0.0, 0.0, 0.01, 0.0, 0.0, 0.0, 0.01], linear_acceleration=Vector3(x=-1.72265625, y=3.44921875, z=-9.1953125), linear_acceleration_covariance=[0.01, 0.0, 0.0, 0.0, 0.01, 0.0, 0.0, 0.0, 0.01])
1773683792219757987 | /imu/data_raw | sensor_msgs/msg/Imu | Imu(header=Header(stamp=Time(sec=1773683792, nanosec=218764434), frame_id=imu_link), orientation=Quaternion(x=0.0, y=0.0, z=0.0, w=0.0), orientation_covariance=[-1.0, 0.0, 0.0, 0.0, 0.0, 0.0, 0.0, 0.0, 0.0], angular_velocity=Vector3(x=0.0, y=0.0, z=0.0), angular_velocity_covariance=[0.01, 0.0, 0.0, 0.0, 0.01, 0.0, 0.0, 0.0, 0.01], linear_acceleration=Vector3(x=-1.72265625, y=3.44921875, z=-9.1953125), linear_acceleration_covariance=[0.01, 0.0, 0.0, 0.0, 0.01, 0.0, 0.0, 0.0, 0.01])
1773683792318604545 | /imu/data_raw | sensor_msgs/msg/Imu | Imu(header=Header(stamp=Time(sec=1773683792, nanosec=317484403), frame_id=imu_link), orientation=Quaternion(x=0.0, y=0.0, z=0.0, w=0.0), orientation_covariance=[-1.0, 0.0, 0.0, 0.0, 0.0, 0.0, 0.0, 0.0, 0.0], angular_velocity=Vector3(x=0.0, y=0.0, z=0.0), angular_velocity_covariance=[0.01, 0.0, 0.0, 0.0, 0.01, 0.0, 0.0, 0.0, 0.01], linear_acceleration=Vector3(x=-1.72265625, y=3.44921875, z=-9.1953125), linear_acceleration_covariance=[0.01, 0.0, 0.0, 0.0, 0.01, 0.0, 0.0, 0.0, 0.01])
1773683792428305913 | /imu/data_raw | sensor_msgs/msg/Imu | Imu(header=Header(stamp=Time(sec=1773683792, nanosec=427197253), frame_id=imu_link), orientation=Quaternion(x=0.0, y=0.0, z=0.0, w=0.0), orientation_covariance=[-1.0, 0.0, 0.0, 0.0, 0.0, 0.0, 0.0, 0.0, 0.0], angular_velocity=Vector3(x=0.0, y=0.0, z=0.0), angular_velocity_covariance=[0.01, 0.0, 0.0, 0.0, 0.01, 0.0, 0.0, 0.0, 0.01], linear_acceleration=Vector3(x=-1.72265625, y=3.44921875, z=-9.1953125), linear_acceleration_covariance=[0.01, 0.0, 0.0, 0.0, 0.01, 0.0, 0.0, 0.0, 0.01])
1773683792526055683 | /imu/data_raw | sensor_msgs/msg/Imu | Imu(header=Header(stamp=Time(sec=1773683792, nanosec=524961377), frame_id=imu_link), orientation=Quaternion(x=0.0, y=0.0, z=0.0, w=0.0), orientation_covariance=[-1.0, 0.0, 0.0, 0.0, 0.0, 0.0, 0.0, 0.0, 0.0], angular_velocity=Vector3(x=0.0, y=0.0, z=0.0), angular_velocity_covariance=[0.01, 0.0, 0.0, 0.0, 0.01, 0.0, 0.0, 0.0, 0.01], linear_acceleration=Vector3(x=-1.72265625, y=3.44921875, z=-9.1953125), linear_acceleration_covariance=[0.01, 0.0, 0.0, 0.0, 0.01, 0.0, 0.0, 0.0, 0.01])
1773683792627065554 | /imu/data_raw | sensor_msgs/msg/Imu | Imu(header=Header(stamp=Time(sec=1773683792, nanosec=625990917), frame_id=imu_link), orientation=Quaternion(x=0.0, y=0.0, z=0.0, w=0.0), orientation_covariance=[-1.0, 0.0, 0.0, 0.0, 0.0, 0.0, 0.0, 0.0, 0.0], angular_velocity=Vector3(x=0.0, y=0.0, z=0.0), angular_velocity_covariance=[0.01, 0.0, 0.0, 0.0, 0.01, 0.0, 0.0, 0.0, 0.01], linear_acceleration=Vector3(x=-1.72265625, y=3.44921875, z=-9.1953125), linear_acceleration_covariance=[0.01, 0.0, 0.0, 0.0, 0.01, 0.0, 0.0, 0.0, 0.01])
1773683792726124844 | /imu/data_raw | sensor_msgs/msg/Imu | Imu(header=Header(stamp=Time(sec=1773683792, nanosec=725029704), frame_id=imu_link), orientation=Quaternion(x=0.0, y=0.0, z=0.0, w=0.0), orientation_covariance=[-1.0, 0.0, 0.0, 0.0, 0.0, 0.0, 0.0, 0.0, 0.0], angular_velocity=Vector3(x=0.0, y=0.0, z=0.0), angular_velocity_covariance=[0.01, 0.0, 0.0, 0.0, 0.01, 0.0, 0.0, 0.0, 0.01], linear_acceleration=Vector3(x=-1.76171875, y=3.44921875, z=-9.1953125), linear_acceleration_covariance=[0.01, 0.0, 0.0, 0.0, 0.01, 0.0, 0.0, 0.0, 0.01])
1773683792821279765 | /imu/data_raw | sensor_msgs/msg/Imu | Imu(header=Header(stamp=Time(sec=1773683792, nanosec=820171920), frame_id=imu_link), orientation=Quaternion(x=0.0, y=0.0, z=0.0, w=0.0), orientation_covariance=[-1.0, 0.0, 0.0, 0.0, 0.0, 0.0, 0.0, 0.0, 0.0], angular_velocity=Vector3(x=0.0, y=0.0, z=0.0), angular_velocity_covariance=[0.01, 0.0, 0.0, 0.0, 0.01, 0.0, 0.0, 0.0, 0.01], linear_acceleration=Vector3(x=-1.72265625, y=3.44921875, z=-9.1953125), linear_acceleration_covariance=[0.01, 0.0, 0.0, 0.0, 0.01, 0.0, 0.0, 0.0, 0.01])
1773683792930514388 | /imu/data_raw | sensor_msgs/msg/Imu | Imu(header=Header(stamp=Time(sec=1773683792, nanosec=929339738), frame_id=imu_link), orientation=Quaternion(x=0.0, y=0.0, z=0.0, w=0.0), orientation_covariance=[-1.0, 0.0, 0.0, 0.0, 0.0, 0.0, 0.0, 0.0, 0.0], angular_velocity=Vector3(x=0.0, y=0.0, z=0.0), angular_velocity_covariance=[0.01, 0.0, 0.0, 0.0, 0.01, 0.0, 0.0, 0.0, 0.01], linear_acceleration=Vector3(x=-1.72265625, y=3.44921875, z=-9.1953125), linear_acceleration_covariance=[0.01, 0.0, 0.0, 0.0, 0.01, 0.0, 0.0, 0.0, 0.01])
1773683793011373971 | /imu/data_raw | sensor_msgs/msg/Imu | Imu(header=Header(stamp=Time(sec=1773683793, nanosec=10274390), frame_id=imu_link), orientation=Quaternion(x=0.0, y=0.0, z=0.0, w=0.0), orientation_covariance=[-1.0, 0.0, 0.0, 0.0, 0.0, 0.0, 0.0, 0.0, 0.0], angular_velocity=Vector3(x=0.0, y=0.0, z=0.0), angular_velocity_covariance=[0.01, 0.0, 0.0, 0.0, 0.01, 0.0, 0.0, 0.0, 0.01], linear_acceleration=Vector3(x=-1.72265625, y=3.44921875, z=-9.1953125), linear_acceleration_covariance=[0.01, 0.0, 0.0, 0.0, 0.01, 0.0, 0.0, 0.0, 0.01])
1773683793125537269 | /imu/data_raw | sensor_msgs/msg/Imu | Imu(header=Header(stamp=Time(sec=1773683793, nanosec=124537256), frame_id=imu_link), orientation=Quaternion(x=0.0, y=0.0, z=0.0, w=0.0), orientation_covariance=[-1.0, 0.0, 0.0, 0.0, 0.0, 0.0, 0.0, 0.0, 0.0], angular_velocity=Vector3(x=0.00390625, y=-0.009765625, z=-0.00390625), angular_velocity_covariance=[0.01, 0.0, 0.0, 0.0, 0.01, 0.0, 0.0, 0.0, 0.01], linear_acceleration=Vector3(x=-1.76171875, y=3.44921875, z=-9.1953125), linear_acceleration_covariance=[0.01, 0.0, 0.0, 0.0, 0.01, 0.0, 0.0, 0.0, 0.01])
1773683793227739287 | /imu/data_raw | sensor_msgs/msg/Imu | Imu(header=Header(stamp=Time(sec=1773683793, nanosec=226600127), frame_id=imu_link), orientation=Quaternion(x=0.0, y=0.0, z=0.0, w=0.0), orientation_covariance=[-1.0, 0.0, 0.0, 0.0, 0.0, 0.0, 0.0, 0.0, 0.0], angular_velocity=Vector3(x=0.00390625, y=-0.005859375, z=-0.001953125), angular_velocity_covariance=[0.01, 0.0, 0.0, 0.0, 0.01, 0.0, 0.0, 0.0, 0.01], linear_acceleration=Vector3(x=-1.72265625, y=3.44921875, z=-9.1953125), linear_acceleration_covariance=[0.01, 0.0, 0.0, 0.0, 0.01, 0.0, 0.0, 0.0, 0.01])
1773683793335280856 | /imu/data_raw | sensor_msgs/msg/Imu | Imu(header=Header(stamp=Time(sec=1773683793, nanosec=334157569), frame_id=imu_link), orientation=Quaternion(x=0.0, y=0.0, z=0.0, w=0.0), orientation_covariance=[-1.0, 0.0, 0.0, 0.0, 0.0, 0.0, 0.0, 0.0, 0.0], angular_velocity=Vector3(x=-0.00390625, y=0.0, z=0.001953125), angular_velocity_covariance=[0.01, 0.0, 0.0, 0.0, 0.01, 0.0, 0.0, 0.0, 0.01], linear_acceleration=Vector3(x=-1.72265625, y=3.44921875, z=-9.1953125), linear_acceleration_covariance=[0.01, 0.0, 0.0, 0.0, 0.01, 0.0, 0.0, 0.0, 0.01])
1773683793420032449 | /imu/data_raw | sensor_msgs/msg/Imu | Imu(header=Header(stamp=Time(sec=1773683793, nanosec=418791406), frame_id=imu_link), orientation=Quaternion(x=0.0, y=0.0, z=0.0, w=0.0), orientation_covariance=[-1.0, 0.0, 0.0, 0.0, 0.0, 0.0, 0.0, 0.0, 0.0], angular_velocity=Vector3(x=0.0, y=0.00390625, z=0.0), angular_velocity_covariance=[0.01, 0.0, 0.0, 0.0, 0.01, 0.0, 0.0, 0.0, 0.01], linear_acceleration=Vector3(x=-1.76171875, y=3.484375, z=-9.1953125), linear_acceleration_covariance=[0.01, 0.0, 0.0, 0.0, 0.01, 0.0, 0.0, 0.0, 0.01])
1773683793528735310 | /imu/data_raw | sensor_msgs/msg/Imu | Imu(header=Header(stamp=Time(sec=1773683793, nanosec=527664029), frame_id=imu_link), orientation=Quaternion(x=0.0, y=0.0, z=0.0, w=0.0), orientation_covariance=[-1.0, 0.0, 0.0, 0.0, 0.0, 0.0, 0.0, 0.0, 0.0], angular_velocity=Vector3(x=-0.001953125, y=0.0, z=0.001953125), angular_velocity_covariance=[0.01, 0.0, 0.0, 0.0, 0.01, 0.0, 0.0, 0.0, 0.01], linear_acceleration=Vector3(x=-1.72265625, y=3.44921875, z=-9.1953125), linear_acceleration_covariance=[0.01, 0.0, 0.0, 0.0, 0.01, 0.0, 0.0, 0.0, 0.01])
1773683793627108612 | /imu/data_raw | sensor_msgs/msg/Imu | Imu(header=Header(stamp=Time(sec=1773683793, nanosec=626122786), frame_id=imu_link), orientation=Quaternion(x=0.0, y=0.0, z=0.0, w=0.0), orientation_covariance=[-1.0, 0.0, 0.0, 0.0, 0.0, 0.0, 0.0, 0.0, 0.0], angular_velocity=Vector3(x=0.00390625, y=-0.00390625, z=0.001953125), angular_velocity_covariance=[0.01, 0.0, 0.0, 0.0, 0.01, 0.0, 0.0, 0.0, 0.01], linear_acceleration=Vector3(x=-1.72265625, y=3.44921875, z=-9.1953125), linear_acceleration_covariance=[0.01, 0.0, 0.0, 0.0, 0.01, 0.0, 0.0, 0.0, 0.01])
1773683793726540248 | /imu/data_raw | sensor_msgs/msg/Imu | Imu(header=Header(stamp=Time(sec=1773683793, nanosec=725556775), frame_id=imu_link), orientation=Quaternion(x=0.0, y=0.0, z=0.0, w=0.0), orientation_covariance=[-1.0, 0.0, 0.0, 0.0, 0.0, 0.0, 0.0, 0.0, 0.0], angular_velocity=Vector3(x=-0.001953125, y=0.00390625, z=0.0), angular_velocity_covariance=[0.01, 0.0, 0.0, 0.0, 0.01, 0.0, 0.0, 0.0, 0.01], linear_acceleration=Vector3(x=-1.72265625, y=3.44921875, z=-9.1953125), linear_acceleration_covariance=[0.01, 0.0, 0.0, 0.0, 0.01, 0.0, 0.0, 0.0, 0.01])
1773683793828396334 | /imu/data_raw | sensor_msgs/msg/Imu | Imu(header=Header(stamp=Time(sec=1773683793, nanosec=827385172), frame_id=imu_link), orientation=Quaternion(x=0.0, y=0.0, z=0.0, w=0.0), orientation_covariance=[-1.0, 0.0, 0.0, 0.0, 0.0, 0.0, 0.0, 0.0, 0.0], angular_velocity=Vector3(x=0.001953125, y=0.0, z=0.0), angular_velocity_covariance=[0.01, 0.0, 0.0, 0.0, 0.01, 0.0, 0.0, 0.0, 0.01], linear_acceleration=Vector3(x=-1.72265625, y=3.44921875, z=-9.16015625), linear_acceleration_covariance=[0.01, 0.0, 0.0, 0.0, 0.01, 0.0, 0.0, 0.0, 0.01])
1773683793921868657 | /imu/data_raw | sensor_msgs/msg/Imu | Imu(header=Header(stamp=Time(sec=1773683793, nanosec=920769743), frame_id=imu_link), orientation=Quaternion(x=0.0, y=0.0, z=0.0, w=0.0), orientation_covariance=[-1.0, 0.0, 0.0, 0.0, 0.0, 0.0, 0.0, 0.0, 0.0], angular_velocity=Vector3(x=-0.001953125, y=-0.00390625, z=-0.005859375), angular_velocity_covariance=[0.01, 0.0, 0.0, 0.0, 0.01, 0.0, 0.0, 0.0, 0.01], linear_acceleration=Vector3(x=-1.72265625, y=3.44921875, z=-9.1953125), linear_acceleration_covariance=[0.01, 0.0, 0.0, 0.0, 0.01, 0.0, 0.0, 0.0, 0.01])
1773683794030115259 | /imu/data_raw | sensor_msgs/msg/Imu | Imu(header=Header(stamp=Time(sec=1773683794, nanosec=29124084), frame_id=imu_link), orientation=Quaternion(x=0.0, y=0.0, z=0.0, w=0.0), orientation_covariance=[-1.0, 0.0, 0.0, 0.0, 0.0, 0.0, 0.0, 0.0, 0.0], angular_velocity=Vector3(x=0.001953125, y=-0.001953125, z=-0.001953125), angular_velocity_covariance=[0.01, 0.0, 0.0, 0.0, 0.01, 0.0, 0.0, 0.0, 0.01], linear_acceleration=Vector3(x=-1.72265625, y=3.484375, z=-9.1953125), linear_acceleration_covariance=[0.01, 0.0, 0.0, 0.0, 0.01, 0.0, 0.0, 0.0, 0.01])
1773683794109961061 | /imu/data_raw | sensor_msgs/msg/Imu | Imu(header=Header(stamp=Time(sec=1773683794, nanosec=108669553), frame_id=imu_link), orientation=Quaternion(x=0.0, y=0.0, z=0.0, w=0.0), orientation_covariance=[-1.0, 0.0, 0.0, 0.0, 0.0, 0.0, 0.0, 0.0, 0.0], angular_velocity=Vector3(x=-0.00390625, y=-0.001953125, z=0.0), angular_velocity_covariance=[0.01, 0.0, 0.0, 0.0, 0.01, 0.0, 0.0, 0.0, 0.01], linear_acceleration=Vector3(x=-1.76171875, y=3.44921875, z=-9.1953125), linear_acceleration_covariance=[0.01, 0.0, 0.0, 0.0, 0.01, 0.0, 0.0, 0.0, 0.01])
1773683794229816144 | /imu/data_raw | sensor_msgs/msg/Imu | Imu(header=Header(stamp=Time(sec=1773683794, nanosec=228812170), frame_id=imu_link), orientation=Quaternion(x=0.0, y=0.0, z=0.0, w=0.0), orientation_covariance=[-1.0, 0.0, 0.0, 0.0, 0.0, 0.0, 0.0, 0.0, 0.0], angular_velocity=Vector3(x=0.0, y=0.0, z=0.0), angular_velocity_covariance=[0.01, 0.0, 0.0, 0.0, 0.01, 0.0, 0.0, 0.0, 0.01], linear_acceleration=Vector3(x=-1.72265625, y=3.484375, z=-9.1953125), linear_acceleration_covariance=[0.01, 0.0, 0.0, 0.0, 0.01, 0.0, 0.0, 0.0, 0.01])
1773683794328961426 | /imu/data_raw | sensor_msgs/msg/Imu | Imu(header=Header(stamp=Time(sec=1773683794, nanosec=327810195), frame_id=imu_link), orientation=Quaternion(x=0.0, y=0.0, z=0.0, w=0.0), orientation_covariance=[-1.0, 0.0, 0.0, 0.0, 0.0, 0.0, 0.0, 0.0, 0.0], angular_velocity=Vector3(x=0.0, y=0.0, z=0.0), angular_velocity_covariance=[0.01, 0.0, 0.0, 0.0, 0.01, 0.0, 0.0, 0.0, 0.01], linear_acceleration=Vector3(x=-1.72265625, y=3.44921875, z=-9.1953125), linear_acceleration_covariance=[0.01, 0.0, 0.0, 0.0, 0.01, 0.0, 0.0, 0.0, 0.01])
1773683794427634152 | /imu/data_raw | sensor_msgs/msg/Imu | Imu(header=Header(stamp=Time(sec=1773683794, nanosec=426457306), frame_id=imu_link), orientation=Quaternion(x=0.0, y=0.0, z=0.0, w=0.0), orientation_covariance=[-1.0, 0.0, 0.0, 0.0, 0.0, 0.0, 0.0, 0.0, 0.0], angular_velocity=Vector3(x=0.0, y=0.0, z=0.0), angular_velocity_covariance=[0.01, 0.0, 0.0, 0.0, 0.01, 0.0, 0.0, 0.0, 0.01], linear_acceleration=Vector3(x=-1.76171875, y=3.44921875, z=-9.1953125), linear_acceleration_covariance=[0.01, 0.0, 0.0, 0.0, 0.01, 0.0, 0.0, 0.0, 0.01])
1773683794521704506 | /imu/data_raw | sensor_msgs/msg/Imu | Imu(header=Header(stamp=Time(sec=1773683794, nanosec=520594094), frame_id=imu_link), orientation=Quaternion(x=0.0, y=0.0, z=0.0, w=0.0), orientation_covariance=[-1.0, 0.0, 0.0, 0.0, 0.0, 0.0, 0.0, 0.0, 0.0], angular_velocity=Vector3(x=0.0, y=0.0, z=0.0), angular_velocity_covariance=[0.01, 0.0, 0.0, 0.0, 0.01, 0.0, 0.0, 0.0, 0.01], linear_acceleration=Vector3(x=-1.76171875, y=3.44921875, z=-9.1953125), linear_acceleration_covariance=[0.01, 0.0, 0.0, 0.0, 0.01, 0.0, 0.0, 0.0, 0.01])
1773683794630141042 | /imu/data_raw | sensor_msgs/msg/Imu | Imu(header=Header(stamp=Time(sec=1773683794, nanosec=629030260), frame_id=imu_link), orientation=Quaternion(x=0.0, y=0.0, z=0.0, w=0.0), orientation_covariance=[-1.0, 0.0, 0.0, 0.0, 0.0, 0.0, 0.0, 0.0, 0.0], angular_velocity=Vector3(x=-0.001953125, y=-0.001953125, z=0.0), angular_velocity_covariance=[0.01, 0.0, 0.0, 0.0, 0.01, 0.0, 0.0, 0.0, 0.01], linear_acceleration=Vector3(x=-1.72265625, y=3.44921875, z=-9.1953125), linear_acceleration_covariance=[0.01, 0.0, 0.0, 0.0, 0.01, 0.0, 0.0, 0.0, 0.01])
1773683794711692383 | /imu/data_raw | sensor_msgs/msg/Imu | Imu(header=Header(stamp=Time(sec=1773683794, nanosec=710572563), frame_id=imu_link), orientation=Quaternion(x=0.0, y=0.0, z=0.0, w=0.0), orientation_covariance=[-1.0, 0.0, 0.0, 0.0, 0.0, 0.0, 0.0, 0.0, 0.0], angular_velocity=Vector3(x=-0.001953125, y=0.00390625, z=0.001953125), angular_velocity_covariance=[0.01, 0.0, 0.0, 0.0, 0.01, 0.0, 0.0, 0.0, 0.01], linear_acceleration=Vector3(x=-1.72265625, y=3.44921875, z=-9.1953125), linear_acceleration_covariance=[0.01, 0.0, 0.0, 0.0, 0.01, 0.0, 0.0, 0.0, 0.01])
1773683794832493877 | /imu/data_raw | sensor_msgs/msg/Imu | Imu(header=Header(stamp=Time(sec=1773683794, nanosec=831341793), frame_id=imu_link), orientation=Quaternion(x=0.0, y=0.0, z=0.0, w=0.0), orientation_covariance=[-1.0, 0.0, 0.0, 0.0, 0.0, 0.0, 0.0, 0.0, 0.0], angular_velocity=Vector3(x=0.0, y=-0.00390625, z=0.0), angular_velocity_covariance=[0.01, 0.0, 0.0, 0.0, 0.01, 0.0, 0.0, 0.0, 0.01], linear_acceleration=Vector3(x=-1.72265625, y=3.44921875, z=-9.1953125), linear_acceleration_covariance=[0.01, 0.0, 0.0, 0.0, 0.01, 0.0, 0.0, 0.0, 0.01])
1773683794929440486 | /imu/data_raw | sensor_msgs/msg/Imu | Imu(header=Header(stamp=Time(sec=1773683794, nanosec=928292125), frame_id=imu_link), orientation=Quaternion(x=0.0, y=0.0, z=0.0, w=0.0), orientation_covariance=[-1.0, 0.0, 0.0, 0.0, 0.0, 0.0, 0.0, 0.0, 0.0], angular_velocity=Vector3(x=0.001953125, y=-0.005859375, z=-0.001953125), angular_velocity_covariance=[0.01, 0.0, 0.0, 0.0, 0.01, 0.0, 0.0, 0.0, 0.01], linear_acceleration=Vector3(x=-1.72265625, y=3.484375, z=-9.1953125), linear_acceleration_covariance=[0.01, 0.0, 0.0, 0.0, 0.01, 0.0, 0.0, 0.0, 0.01])
1773683795036588405 | /imu/data_raw | sensor_msgs/msg/Imu | Imu(header=Header(stamp=Time(sec=1773683795, nanosec=35468644), frame_id=imu_link), orientation=Quaternion(x=0.0, y=0.0, z=0.0, w=0.0), orientation_covariance=[-1.0, 0.0, 0.0, 0.0, 0.0, 0.0, 0.0, 0.0, 0.0], angular_velocity=Vector3(x=0.0, y=-0.001953125, z=0.001953125), angular_velocity_covariance=[0.01, 0.0, 0.0, 0.0, 0.01, 0.0, 0.0, 0.0, 0.01], linear_acceleration=Vector3(x=-1.76171875, y=3.484375, z=-9.1953125), linear_acceleration_covariance=[0.01, 0.0, 0.0, 0.0, 0.01, 0.0, 0.0, 0.0, 0.01])
1773683799958289014 | /imu/data_raw | sensor_msgs/msg/Imu | Imu(header=Header(stamp=Time(sec=1773683799, nanosec=957026361), frame_id=imu_link), orientation=Quaternion(x=0.0, y=0.0, z=0.0, w=0.0), orientation_covariance=[-1.0, 0.0, 0.0, 0.0, 0.0, 0.0, 0.0, 0.0, 0.0], angular_velocity=Vector3(x=-0.00390625, y=-0.03515625, z=-0.021484375), angular_velocity_covariance=[0.01, 0.0, 0.0, 0.0, 0.01, 0.0, 0.0, 0.0, 0.01], linear_acceleration=Vector3(x=126.58203125, y=3.33203125, z=-9.42578125), linear_acceleration_covariance=[0.01, 0.0, 0.0, 0.0, 0.01, 0.0, 0.0, 0.0, 0.01])
1773683800019719938 | /imu/data_raw | sensor_msgs/msg/Imu | Imu(header=Header(stamp=Time(sec=1773683800, nanosec=18766710), frame_id=imu_link), orientation=Quaternion(x=0.0, y=0.0, z=0.0, w=0.0), orientation_covariance=[-1.0, 0.0, 0.0, 0.0, 0.0, 0.0, 0.0, 0.0, 0.0], angular_velocity=Vector3(x=0.0, y=0.015625, z=0.0078125), angular_velocity_covariance=[0.01, 0.0, 0.0, 0.0, 0.01, 0.0, 0.0, 0.0, 0.01], linear_acceleration=Vector3(x=-1.5703125, y=3.37109375, z=-9.26953125), linear_acceleration_covariance=[0.01, 0.0, 0.0, 0.0, 0.01, 0.0, 0.0, 0.0, 0.01])
1773683800128181456 | /imu/data_raw | sensor_msgs/msg/Imu | Imu(header=Header(stamp=Time(sec=1773683800, nanosec=127051487), frame_id=imu_link), orientation=Quaternion(x=0.0, y=0.0, z=0.0, w=0.0), orientation_covariance=[-1.0, 0.0, 0.0, 0.0, 0.0, 0.0, 0.0, 0.0, 0.0], angular_velocity=Vector3(x=-0.001953125, y=0.0078125, z=0.00390625), angular_velocity_covariance=[0.01, 0.0, 0.0, 0.0, 0.01, 0.0, 0.0, 0.0, 0.01], linear_acceleration=Vector3(x=-1.5703125, y=3.33203125, z=-9.26953125), linear_acceleration_covariance=[0.01, 0.0, 0.0, 0.0, 0.01, 0.0, 0.0, 0.0, 0.01])
1773683800231372891 | /imu/data_raw | sensor_msgs/msg/Imu | Imu(header=Header(stamp=Time(sec=1773683800, nanosec=230354174), frame_id=imu_link), orientation=Quaternion(x=0.0, y=0.0, z=0.0, w=0.0), orientation_covariance=[-1.0, 0.0, 0.0, 0.0, 0.0, 0.0, 0.0, 0.0, 0.0], angular_velocity=Vector3(x=0.00390625, y=-0.001953125, z=0.001953125), angular_velocity_covariance=[0.01, 0.0, 0.0, 0.0, 0.01, 0.0, 0.0, 0.0, 0.01], linear_acceleration=Vector3(x=-1.5703125, y=3.37109375, z=-9.26953125), linear_acceleration_covariance=[0.01, 0.0, 0.0, 0.0, 0.01, 0.0, 0.0, 0.0, 0.01])
1773683800324970628 | /imu/data_raw | sensor_msgs/msg/Imu | Imu(header=Header(stamp=Time(sec=1773683800, nanosec=323957467), frame_id=imu_link), orientation=Quaternion(x=0.0, y=0.0, z=0.0, w=0.0), orientation_covariance=[-1.0, 0.0, 0.0, 0.0, 0.0, 0.0, 0.0, 0.0, 0.0], angular_velocity=Vector3(x=-0.001953125, y=0.001953125, z=0.001953125), angular_velocity_covariance=[0.01, 0.0, 0.0, 0.0, 0.01, 0.0, 0.0, 0.0, 0.01], linear_acceleration=Vector3(x=-1.5703125, y=3.33203125, z=-9.26953125), linear_acceleration_covariance=[0.01, 0.0, 0.0, 0.0, 0.01, 0.0, 0.0, 0.0, 0.01])
1773683800424962046 | /imu/data_raw | sensor_msgs/msg/Imu | Imu(header=Header(stamp=Time(sec=1773683800, nanosec=423894565), frame_id=imu_link), orientation=Quaternion(x=0.0, y=0.0, z=0.0, w=0.0), orientation_covariance=[-1.0, 0.0, 0.0, 0.0, 0.0, 0.0, 0.0, 0.0, 0.0], angular_velocity=Vector3(x=0.001953125, y=0.0, z=0.0), angular_velocity_covariance=[0.01, 0.0, 0.0, 0.0, 0.01, 0.0, 0.0, 0.0, 0.01], linear_acceleration=Vector3(x=-1.5703125, y=3.33203125, z=-9.26953125), linear_acceleration_covariance=[0.01, 0.0, 0.0, 0.0, 0.01, 0.0, 0.0, 0.0, 0.01])
1773683800525644498 | /imu/data_raw | sensor_msgs/msg/Imu | Imu(header=Header(stamp=Time(sec=1773683800, nanosec=524614669), frame_id=imu_link), orientation=Quaternion(x=0.0, y=0.0, z=0.0, w=0.0), orientation_covariance=[-1.0, 0.0, 0.0, 0.0, 0.0, 0.0, 0.0, 0.0, 0.0], angular_velocity=Vector3(x=0.00390625, y=0.009765625, z=0.005859375), angular_velocity_covariance=[0.01, 0.0, 0.0, 0.0, 0.01, 0.0, 0.0, 0.0, 0.01], linear_acceleration=Vector3(x=-1.5703125, y=3.37109375, z=-9.26953125), linear_acceleration_covariance=[0.01, 0.0, 0.0, 0.0, 0.01, 0.0, 0.0, 0.0, 0.01])
1773683800625671531 | /imu/data_raw | sensor_msgs/msg/Imu | Imu(header=Header(stamp=Time(sec=1773683800, nanosec=624734360), frame_id=imu_link), orientation=Quaternion(x=0.0, y=0.0, z=0.0, w=0.0), orientation_covariance=[-1.0, 0.0, 0.0, 0.0, 0.0, 0.0, 0.0, 0.0, 0.0], angular_velocity=Vector3(x=0.001953125, y=-0.01171875, z=-0.005859375), angular_velocity_covariance=[0.01, 0.0, 0.0, 0.0, 0.01, 0.0, 0.0, 0.0, 0.01], linear_acceleration=Vector3(x=-1.5703125, y=3.33203125, z=-9.26953125), linear_acceleration_covariance=[0.01, 0.0, 0.0, 0.0, 0.01, 0.0, 0.0, 0.0, 0.01])
1773683800726831089 | /imu/data_raw | sensor_msgs/msg/Imu | Imu(header=Header(stamp=Time(sec=1773683800, nanosec=725706509), frame_id=imu_link), orientation=Quaternion(x=0.0, y=0.0, z=0.0, w=0.0), orientation_covariance=[-1.0, 0.0, 0.0, 0.0, 0.0, 0.0, 0.0, 0.0, 0.0], angular_velocity=Vector3(x=-0.001953125, y=0.00390625, z=0.00390625), angular_velocity_covariance=[0.01, 0.0, 0.0, 0.0, 0.01, 0.0, 0.0, 0.0, 0.01], linear_acceleration=Vector3(x=-1.5703125, y=3.37109375, z=-9.26953125), linear_acceleration_covariance=[0.01, 0.0, 0.0, 0.0, 0.01, 0.0, 0.0, 0.0, 0.01])
1773683800829579274 | /imu/data_raw | sensor_msgs/msg/Imu | Imu(header=Header(stamp=Time(sec=1773683800, nanosec=828530962), frame_id=imu_link), orientation=Quaternion(x=0.0, y=0.0, z=0.0, w=0.0), orientation_covariance=[-1.0, 0.0, 0.0, 0.0, 0.0, 0.0, 0.0, 0.0, 0.0], angular_velocity=Vector3(x=0.001953125, y=0.009765625, z=0.005859375), angular_velocity_covariance=[0.01, 0.0, 0.0, 0.0, 0.01, 0.0, 0.0, 0.0, 0.01], linear_acceleration=Vector3(x=-1.5703125, y=3.37109375, z=-9.26953125), linear_acceleration_covariance=[0.01, 0.0, 0.0, 0.0, 0.01, 0.0, 0.0, 0.0, 0.01])
1773683800911102537 | /imu/data_raw | sensor_msgs/msg/Imu | Imu(header=Header(stamp=Time(sec=1773683800, nanosec=909970661), frame_id=imu_link), orientation=Quaternion(x=0.0, y=0.0, z=0.0, w=0.0), orientation_covariance=[-1.0, 0.0, 0.0, 0.0, 0.0, 0.0, 0.0, 0.0, 0.0], angular_velocity=Vector3(x=0.001953125, y=0.005859375, z=0.00390625), angular_velocity_covariance=[0.01, 0.0, 0.0, 0.0, 0.01, 0.0, 0.0, 0.0, 0.01], linear_acceleration=Vector3(x=-1.5703125, y=3.37109375, z=-9.26953125), linear_acceleration_covariance=[0.01, 0.0, 0.0, 0.0, 0.01, 0.0, 0.0, 0.0, 0.01])
1773683801031067447 | /imu/data_raw | sensor_msgs/msg/Imu | Imu(header=Header(stamp=Time(sec=1773683801, nanosec=30018563), frame_id=imu_link), orientation=Quaternion(x=0.0, y=0.0, z=0.0, w=0.0), orientation_covariance=[-1.0, 0.0, 0.0, 0.0, 0.0, 0.0, 0.0, 0.0, 0.0], angular_velocity=Vector3(x=-0.001953125, y=0.00390625, z=0.00390625), angular_velocity_covariance=[0.01, 0.0, 0.0, 0.0, 0.01, 0.0, 0.0, 0.0, 0.01], linear_acceleration=Vector3(x=-1.5703125, y=3.37109375, z=-9.26953125), linear_acceleration_covariance=[0.01, 0.0, 0.0, 0.0, 0.01, 0.0, 0.0, 0.0, 0.01])
1773683801127169567 | /imu/data_raw | sensor_msgs/msg/Imu | Imu(header=Header(stamp=Time(sec=1773683801, nanosec=126048917), frame_id=imu_link), orientation=Quaternion(x=0.0, y=0.0, z=0.0, w=0.0), orientation_covariance=[-1.0, 0.0, 0.0, 0.0, 0.0, 0.0, 0.0, 0.0, 0.0], angular_velocity=Vector3(x=0.0, y=-0.005859375, z=-0.0078125), angular_velocity_covariance=[0.01, 0.0, 0.0, 0.0, 0.01, 0.0, 0.0, 0.0, 0.01], linear_acceleration=Vector3(x=-1.5703125, y=3.37109375, z=-9.26953125), linear_acceleration_covariance=[0.01, 0.0, 0.0, 0.0, 0.01, 0.0, 0.0, 0.0, 0.01])
1773683801227019010 | /imu/data_raw | sensor_msgs/msg/Imu | Imu(header=Header(stamp=Time(sec=1773683801, nanosec=226002889), frame_id=imu_link), orientation=Quaternion(x=0.0, y=0.0, z=0.0, w=0.0), orientation_covariance=[-1.0, 0.0, 0.0, 0.0, 0.0, 0.0, 0.0, 0.0, 0.0], angular_velocity=Vector3(x=0.001953125, y=0.005859375, z=0.005859375), angular_velocity_covariance=[0.01, 0.0, 0.0, 0.0, 0.01, 0.0, 0.0, 0.0, 0.01], linear_acceleration=Vector3(x=-1.5703125, y=3.37109375, z=-9.26953125), linear_acceleration_covariance=[0.01, 0.0, 0.0, 0.0, 0.01, 0.0, 0.0, 0.0, 0.01])
1773683801320710830 | /imu/data_raw | sensor_msgs/msg/Imu | Imu(header=Header(stamp=Time(sec=1773683801, nanosec=319607145), frame_id=imu_link), orientation=Quaternion(x=0.0, y=0.0, z=0.0, w=0.0), orientation_covariance=[-1.0, 0.0, 0.0, 0.0, 0.0, 0.0, 0.0, 0.0, 0.0], angular_velocity=Vector3(x=0.0, y=-0.01953125, z=-0.013671875), angular_velocity_covariance=[0.01, 0.0, 0.0, 0.0, 0.01, 0.0, 0.0, 0.0, 0.01], linear_acceleration=Vector3(x=-1.5703125, y=3.33203125, z=-9.26953125), linear_acceleration_covariance=[0.01, 0.0, 0.0, 0.0, 0.01, 0.0, 0.0, 0.0, 0.01])
1773683801412240821 | /imu/data_raw | sensor_msgs/msg/Imu | Imu(header=Header(stamp=Time(sec=1773683801, nanosec=411009123), frame_id=imu_link), orientation=Quaternion(x=0.0, y=0.0, z=0.0, w=0.0), orientation_covariance=[-1.0, 0.0, 0.0, 0.0, 0.0, 0.0, 0.0, 0.0, 0.0], angular_velocity=Vector3(x=0.001953125, y=0.00390625, z=0.001953125), angular_velocity_covariance=[0.01, 0.0, 0.0, 0.0, 0.01, 0.0, 0.0, 0.0, 0.01], linear_acceleration=Vector3(x=-1.5703125, y=3.37109375, z=-9.26953125), linear_acceleration_covariance=[0.01, 0.0, 0.0, 0.0, 0.01, 0.0, 0.0, 0.0, 0.01])
1773683801530049931 | /imu/data_raw | sensor_msgs/msg/Imu | Imu(header=Header(stamp=Time(sec=1773683801, nanosec=528936226), frame_id=imu_link), orientation=Quaternion(x=0.0, y=0.0, z=0.0, w=0.0), orientation_covariance=[-1.0, 0.0, 0.0, 0.0, 0.0, 0.0, 0.0, 0.0, 0.0], angular_velocity=Vector3(x=0.005859375, y=0.015625, z=0.013671875), angular_velocity_covariance=[0.01, 0.0, 0.0, 0.0, 0.01, 0.0, 0.0, 0.0, 0.01], linear_acceleration=Vector3(x=-1.5703125, y=3.37109375, z=-9.26953125), linear_acceleration_covariance=[0.01, 0.0, 0.0, 0.0, 0.01, 0.0, 0.0, 0.0, 0.01])
1773683801628400130 | /imu/data_raw | sensor_msgs/msg/Imu | Imu(header=Header(stamp=Time(sec=1773683801, nanosec=627258051), frame_id=imu_link), orientation=Quaternion(x=0.0, y=0.0, z=0.0, w=0.0), orientation_covariance=[-1.0, 0.0, 0.0, 0.0, 0.0, 0.0, 0.0, 0.0, 0.0], angular_velocity=Vector3(x=0.005859375, y=0.01171875, z=0.0078125), angular_velocity_covariance=[0.01, 0.0, 0.0, 0.0, 0.01, 0.0, 0.0, 0.0, 0.01], linear_acceleration=Vector3(x=-1.5703125, y=3.37109375, z=-9.26953125), linear_acceleration_covariance=[0.01, 0.0, 0.0, 0.0, 0.01, 0.0, 0.0, 0.0, 0.01])
1773683801727948987 | /imu/data_raw | sensor_msgs/msg/Imu | Imu(header=Header(stamp=Time(sec=1773683801, nanosec=726944126), frame_id=imu_link), orientation=Quaternion(x=0.0, y=0.0, z=0.0, w=0.0), orientation_covariance=[-1.0, 0.0, 0.0, 0.0, 0.0, 0.0, 0.0, 0.0, 0.0], angular_velocity=Vector3(x=-0.0078125, y=-0.025390625, z=-0.01953125), angular_velocity_covariance=[0.01, 0.0, 0.0, 0.0, 0.01, 0.0, 0.0, 0.0, 0.01], linear_acceleration=Vector3(x=-1.5703125, y=3.33203125, z=-9.26953125), linear_acceleration_covariance=[0.01, 0.0, 0.0, 0.0, 0.01, 0.0, 0.0, 0.0, 0.01])
1773683801827255004 | /imu/data_raw | sensor_msgs/msg/Imu | Imu(header=Header(stamp=Time(sec=1773683801, nanosec=826105258), frame_id=imu_link), orientation=Quaternion(x=0.0, y=0.0, z=0.0, w=0.0), orientation_covariance=[-1.0, 0.0, 0.0, 0.0, 0.0, 0.0, 0.0, 0.0, 0.0], angular_velocity=Vector3(x=0.001953125, y=0.0, z=0.001953125), angular_velocity_covariance=[0.01, 0.0, 0.0, 0.0, 0.01, 0.0, 0.0, 0.0, 0.01], linear_acceleration=Vector3(x=-1.5703125, y=3.33203125, z=-9.26953125), linear_acceleration_covariance=[0.01, 0.0, 0.0, 0.0, 0.01, 0.0, 0.0, 0.0, 0.01])
1773683801921684492 | /imu/data_raw | sensor_msgs/msg/Imu | Imu(header=Header(stamp=Time(sec=1773683801, nanosec=920380638), frame_id=imu_link), orientation=Quaternion(x=0.0, y=0.0, z=0.0, w=0.0), orientation_covariance=[-1.0, 0.0, 0.0, 0.0, 0.0, 0.0, 0.0, 0.0, 0.0], angular_velocity=Vector3(x=0.00390625, y=0.017578125, z=0.01171875), angular_velocity_covariance=[0.01, 0.0, 0.0, 0.0, 0.01, 0.0, 0.0, 0.0, 0.01], linear_acceleration=Vector3(x=-1.5703125, y=3.33203125, z=-9.26953125), linear_acceleration_covariance=[0.01, 0.0, 0.0, 0.0, 0.01, 0.0, 0.0, 0.0, 0.01])
1773683802028802082 | /imu/data_raw | sensor_msgs/msg/Imu | Imu(header=Header(stamp=Time(sec=1773683802, nanosec=27684120), frame_id=imu_link), orientation=Quaternion(x=0.0, y=0.0, z=0.0, w=0.0), orientation_covariance=[-1.0, 0.0, 0.0, 0.0, 0.0, 0.0, 0.0, 0.0, 0.0], angular_velocity=Vector3(x=-0.005859375, y=-0.009765625, z=-0.005859375), angular_velocity_covariance=[0.01, 0.0, 0.0, 0.0, 0.01, 0.0, 0.0, 0.0, 0.01], linear_acceleration=Vector3(x=-1.5703125, y=3.33203125, z=-9.26953125), linear_acceleration_covariance=[0.01, 0.0, 0.0, 0.0, 0.01, 0.0, 0.0, 0.0, 0.01])
1773683802113070111 | /imu/data_raw | sensor_msgs/msg/Imu | Imu(header=Header(stamp=Time(sec=1773683802, nanosec=111947759), frame_id=imu_link), orientation=Quaternion(x=0.0, y=0.0, z=0.0, w=0.0), orientation_covariance=[-1.0, 0.0, 0.0, 0.0, 0.0, 0.0, 0.0, 0.0, 0.0], angular_velocity=Vector3(x=0.001953125, y=0.005859375, z=0.0), angular_velocity_covariance=[0.01, 0.0, 0.0, 0.0, 0.01, 0.0, 0.0, 0.0, 0.01], linear_acceleration=Vector3(x=-1.5703125, y=3.37109375, z=-9.26953125), linear_acceleration_covariance=[0.01, 0.0, 0.0, 0.0, 0.01, 0.0, 0.0, 0.0, 0.01])
1773683802230802864 | /imu/data_raw | sensor_msgs/msg/Imu | Imu(header=Header(stamp=Time(sec=1773683802, nanosec=229669289), frame_id=imu_link), orientation=Quaternion(x=0.0, y=0.0, z=0.0, w=0.0), orientation_covariance=[-1.0, 0.0, 0.0, 0.0, 0.0, 0.0, 0.0, 0.0, 0.0], angular_velocity=Vector3(x=0.001953125, y=-0.001953125, z=-0.001953125), angular_velocity_covariance=[0.01, 0.0, 0.0, 0.0, 0.01, 0.0, 0.0, 0.0, 0.01], linear_acceleration=Vector3(x=-1.5703125, y=3.37109375, z=-9.26953125), linear_acceleration_covariance=[0.01, 0.0, 0.0, 0.0, 0.01, 0.0, 0.0, 0.0, 0.01])
1773683802328221522 | /imu/data_raw | sensor_msgs/msg/Imu | Imu(header=Header(stamp=Time(sec=1773683802, nanosec=327066908), frame_id=imu_link), orientation=Quaternion(x=0.0, y=0.0, z=0.0, w=0.0), orientation_covariance=[-1.0, 0.0, 0.0, 0.0, 0.0, 0.0, 0.0, 0.0, 0.0], angular_velocity=Vector3(x=0.00390625, y=-0.001953125, z=-0.001953125), angular_velocity_covariance=[0.01, 0.0, 0.0, 0.0, 0.01, 0.0, 0.0, 0.0, 0.01], linear_acceleration=Vector3(x=-1.5703125, y=3.37109375, z=-9.26953125), linear_acceleration_covariance=[0.01, 0.0, 0.0, 0.0, 0.01, 0.0, 0.0, 0.0, 0.01])
1773683802438386455 | /imu/data_raw | sensor_msgs/msg/Imu | Imu(header=Header(stamp=Time(sec=1773683802, nanosec=437217581), frame_id=imu_link), orientation=Quaternion(x=0.0, y=0.0, z=0.0, w=0.0), orientation_covariance=[-1.0, 0.0, 0.0, 0.0, 0.0, 0.0, 0.0, 0.0, 0.0], angular_velocity=Vector3(x=0.001953125, y=0.015625, z=0.01171875), angular_velocity_covariance=[0.01, 0.0, 0.0, 0.0, 0.01, 0.0, 0.0, 0.0, 0.01], linear_acceleration=Vector3(x=-1.5703125, y=3.37109375, z=-9.26953125), linear_acceleration_covariance=[0.01, 0.0, 0.0, 0.0, 0.01, 0.0, 0.0, 0.0, 0.01])
1773683802512687464 | /imu/data_raw | sensor_msgs/msg/Imu | Imu(header=Header(stamp=Time(sec=1773683802, nanosec=511442397), frame_id=imu_link), orientation=Quaternion(x=0.0, y=0.0, z=0.0, w=0.0), orientation_covariance=[-1.0, 0.0, 0.0, 0.0, 0.0, 0.0, 0.0, 0.0, 0.0], angular_velocity=Vector3(x=0.00390625, y=-0.00390625, z=0.0), angular_velocity_covariance=[0.01, 0.0, 0.0, 0.0, 0.01, 0.0, 0.0, 0.0, 0.01], linear_acceleration=Vector3(x=-1.5703125, y=3.37109375, z=-9.26953125), linear_acceleration_covariance=[0.01, 0.0, 0.0, 0.0, 0.01, 0.0, 0.0, 0.0, 0.01])
1773683802631446319 | /imu/data_raw | sensor_msgs/msg/Imu | Imu(header=Header(stamp=Time(sec=1773683802, nanosec=630322801), frame_id=imu_link), orientation=Quaternion(x=0.0, y=0.0, z=0.0, w=0.0), orientation_covariance=[-1.0, 0.0, 0.0, 0.0, 0.0, 0.0, 0.0, 0.0, 0.0], angular_velocity=Vector3(x=0.0, y=-0.005859375, z=-0.001953125), angular_velocity_covariance=[0.01, 0.0, 0.0, 0.0, 0.01, 0.0, 0.0, 0.0, 0.01], linear_acceleration=Vector3(x=-1.53125, y=3.33203125, z=-9.265625), linear_acceleration_covariance=[0.01, 0.0, 0.0, 0.0, 0.01, 0.0, 0.0, 0.0, 0.01])
1773683802727124935 | /imu/data_raw | sensor_msgs/msg/Imu | Imu(header=Header(stamp=Time(sec=1773683802, nanosec=726005306), frame_id=imu_link), orientation=Quaternion(x=0.0, y=0.0, z=0.0, w=0.0), orientation_covariance=[-1.0, 0.0, 0.0, 0.0, 0.0, 0.0, 0.0, 0.0, 0.0], angular_velocity=Vector3(x=-0.00390625, y=-0.009765625, z=-0.0078125), angular_velocity_covariance=[0.01, 0.0, 0.0, 0.0, 0.01, 0.0, 0.0, 0.0, 0.01], linear_acceleration=Vector3(x=-1.4921875, y=3.37109375, z=-9.34765625), linear_acceleration_covariance=[0.01, 0.0, 0.0, 0.0, 0.01, 0.0, 0.0, 0.0, 0.01])
1773683802827795210 | /imu/data_raw | sensor_msgs/msg/Imu | Imu(header=Header(stamp=Time(sec=1773683802, nanosec=826658672), frame_id=imu_link), orientation=Quaternion(x=0.0, y=0.0, z=0.0, w=0.0), orientation_covariance=[-1.0, 0.0, 0.0, 0.0, 0.0, 0.0, 0.0, 0.0, 0.0], angular_velocity=Vector3(x=0.001953125, y=0.005859375, z=0.00390625), angular_velocity_covariance=[0.01, 0.0, 0.0, 0.0, 0.01, 0.0, 0.0, 0.0, 0.01], linear_acceleration=Vector3(x=-1.53125, y=3.37109375, z=-9.265625), linear_acceleration_covariance=[0.01, 0.0, 0.0, 0.0, 0.01, 0.0, 0.0, 0.0, 0.01])
1773683802926994563 | /imu/data_raw | sensor_msgs/msg/Imu | Imu(header=Header(stamp=Time(sec=1773683802, nanosec=925995483), frame_id=imu_link), orientation=Quaternion(x=0.0, y=0.0, z=0.0, w=0.0), orientation_covariance=[-1.0, 0.0, 0.0, 0.0, 0.0, 0.0, 0.0, 0.0, 0.0], angular_velocity=Vector3(x=-0.001953125, y=-0.00390625, z=-0.005859375), angular_velocity_covariance=[0.01, 0.0, 0.0, 0.0, 0.01, 0.0, 0.0, 0.0, 0.01], linear_acceleration=Vector3(x=-1.53125, y=3.37109375, z=-9.265625), linear_acceleration_covariance=[0.01, 0.0, 0.0, 0.0, 0.01, 0.0, 0.0, 0.0, 0.01])
1773683803026059531 | /imu/data_raw | sensor_msgs/msg/Imu | Imu(header=Header(stamp=Time(sec=1773683803, nanosec=24944312), frame_id=imu_link), orientation=Quaternion(x=0.0, y=0.0, z=0.0, w=0.0), orientation_covariance=[-1.0, 0.0, 0.0, 0.0, 0.0, 0.0, 0.0, 0.0, 0.0], angular_velocity=Vector3(x=0.001953125, y=-0.001953125, z=0.001953125), angular_velocity_covariance=[0.01, 0.0, 0.0, 0.0, 0.01, 0.0, 0.0, 0.0, 0.01], linear_acceleration=Vector3(x=-1.53125, y=3.37109375, z=-9.265625), linear_acceleration_covariance=[0.01, 0.0, 0.0, 0.0, 0.01, 0.0, 0.0, 0.0, 0.01])
1773683803135082014 | /imu/data_raw | sensor_msgs/msg/Imu | Imu(header=Header(stamp=Time(sec=1773683803, nanosec=133996169), frame_id=imu_link), orientation=Quaternion(x=0.0, y=0.0, z=0.0, w=0.0), orientation_covariance=[-1.0, 0.0, 0.0, 0.0, 0.0, 0.0, 0.0, 0.0, 0.0], angular_velocity=Vector3(x=0.001953125, y=0.0, z=-0.001953125), angular_velocity_covariance=[0.01, 0.0, 0.0, 0.0, 0.01, 0.0, 0.0, 0.0, 0.01], linear_acceleration=Vector3(x=-1.53125, y=3.37109375, z=-9.265625), linear_acceleration_covariance=[0.01, 0.0, 0.0, 0.0, 0.01, 0.0, 0.0, 0.0, 0.01])
1773683803232769204 | /imu/data_raw | sensor_msgs/msg/Imu | Imu(header=Header(stamp=Time(sec=1773683803, nanosec=231649337), frame_id=imu_link), orientation=Quaternion(x=0.0, y=0.0, z=0.0, w=0.0), orientation_covariance=[-1.0, 0.0, 0.0, 0.0, 0.0, 0.0, 0.0, 0.0, 0.0], angular_velocity=Vector3(x=-0.00390625, y=-0.00390625, z=-0.00390625), angular_velocity_covariance=[0.01, 0.0, 0.0, 0.0, 0.01, 0.0, 0.0, 0.0, 0.01], linear_acceleration=Vector3(x=-1.53125, y=3.37109375, z=-9.265625), linear_acceleration_covariance=[0.01, 0.0, 0.0, 0.0, 0.01, 0.0, 0.0, 0.0, 0.01])
1773683803331607115 | /imu/data_raw | sensor_msgs/msg/Imu | Imu(header=Header(stamp=Time(sec=1773683803, nanosec=330480933), frame_id=imu_link), orientation=Quaternion(x=0.0, y=0.0, z=0.0, w=0.0), orientation_covariance=[-1.0, 0.0, 0.0, 0.0, 0.0, 0.0, 0.0, 0.0, 0.0], angular_velocity=Vector3(x=0.0, y=0.0, z=-0.001953125), angular_velocity_covariance=[0.01, 0.0, 0.0, 0.0, 0.01, 0.0, 0.0, 0.0, 0.01], linear_acceleration=Vector3(x=-1.53125, y=3.37109375, z=-9.265625), linear_acceleration_covariance=[0.01, 0.0, 0.0, 0.0, 0.01, 0.0, 0.0, 0.0, 0.01])
1773683803432137245 | /imu/data_raw | sensor_msgs/msg/Imu | Imu(header=Header(stamp=Time(sec=1773683803, nanosec=431016897), frame_id=imu_link), orientation=Quaternion(x=0.0, y=0.0, z=0.0, w=0.0), orientation_covariance=[-1.0, 0.0, 0.0, 0.0, 0.0, 0.0, 0.0, 0.0, 0.0], angular_velocity=Vector3(x=0.0, y=0.00390625, z=-0.001953125), angular_velocity_covariance=[0.01, 0.0, 0.0, 0.0, 0.01, 0.0, 0.0, 0.0, 0.01], linear_acceleration=Vector3(x=-1.53125, y=3.37109375, z=-9.265625), linear_acceleration_covariance=[0.01, 0.0, 0.0, 0.0, 0.01, 0.0, 0.0, 0.0, 0.01])
1773683803525371396 | /imu/data_raw | sensor_msgs/msg/Imu | Imu(header=Header(stamp=Time(sec=1773683803, nanosec=524233879), frame_id=imu_link), orientation=Quaternion(x=0.0, y=0.0, z=0.0, w=0.0), orientation_covariance=[-1.0, 0.0, 0.0, 0.0, 0.0, 0.0, 0.0, 0.0, 0.0], angular_velocity=Vector3(x=0.001953125, y=0.0, z=0.00390625), angular_velocity_covariance=[0.01, 0.0, 0.0, 0.0, 0.01, 0.0, 0.0, 0.0, 0.01], linear_acceleration=Vector3(x=-1.53125, y=3.37109375, z=-9.265625), linear_acceleration_covariance=[0.01, 0.0, 0.0, 0.0, 0.01, 0.0, 0.0, 0.0, 0.01])
1773683803637048116 | /imu/data_raw | sensor_msgs/msg/Imu | Imu(header=Header(stamp=Time(sec=1773683803, nanosec=635974624), frame_id=imu_link), orientation=Quaternion(x=0.0, y=0.0, z=0.0, w=0.0), orientation_covariance=[-1.0, 0.0, 0.0, 0.0, 0.0, 0.0, 0.0, 0.0, 0.0], angular_velocity=Vector3(x=-0.001953125, y=0.001953125, z=0.0), angular_velocity_covariance=[0.01, 0.0, 0.0, 0.0, 0.01, 0.0, 0.0, 0.0, 0.01], linear_acceleration=Vector3(x=-1.53125, y=3.37109375, z=-9.3046875), linear_acceleration_covariance=[0.01, 0.0, 0.0, 0.0, 0.01, 0.0, 0.0, 0.0, 0.01])
1773683803715348645 | /imu/data_raw | sensor_msgs/msg/Imu | Imu(header=Header(stamp=Time(sec=1773683803, nanosec=714236445), frame_id=imu_link), orientation=Quaternion(x=0.0, y=0.0, z=0.0, w=0.0), orientation_covariance=[-1.0, 0.0, 0.0, 0.0, 0.0, 0.0, 0.0, 0.0, 0.0], angular_velocity=Vector3(x=0.0, y=-0.00390625, z=-0.001953125), angular_velocity_covariance=[0.01, 0.0, 0.0, 0.0, 0.01, 0.0, 0.0, 0.0, 0.01], linear_acceleration=Vector3(x=-1.5703125, y=3.37109375, z=-9.26953125), linear_acceleration_covariance=[0.01, 0.0, 0.0, 0.0, 0.01, 0.0, 0.0, 0.0, 0.01])
1773683803831762154 | /imu/data_raw | sensor_msgs/msg/Imu | Imu(header=Header(stamp=Time(sec=1773683803, nanosec=830744667), frame_id=imu_link), orientation=Quaternion(x=0.0, y=0.0, z=0.0, w=0.0), orientation_covariance=[-1.0, 0.0, 0.0, 0.0, 0.0, 0.0, 0.0, 0.0, 0.0], angular_velocity=Vector3(x=0.0, y=0.0, z=0.001953125), angular_velocity_covariance=[0.01, 0.0, 0.0, 0.0, 0.01, 0.0, 0.0, 0.0, 0.01], linear_acceleration=Vector3(x=-1.53125, y=3.37109375, z=-9.265625), linear_acceleration_covariance=[0.01, 0.0, 0.0, 0.0, 0.01, 0.0, 0.0, 0.0, 0.01])
1773683803932415703 | /imu/data_raw | sensor_msgs/msg/Imu | Imu(header=Header(stamp=Time(sec=1773683803, nanosec=931296503), frame_id=imu_link), orientation=Quaternion(x=0.0, y=0.0, z=0.0, w=0.0), orientation_covariance=[-1.0, 0.0, 0.0, 0.0, 0.0, 0.0, 0.0, 0.0, 0.0], angular_velocity=Vector3(x=0.00390625, y=-0.0078125, z=-0.00390625), angular_velocity_covariance=[0.01, 0.0, 0.0, 0.0, 0.01, 0.0, 0.0, 0.0, 0.01], linear_acceleration=Vector3(x=-1.53125, y=3.37109375, z=-9.265625), linear_acceleration_covariance=[0.01, 0.0, 0.0, 0.0, 0.01, 0.0, 0.0, 0.0, 0.01])
1773683804026333971 | /imu/data_raw | sensor_msgs/msg/Imu | Imu(header=Header(stamp=Time(sec=1773683804, nanosec=25205495), frame_id=imu_link), orientation=Quaternion(x=0.0, y=0.0, z=0.0, w=0.0), orientation_covariance=[-1.0, 0.0, 0.0, 0.0, 0.0, 0.0, 0.0, 0.0, 0.0], angular_velocity=Vector3(x=0.00390625, y=0.0078125, z=0.00390625), angular_velocity_covariance=[0.01, 0.0, 0.0, 0.0, 0.01, 0.0, 0.0, 0.0, 0.01], linear_acceleration=Vector3(x=-1.53125, y=3.37109375, z=-9.265625), linear_acceleration_covariance=[0.01, 0.0, 0.0, 0.0, 0.01, 0.0, 0.0, 0.0, 0.01])
1773683804116247870 | /imu/data_raw | sensor_msgs/msg/Imu | Imu(header=Header(stamp=Time(sec=1773683804, nanosec=115111559), frame_id=imu_link), orientation=Quaternion(x=0.0, y=0.0, z=0.0, w=0.0), orientation_covariance=[-1.0, 0.0, 0.0, 0.0, 0.0, 0.0, 0.0, 0.0, 0.0], angular_velocity=Vector3(x=0.001953125, y=0.009765625, z=0.01171875), angular_velocity_covariance=[0.01, 0.0, 0.0, 0.0, 0.01, 0.0, 0.0, 0.0, 0.01], linear_acceleration=Vector3(x=-1.5703125, y=3.37109375, z=-9.26953125), linear_acceleration_covariance=[0.01, 0.0, 0.0, 0.0, 0.01, 0.0, 0.0, 0.0, 0.01])
1773683804237827647 | /imu/data_raw | sensor_msgs/msg/Imu | Imu(header=Header(stamp=Time(sec=1773683804, nanosec=236697967), frame_id=imu_link), orientation=Quaternion(x=0.0, y=0.0, z=0.0, w=0.0), orientation_covariance=[-1.0, 0.0, 0.0, 0.0, 0.0, 0.0, 0.0, 0.0, 0.0], angular_velocity=Vector3(x=-0.0078125, y=0.00390625, z=0.00390625), angular_velocity_covariance=[0.01, 0.0, 0.0, 0.0, 0.01, 0.0, 0.0, 0.0, 0.01], linear_acceleration=Vector3(x=-1.53125, y=3.37109375, z=-9.265625), linear_acceleration_covariance=[0.01, 0.0, 0.0, 0.0, 0.01, 0.0, 0.0, 0.0, 0.01])
1773683804316412408 | /imu/data_raw | sensor_msgs/msg/Imu | Imu(header=Header(stamp=Time(sec=1773683804, nanosec=315305842), frame_id=imu_link), orientation=Quaternion(x=0.0, y=0.0, z=0.0, w=0.0), orientation_covariance=[-1.0, 0.0, 0.0, 0.0, 0.0, 0.0, 0.0, 0.0, 0.0], angular_velocity=Vector3(x=-0.00390625, y=-0.0078125, z=-0.005859375), angular_velocity_covariance=[0.01, 0.0, 0.0, 0.0, 0.01, 0.0, 0.0, 0.0, 0.01], linear_acceleration=Vector3(x=-1.53125, y=3.37109375, z=-9.265625), linear_acceleration_covariance=[0.01, 0.0, 0.0, 0.0, 0.01, 0.0, 0.0, 0.0, 0.01])
1773683804435640020 | /imu/data_raw | sensor_msgs/msg/Imu | Imu(header=Header(stamp=Time(sec=1773683804, nanosec=434493524), frame_id=imu_link), orientation=Quaternion(x=0.0, y=0.0, z=0.0, w=0.0), orientation_covariance=[-1.0, 0.0, 0.0, 0.0, 0.0, 0.0, 0.0, 0.0, 0.0], angular_velocity=Vector3(x=-0.001953125, y=-0.00390625, z=-0.001953125), angular_velocity_covariance=[0.01, 0.0, 0.0, 0.0, 0.01, 0.0, 0.0, 0.0, 0.01], linear_acceleration=Vector3(x=-1.53125, y=3.37109375, z=-9.265625), linear_acceleration_covariance=[0.01, 0.0, 0.0, 0.0, 0.01, 0.0, 0.0, 0.0, 0.01])
1773683804532744409 | /imu/data_raw | sensor_msgs/msg/Imu | Imu(header=Header(stamp=Time(sec=1773683804, nanosec=531609209), frame_id=imu_link), orientation=Quaternion(x=0.0, y=0.0, z=0.0, w=0.0), orientation_covariance=[-1.0, 0.0, 0.0, 0.0, 0.0, 0.0, 0.0, 0.0, 0.0], angular_velocity=Vector3(x=0.0, y=0.005859375, z=0.001953125), angular_velocity_covariance=[0.01, 0.0, 0.0, 0.0, 0.01, 0.0, 0.0, 0.0, 0.01], linear_acceleration=Vector3(x=-1.53125, y=3.37109375, z=-9.265625), linear_acceleration_covariance=[0.01, 0.0, 0.0, 0.0, 0.01, 0.0, 0.0, 0.0, 0.01])
1773683804616368347 | /imu/data_raw | sensor_msgs/msg/Imu | Imu(header=Header(stamp=Time(sec=1773683804, nanosec=615236389), frame_id=imu_link), orientation=Quaternion(x=0.0, y=0.0, z=0.0, w=0.0), orientation_covariance=[-1.0, 0.0, 0.0, 0.0, 0.0, 0.0, 0.0, 0.0, 0.0], angular_velocity=Vector3(x=0.00390625, y=0.00390625, z=0.00390625), angular_velocity_covariance=[0.01, 0.0, 0.0, 0.0, 0.01, 0.0, 0.0, 0.0, 0.01], linear_acceleration=Vector3(x=-1.53125, y=3.37109375, z=-9.265625), linear_acceleration_covariance=[0.01, 0.0, 0.0, 0.0, 0.01, 0.0, 0.0, 0.0, 0.01])
1773683804728123165 | /imu/data_raw | sensor_msgs/msg/Imu | Imu(header=Header(stamp=Time(sec=1773683804, nanosec=727011042), frame_id=imu_link), orientation=Quaternion(x=0.0, y=0.0, z=0.0, w=0.0), orientation_covariance=[-1.0, 0.0, 0.0, 0.0, 0.0, 0.0, 0.0, 0.0, 0.0], angular_velocity=Vector3(x=-0.005859375, y=-0.0234375, z=-0.017578125), angular_velocity_covariance=[0.01, 0.0, 0.0, 0.0, 0.01, 0.0, 0.0, 0.0, 0.01], linear_acceleration=Vector3(x=-1.53125, y=3.37109375, z=-9.3046875), linear_acceleration_covariance=[0.01, 0.0, 0.0, 0.0, 0.01, 0.0, 0.0, 0.0, 0.01])
1773683804816530422 | /imu/data_raw | sensor_msgs/msg/Imu | Imu(header=Header(stamp=Time(sec=1773683804, nanosec=815407447), frame_id=imu_link), orientation=Quaternion(x=0.0, y=0.0, z=0.0, w=0.0), orientation_covariance=[-1.0, 0.0, 0.0, 0.0, 0.0, 0.0, 0.0, 0.0, 0.0], angular_velocity=Vector3(x=0.001953125, y=0.01171875, z=0.005859375), angular_velocity_covariance=[0.01, 0.0, 0.0, 0.0, 0.01, 0.0, 0.0, 0.0, 0.01], linear_acceleration=Vector3(x=-1.5703125, y=3.37109375, z=-9.2265625), linear_acceleration_covariance=[0.01, 0.0, 0.0, 0.0, 0.01, 0.0, 0.0, 0.0, 0.01])
1773683804935629337 | /imu/data_raw | sensor_msgs/msg/Imu | Imu(header=Header(stamp=Time(sec=1773683804, nanosec=934467302), frame_id=imu_link), orientation=Quaternion(x=0.0, y=0.0, z=0.0, w=0.0), orientation_covariance=[-1.0, 0.0, 0.0, 0.0, 0.0, 0.0, 0.0, 0.0, 0.0], angular_velocity=Vector3(x=0.001953125, y=0.00390625, z=0.00390625), angular_velocity_covariance=[0.01, 0.0, 0.0, 0.0, 0.01, 0.0, 0.0, 0.0, 0.01], linear_acceleration=Vector3(x=-1.53125, y=3.37109375, z=-9.3046875), linear_acceleration_covariance=[0.01, 0.0, 0.0, 0.0, 0.01, 0.0, 0.0, 0.0, 0.01])
1773683805031251150 | /imu/data_raw | sensor_msgs/msg/Imu | Imu(header=Header(stamp=Time(sec=1773683805, nanosec=30125973), frame_id=imu_link), orientation=Quaternion(x=0.0, y=0.0, z=0.0, w=0.0), orientation_covariance=[-1.0, 0.0, 0.0, 0.0, 0.0, 0.0, 0.0, 0.0, 0.0], angular_velocity=Vector3(x=-0.005859375, y=-0.013671875, z=-0.00390625), angular_velocity_covariance=[0.01, 0.0, 0.0, 0.0, 0.01, 0.0, 0.0, 0.0, 0.01], linear_acceleration=Vector3(x=-1.53125, y=3.37109375, z=-9.265625), linear_acceleration_covariance=[0.01, 0.0, 0.0, 0.0, 0.01, 0.0, 0.0, 0.0, 0.01])
1773683805131573983 | /imu/data_raw | sensor_msgs/msg/Imu | Imu(header=Header(stamp=Time(sec=1773683805, nanosec=130446972), frame_id=imu_link), orientation=Quaternion(x=0.0, y=0.0, z=0.0, w=0.0), orientation_covariance=[-1.0, 0.0, 0.0, 0.0, 0.0, 0.0, 0.0, 0.0, 0.0], angular_velocity=Vector3(x=0.001953125, y=0.0078125, z=0.005859375), angular_velocity_covariance=[0.01, 0.0, 0.0, 0.0, 0.01, 0.0, 0.0, 0.0, 0.01], linear_acceleration=Vector3(x=-1.53125, y=3.37109375, z=-9.265625), linear_acceleration_covariance=[0.01, 0.0, 0.0, 0.0, 0.01, 0.0, 0.0, 0.0, 0.01])
1773683805218143316 | /imu/data_raw | sensor_msgs/msg/Imu | Imu(header=Header(stamp=Time(sec=1773683805, nanosec=217030029), frame_id=imu_link), orientation=Quaternion(x=0.0, y=0.0, z=0.0, w=0.0), orientation_covariance=[-1.0, 0.0, 0.0, 0.0, 0.0, 0.0, 0.0, 0.0, 0.0], angular_velocity=Vector3(x=0.001953125, y=0.01171875, z=0.005859375), angular_velocity_covariance=[0.01, 0.0, 0.0, 0.0, 0.01, 0.0, 0.0, 0.0, 0.01], linear_acceleration=Vector3(x=-1.53125, y=3.37109375, z=-9.265625), linear_acceleration_covariance=[0.01, 0.0, 0.0, 0.0, 0.01, 0.0, 0.0, 0.0, 0.01])
1773683805337171733 | /imu/data_raw | sensor_msgs/msg/Imu | Imu(header=Header(stamp=Time(sec=1773683805, nanosec=336067391), frame_id=imu_link), orientation=Quaternion(x=0.0, y=0.0, z=0.0, w=0.0), orientation_covariance=[-1.0, 0.0, 0.0, 0.0, 0.0, 0.0, 0.0, 0.0, 0.0], angular_velocity=Vector3(x=0.005859375, y=-0.00390625, z=0.001953125), angular_velocity_covariance=[0.01, 0.0, 0.0, 0.0, 0.01, 0.0, 0.0, 0.0, 0.01], linear_acceleration=Vector3(x=-1.53125, y=3.37109375, z=-9.265625), linear_acceleration_covariance=[0.01, 0.0, 0.0, 0.0, 0.01, 0.0, 0.0, 0.0, 0.01])
1773683805415977911 | /imu/data_raw | sensor_msgs/msg/Imu | Imu(header=Header(stamp=Time(sec=1773683805, nanosec=414835788), frame_id=imu_link), orientation=Quaternion(x=0.0, y=0.0, z=0.0, w=0.0), orientation_covariance=[-1.0, 0.0, 0.0, 0.0, 0.0, 0.0, 0.0, 0.0, 0.0], angular_velocity=Vector3(x=-0.005859375, y=-0.00390625, z=-0.005859375), angular_velocity_covariance=[0.01, 0.0, 0.0, 0.0, 0.01, 0.0, 0.0, 0.0, 0.01], linear_acceleration=Vector3(x=-1.53125, y=3.37109375, z=-9.265625), linear_acceleration_covariance=[0.01, 0.0, 0.0, 0.0, 0.01, 0.0, 0.0, 0.0, 0.01])
1773683805535619569 | /imu/data_raw | sensor_msgs/msg/Imu | Imu(header=Header(stamp=Time(sec=1773683805, nanosec=534464370), frame_id=imu_link), orientation=Quaternion(x=0.0, y=0.0, z=0.0, w=0.0), orientation_covariance=[-1.0, 0.0, 0.0, 0.0, 0.0, 0.0, 0.0, 0.0, 0.0], angular_velocity=Vector3(x=0.00390625, y=-0.001953125, z=0.0), angular_velocity_covariance=[0.01, 0.0, 0.0, 0.0, 0.01, 0.0, 0.0, 0.0, 0.01], linear_acceleration=Vector3(x=-1.5703125, y=3.33203125, z=-9.26953125), linear_acceleration_covariance=[0.01, 0.0, 0.0, 0.0, 0.01, 0.0, 0.0, 0.0, 0.01])
1773683805631203653 | /imu/data_raw | sensor_msgs/msg/Imu | Imu(header=Header(stamp=Time(sec=1773683805, nanosec=630083940), frame_id=imu_link), orientation=Quaternion(x=0.0, y=0.0, z=0.0, w=0.0), orientation_covariance=[-1.0, 0.0, 0.0, 0.0, 0.0, 0.0, 0.0, 0.0, 0.0], angular_velocity=Vector3(x=0.001953125, y=0.009765625, z=0.0078125), angular_velocity_covariance=[0.01, 0.0, 0.0, 0.0, 0.01, 0.0, 0.0, 0.0, 0.01], linear_acceleration=Vector3(x=-1.53125, y=3.37109375, z=-9.265625), linear_acceleration_covariance=[0.01, 0.0, 0.0, 0.0, 0.01, 0.0, 0.0, 0.0, 0.01])
1773683805719192172 | /imu/data_raw | sensor_msgs/msg/Imu | Imu(header=Header(stamp=Time(sec=1773683805, nanosec=718040011), frame_id=imu_link), orientation=Quaternion(x=0.0, y=0.0, z=0.0, w=0.0), orientation_covariance=[-1.0, 0.0, 0.0, 0.0, 0.0, 0.0, 0.0, 0.0, 0.0], angular_velocity=Vector3(x=0.0, y=-0.001953125, z=-0.001953125), angular_velocity_covariance=[0.01, 0.0, 0.0, 0.0, 0.01, 0.0, 0.0, 0.0, 0.01], linear_acceleration=Vector3(x=-1.53125, y=3.37109375, z=-9.265625), linear_acceleration_covariance=[0.01, 0.0, 0.0, 0.0, 0.01, 0.0, 0.0, 0.0, 0.01])
1773683805821038960 | /imu/data_raw | sensor_msgs/msg/Imu | Imu(header=Header(stamp=Time(sec=1773683805, nanosec=819958546), frame_id=imu_link), orientation=Quaternion(x=0.0, y=0.0, z=0.0, w=0.0), orientation_covariance=[-1.0, 0.0, 0.0, 0.0, 0.0, 0.0, 0.0, 0.0, 0.0], angular_velocity=Vector3(x=0.0, y=0.0, z=0.0), angular_velocity_covariance=[0.01, 0.0, 0.0, 0.0, 0.01, 0.0, 0.0, 0.0, 0.01], linear_acceleration=Vector3(x=-1.53125, y=3.37109375, z=-9.265625), linear_acceleration_covariance=[0.01, 0.0, 0.0, 0.0, 0.01, 0.0, 0.0, 0.0, 0.01])
1773683805936601540 | /imu/data_raw | sensor_msgs/msg/Imu | Imu(header=Header(stamp=Time(sec=1773683805, nanosec=935503421), frame_id=imu_link), orientation=Quaternion(x=0.0, y=0.0, z=0.0, w=0.0), orientation_covariance=[-1.0, 0.0, 0.0, 0.0, 0.0, 0.0, 0.0, 0.0, 0.0], angular_velocity=Vector3(x=0.0, y=0.0, z=0.0), angular_velocity_covariance=[0.01, 0.0, 0.0, 0.0, 0.01, 0.0, 0.0, 0.0, 0.01], linear_acceleration=Vector3(x=-1.53125, y=3.37109375, z=-9.265625), linear_acceleration_covariance=[0.01, 0.0, 0.0, 0.0, 0.01, 0.0, 0.0, 0.0, 0.01])
1773683806018111576 | /imu/data_raw | sensor_msgs/msg/Imu | Imu(header=Header(stamp=Time(sec=1773683806, nanosec=17007977), frame_id=imu_link), orientation=Quaternion(x=0.0, y=0.0, z=0.0, w=0.0), orientation_covariance=[-1.0, 0.0, 0.0, 0.0, 0.0, 0.0, 0.0, 0.0, 0.0], angular_velocity=Vector3(x=0.0, y=0.0, z=0.0), angular_velocity_covariance=[0.01, 0.0, 0.0, 0.0, 0.01, 0.0, 0.0, 0.0, 0.01], linear_acceleration=Vector3(x=-1.5703125, y=3.37109375, z=-9.26953125), linear_acceleration_covariance=[0.01, 0.0, 0.0, 0.0, 0.01, 0.0, 0.0, 0.0, 0.01])
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
